Soundpauli/toern/toern.ino

#include "src/toern_build_types.h"

#define VERSION "v3.01f-T2"
extern "C" char *sbrk(int incr);
#define FASTLED_ALLOW_INTERRUPTS 0
// Sketch-local SERIAL8_*_BUFFER_SIZE defines do not resize HardwareSerial8.cpp.
// Real additional buffers are attached in setup(), including Arduino IDE builds.
#define TargetFPS 60

// Playback diagnostics / debug (keep OFF for reliability)
#define DEBUG_PLAYBACK_SERIAL 0  // set to 1 to enable extra playback Serial prints

// Forward declarations to keep Arduino's auto-prototype generator happy
// (it may emit function prototypes that reference these types before they are defined).
struct Mode;

//#define AUDIO_BLOCK_SAMPLES 128
//#define AUDIO_SAMPLE_RATE_EXACT 44100

//STILL FREE PINS: 24, 25, 22, 5, 15, 2, 4, 14, 9, 32, 33, 31
// CLK-OUT J25 = 37, CLK-IN J26 = 38, SIDEC J27 = 28 (rev H 5V analog I/O)
static const int FAST_DROP_BLOCKS = 5;  // ≈25ms @ 44100Hz with 128-sample blocks (reduced from 200ms to minimize trimming)
static int fastDropRemaining = 0;
volatile bool stepIsDue = false;
volatile uint32_t missedSteps = 0;  // counts when loop() hasn't consumed the previous tick yet

// Tiny timer ISR (definition is placed later in the file, after includes, to avoid Arduino
// auto-prototype issues with other callback signatures).
//void playTimerTick();

// === ISR -> main loop deferrals (keep timer interrupt fast and deterministic) ===
// NOTE: These are written from the timer ISR (playNote) and consumed in loop().
volatile bool isrPlayButtonTick = false;      // request drawPlayButton() from main loop (one per beat)
bool pendingPauseUIUpdate = false;            // deferred encoder/LED update after pause (avoid I2C stall)
bool pendingPauseSkipSave = false;            // whether the pending pause should skip autoSave
bool pendingPauseAutoSave = false;            // run autosave on a later loop tick (after pause UI)
volatile bool isrDbgPatternFinished = false;  // song-mode: pattern finished
volatile uint16_t isrDbgPatternFinishedBeat = 0;
volatile bool isrDbgLoopCountChanged = false;  // loopCount incremented
volatile uint16_t isrDbgLoopCountValue = 0;


//#include <Wire.h>x-

#include <cstring>  // For memcmp
#include "src/effect_freeverb_dmabuf.h"
#define USE_WS2812SERIAL   // leds
#include <WS2812Serial.h>  // leds

#include <FastLED.h>  // leds

#include <i2cEncoderLibV2.h>
#include <MIDI.h>
#include <Audio.h>
#include "src/toern_audio_runtime.h"
#include "src/toern_pcm_interpolation.h"
#include "src/toern_legacy_filter.h"
#include <EEPROM.h>
#include <FastTouch.h>
#include <sampler.h>  // TeensyPolyphony arraysampler API
// Adafruit_seesaw uses unqualified `byte`; disambiguate vs C++17 std::byte
#define byte uint8_t
#include "Adafruit_seesaw.h"
#undef byte

#include <Mapf.h>
#include "notes.h"
#include "colors.h"
#include "audioinit.h"
#include "font_3x5.h"
#include "icons.h"

// === Core types (must be defined early for Arduino auto-prototype generation) ===
enum ValueDisplayMode : uint8_t {
  DISPLAY_NUMERIC = 0,
  DISPLAY_ENUM = 1,
};

enum ParameterType : uint8_t {
  DELAY,
  ATTACK,
  HOLD,
  DECAY,
  SUSTAIN,
  RELEASE,
  WAVEFORM,
  TYPE,
};

enum FilterType : uint8_t {
  NULL_,
  HCUT,     // was PASS — same storage slot
  LOWCUT,   // was FREQUENCY — same storage slot
  REVERB,
  BITCRUSHER,
  DETUNE,
  OCTAVE,
  RES,
  RATE,
  AMOUNT,
  OFFSET,
  SPEED,
  PITCH,
  ACTIVE,
  EFX,
  FILTER_WAVEFORM,
};  // Define filter types

enum SynthTypes : uint8_t {
  INSTRUMENT,
  CUTOFF,
  RESONANCE,
  FILTER,
  CENT,
  SEMI,
  FORM,
  LFO_RATE,
  LFO_DEPTH,
  LFO_PHASE,  // repurposed as ARP_SPAN control for ch13/14
  ARP_STEP,
};  // Define synth types

enum MidiSetTypes : uint8_t {
  MIDI_IN_BOOL,
  MIDI_OUT_BOOL,
  SINGLE_OUT_CHANNEL,
  GLOBAL_IN_CHANNEL,
  SEND_CTRL_BOOL,
  RECEIVE_CTRL_BOOL,
};  // Define MIDI setting types

// Define which data array each slider uses
enum SettingArray : uint8_t { ARR_FILTER,
                              ARR_SYNTH,
                              ARR_PARAM,
                              ARR_NONE,
                              ARR_STRETCH };

// Define named struct for sliderDef
struct SliderDefEntry {
  SettingArray arr;
  int8_t idx;
  const char *name;
  uint8_t maxValue;
  uint8_t displayMode;
  const char **enumNames;
  uint8_t displayRange;
};

struct Note {
  uint8_t channel;      // 0 = no note; otherwise, channel / voice id
  uint8_t velocity;     // velocity (0-127)
  uint8_t probability;  // 0-100
  uint8_t condition;    // condition encoding (see codebase)
  uint8_t midiPitch;    // 0..127 = preserved MIDI input pitch; 255 = derive from grid row
} __attribute__((packed));
static_assert(sizeof(Note) == 5, "Note persistence layout must remain packed");

static constexpr uint8_t NOTE_MIDI_PITCH_NONE = 0xFF;
static constexpr uint8_t NOTE_CONDITION_FILL = 21;
static constexpr uint8_t NOTE_CONDITION_GLIDE = 22;
static constexpr uint8_t NOTE_CONDITION_STEP_COUNT = 11;
static const uint8_t noteConditionValues[NOTE_CONDITION_STEP_COUNT] PROGMEM = {
  1, 2, 4, 8, 16, 17, 18, 19, 20, NOTE_CONDITION_FILL, NOTE_CONDITION_GLIDE
};

#define LED_MODULES 2    // Max number of 16x16 matrices that can be chained (hardware limit)
#define MATRIX_WIDTH 16  // Width of each individual matrix
#define maxY 16
#define INT_SD 10

// maxX is now a runtime variable, calculated from ledModules menu setting
extern unsigned int maxX;
extern void handleMidiClock();
extern void handleStart();
#define NUM_LEDS (256 * LED_MODULES)  // 256 LEDs per matrix
#define DATA_PIN 17                   // PIN FOR LEDS
#define INT_PIN 27                    // PIN FOR ENOCDER INTERRUPS

#define SWITCH_1 2 // ALT: 16   // Capacitive input 1 >> SINGLE
#define SWITCH_2 3 // ALT: 3    // Capacitive input 2 >> MENU
#define BUTTON_A 5  // External SINGLE button, active LOW
#define BUTTON_B 22 // External MENU button, active LOW
#define SWITCH_3 4 // ALT: 41  //Pin for TPP223 2 >> REC /
#define SWITCH_4 6   // Capacitive touch4 >> current-voice audition (+ base-pitch note in SINGLE while playing)
#define SWITCH_5 39

// Battery sense on A16 with divider + capacitor.
// Rev G/H: R15 1M (top, VBAT->A16), R19 1.5M (bottom, A16->GND), plus smoothing cap.
#define BATT_ADC_PIN A16
#define BATT_RAW_ZERO 4           // raw reading when pin connected to GND (0V)
#define BATT_RAW_FULL 4095        // raw at 3.3V at pin (12-bit max)
// Nominal divider 1.5/(1.0+1.5)=0.600. Recalibrated on device: meter 4.125V
// read 87% with 0.577 (fw ~4.04V); 0.565 brings that sample to ~4.125V.
#define BATT_DIVIDER_RATIO 0.565f
#define BATT_V_MIN 3.30f          // Display 0% at 3.30V
#define BATT_V_MAX 4.125f         // Display 100% at measured full pack
#define BATT_PCT_CURVE 1.0f       // Linear voltage→%

#define VOL_MIN 1
#define VOL_MAX 10
#define LINEOUT_MIN 13  // SGTL5000 line-out valid range (datasheet: 13..31)
#define LINEOUT_MAX 31
#define BPM_MIN 40
#define BPM_MAX 300

#define GAIN_1 0.4  //0.1;
#define GAIN_2 0.8  //0.33 (increased to 0.8 for 64% total gain)
#define GAIN_3 0.4  //0.25
#define GAIN_4 0.8  //0.2; (increased to 0.8 for 64% total gain)

// ---- Mix headroom (samples ch1-8) ----
// These stages are where hard clipping/crackling happens if too hot:
// - mixer1 sums ch1-4
// - mixer2 sums ch5-8
// - mixer_end sums mixer1 + mixer2 (+ synth + monitoring)
//
// Hard limit per bus: N * MIX_BUS_HEADROOM <= 1.0 (N simultaneous voices on that bank, each at
// full internal level in phase — the theoretical "block" + max velocity case).
// Eight voices total does NOT relax N: e.g. six voices can still be 4+2, so N is still 4 on one bus.
//
// We target typical use: at most 3 sample voices on ch1-4 at once AND at most 3 on ch5-8 (e.g. 3+3=6).
// Then MIX_BUS_HEADROOM = 1/3 keeps each bus <= 1.0; mixer_end still needs 2 * MIX_END <= 1.0.
// If you ever fire 4 samples on one bank at full level together, lower MIX_BUS_HEADROOM to 0.25f.
#define MIX_BUS_HEADROOM (1.0f / 3.0f)  // max ~3 simultaneous sample voices per bank (ch1-4 / ch5-8)
#define MIX_END_SAMPLES_GAIN 0.50f      // mixer_end: mixer1 + mixer2 (each bus can hit 1.0)
#define MIX_END_SYNTH_GAIN 0.60f    // mixer_end input gain for mixersynth_end
// VOL→GAIN: stored 0..20 tenths (UI 0.0–2.0), 10 = current staging (1.0×). Bus × master, so 2.0×2.0 = 4×.
#define MIX_GAIN_UNITY 10
#define MIX_GAIN_MAX 20
#define EEPROM_MIX_GAIN_14 38
#define EEPROM_MIX_GAIN_58 39
#define EEPROM_MIX_GAIN_SYN 40
#define EEPROM_MIX_GAIN_ALL 41


#define NUM_ENCODERS 4
#define defaultVelocity 100
#define FOLDER_MAX 10

#define maxPages 16
#define maxFiles 9
#define NUM_CHANNELS 16
#define maxFilters 15

#define maxfilterResolution 32.0
#define numPulsesForAverage 8  // Number of pulses to average over
#define pulsesPerBar (24 * 4)  // 24 pulses per quarter note, 4 quarter notes per bar

#define EEPROM_MENU_ADDR 42

// Dynamic sample browser (toern_helpers.ino)
extern void sampleBrowserRefreshList(int channel);
extern void sampleBrowserSyncBrowseFromStoredPath(int channel);
extern void sampleBrowserNavigatePress(int channel);
extern void sampleBrowserLastEncoderPress(int channel);
extern void sampleBrowserGoUpPress(int channel);
extern void sampleBrowserClampBrowseIndexAndHardware(int channel);
extern int sampleBrowserBrowseIndexMax(int channel);
extern unsigned long g_setWavIgnoreLoadUntilMs;
extern bool sampleBrowserIsLoadableSelection(int channel);
extern bool shouldSkipVoiceTriggerForSyncPreview(int ch);
extern void triggerSetWavSyncPreview(uint8_t vel);
extern void previewSample(bool setMaxSampleLength);
extern void previewSample(bool setMaxSampleLength, bool playAudio);
extern void previewSampleNow();
extern void serviceSetWavSyncPreview();
extern void serviceSdPreviewRequests();
extern uint16_t g_wavPickCount;
extern uint16_t g_folderPickCount;

struct MidiSettings : public midi ::DefaultSettings {
  static const long BaudRate = 31250;
  static const unsigned SysExMaxSize = 16;
};

MIDI_CREATE_CUSTOM_INSTANCE(HardwareSerial, Serial8, MIDI, MidiSettings);
static uint8_t midiTxExtra[128];
static uint8_t midiRxExtra[512];

unsigned long ganularStartTime = 0;  // Timestamp when the current beat started

#define EXTERNAL_ONE_ENCODER_INDEX 2  // Encoder(2) -> third hardware knob
static bool externalOneBlinkActive = false;
static unsigned long externalOneBlinkUntil = 0;

// Input monitoring toggle state: 0=off, 1=on (y==1 only), 2=all (always on)
// 0 = OFF (dark white helper LEDs)
// 1 = ON (dark green helper LEDs, only when y==1)
// 2 = ALL (dark yellow helper LEDs, always on regardless of y position)
int inputMonitoringState = 0;

void triggerExternalOneBlink();
void updateExternalOneBlink();
void updatePreviewVolume();

#define CLOCK_BUFFER_SIZE 24
//elapsedMillis recFlushTimer;
elapsedMillis recTime;

extern i2cEncoderLibV2 Encoder[NUM_ENCODERS];

bool showChannelNr = true;
bool lastPinsConnected = false;
unsigned long lastChangeTime = 0;
const unsigned long debounceDelay = 500;  // 100ms debounce

#define EEPROM_MAGIC_ADDR 42
#define EEPROM_DATA_START 43        // 43..48 will be your six mode‐bytes
const uint8_t EEPROM_MAGIC = 0x5A;  // anything nonzero


// Add at file scope:

// Extern declarations for menu system
extern int currentMenuPage;

// Function declarations for per-page mute system
bool getMuteState(int channel);
bool getMuteStateForUI(int channel);  // Get mute state for UI display (uses edit page)
void setMuteState(int channel, bool muted);
bool isChildVoiceDisabled(int channel);
bool isChildVoiceMuted(int channel);
void enforceChildModeRestrictions();
void applyMutesAfterPMODSwitch();

// DRAW-R fullMute: stay in draw/single; enc1 enter/exit; enc2/3/4 toggle views in-mode.
enum class FullMuteView : uint8_t { AllMuted = 0, Ch12, Custom, UnmuteAll };

void fullMuteEnter();
void fullMuteExitRestore();
void fullMuteToggleView(FullMuteView target);
void fullMuteApplyView();
bool fullMuteIsActive();
void savePageMutesToGlobal();
void loadGlobalMutesToPage();
void initPageMutes();
void drawIndicator(char size, char colorCode, int encoderNum, bool highlight = false, bool setEncoderLed = true);
void drawFullMuteBorder();
void drawFullMuteIndicators();
void getIndicatorXPositions(int encoderNum, int &x1, int &x2, int &x3);
void updatePongBall();
void drawPongBall();
void resetPongGame();
void showSaveSuccessAnimation(bool returnToDraw = true);
void triggerGridNote(unsigned int globalX, unsigned int y, bool allowMuted = false);
int mapXtoPageOffset(int x);
void stopSound(int note, int ch);
void playSound(int note, int ch, int velocity);
void playSequencedSound(int note, int ch, int velocity, uint32_t tick,
                        bool allowLegato);
void finishSequencedSoundTick(uint32_t tick, bool hadNotes);
void resetSequencedSynthLegato();
void playSequencedSynth(int ch, int b, int vel, uint32_t tick,
                        bool allowLegato, int midiPitchOverride);
void finishSequencedMonoSynthTick(uint32_t tick, bool had13, bool had14);
void stopSynthChannel(int ch);
static inline void resetMidiPressedKeyCount11to14();
void drawCtrlVolumeOverlay(int volume);
void initNeoSlider();
void updateNeoSliderVolume();
void reapplyAllSampleChannelGains();
void resetAllChannelVolumesToDefault();
void extendLastPageForLiveNote(uint16_t targetBeat);
void updateLastPage();
void triggerSamplerVoice(int ch, int pitch, int vel, bool retrigger);
uint8_t scaledNoteVelocity(int ch, int vel);
void updateAllMixerGains();
void forceAllMixerGainsToTarget();
void drawInputGainOverlay(int gain, int maxGain);
void drawChannelNrOverlay(int channelNum, int channelIdx);
void drawPageNrOverlay(int pageNum);
void drawSampleLoadOverlay(uint8_t progressPercent);
bool loadPreviewToChannel(unsigned int targetChannel, bool showLoadProgress = false);
void copySampleToSamplepack0(unsigned int channel, bool showLoadProgress = false);
void saveSp0StateToEEPROM();
void saveSingleModeToEEPROM(int index, int8_t value);
FLASHMEM void flushSettingsBackupNow();
void stopAllSetWavPreviewAudio();
void stopSdPreviewIfPlaying();
void beginChannelSampleReload(unsigned int ch);
void endChannelSampleReload(unsigned int ch);
bool isChannelSampleReloadBusy(unsigned int ch);
size_t sdIoChunkSize();
void sdIoYield();
void sdIoBeginAudioSafe();
void sdIoEndAudioSafe();
bool soloRandomPickPath(char* outRel, size_t outRelSize);
bool soloRandomRenewPlaylist();
bool soloRandomStepPlaylist(int delta);
bool soloRandomBuildPlayPath(const char* stored, char* out, size_t outSz);
bool soloRandomIsPlayableWav(const char* fullPath);
void soloRandomCommitPathToChannel(int ch, const char* fullSdPath);
void soloRandomDropCurrentEntry();
void soloRandomPreviewCurrentVoice();
void soloRandomStepAndPreview(int delta);
const char* soloRandomGetLastPreviewPath();
void soloRandomLoadLastPreview();
static int16_t lastDefaultFastFilterValue[NUM_CHANNELS] = { 0 };  // Changed from int to int16_t (32 bytes saved)

const char *const instTypeNames[] PROGMEM = { "BASS", "KEYS", "CHPT", "PAD", "WOW", "ORG", "FLT", "LEAD", "ARP", "BRSS" };
#define INST_ENUM_COUNT (sizeof(instTypeNames) / sizeof(instTypeNames[0]))

// Add at file scope, after instTypeNames[]
const char *const sndTypeNames[] PROGMEM = { "SAMP" };
const char *const waveformNames[] PROGMEM = { "SIN", "SQR", "SAW", "TRI" };

struct SliderMeta {
  uint8_t maxValue;        // physical encoder range, e.g. 16
  uint8_t displayMode;     // enum or numeric
  const char **enumNames;  // for DISPLAY_ENUM
  uint8_t displayRange;    // NEW: number of distinct display values (e.g. 5, 3)
};


static const SliderMeta sliderMeta[4][4] = {
  // Page 0
  {
    { 32, DISPLAY_NUMERIC, nullptr, 32 },
    { 32, DISPLAY_NUMERIC, nullptr, 32 },
    { 32, DISPLAY_NUMERIC, nullptr, 32 },
    { 32, DISPLAY_NUMERIC, nullptr, 32 } },
  // Page 1
  {
    { 32, DISPLAY_NUMERIC, nullptr, 32 },
    { 32, DISPLAY_NUMERIC, nullptr, 32 },
    { 32, DISPLAY_NUMERIC, nullptr, 32 },
    { 32, DISPLAY_NUMERIC, nullptr, 32 } },
  // Page 2
  {
    { 16, DISPLAY_NUMERIC, nullptr, 5 },     // Shown as 0–4
    { 9, DISPLAY_ENUM, instTypeNames, 10 },  // Mapped from 0–9
    { 32, DISPLAY_NUMERIC, nullptr, 32 },
    { 32, DISPLAY_NUMERIC, nullptr, 32 } },
  // Page 3
  {
    { 32, DISPLAY_NUMERIC, nullptr, 32 },
    { 32, DISPLAY_NUMERIC, nullptr, 32 },
    { 32, DISPLAY_NUMERIC, nullptr, 32 },
    { 32, DISPLAY_NUMERIC, nullptr, 32 } }
};


struct PendingNoteEvent {
  uint8_t channel;
  uint8_t pitch;
  uint8_t velocity;
  unsigned long triggerTime;  // when to trigger
};

std::vector<PendingNoteEvent> pendingSampleNotes;

struct CachedSample {
  char pathRel[128];
  uint32_t lengthBytes;
  uint8_t rate;
  bool valid;
  int plen;
};

CachedSample previewCache;

// Flag to disable threshold from external code
bool disableThresholdFlag = false;

// Number of samples in each delay line
// Allocate the delay lines for left and right channels

bool MIDI_CLOCK_SEND = true;
bool MIDI_NOTE_SEND = true;    // Control whether MIDI notes are sent (independent from clock)
bool MIDI_NOTE_RECEIVE = true; // Control whether incoming MIDI notes are acted on
bool MIDI_NOTE_CLAMP = true;   // Fold incoming pitch into rows 1..15; OFF preserves absolute MIDI pitch

bool MIDI_TRANSPORT_RECEIVE = true;
bool MIDI_TRANSPORT_SEND = false;
int8_t transportSendDelayMs = 17;   // -127..+127 ms, MENU>MIDI>SYNC SNC1 (see toern_midi effective* helpers)
int8_t transportRcveDelayMs = 17; // -127..+127 ms SNC2: + = delay that path; − = delay the other path
bool MIDI_VOICE_SELECT = false;
bool SMP_PATTERN_MODE = false;
bool SMP_FLOW_MODE = false;      // FLOW mode: follows timer position when playing
bool voiceMode = false;          // VMOD: each channel loops its own pages
bool imageMode = false;          // IMG: black matrix; paint cycles voice/color from voice1
int imgBrushChannel = 1;         // IMG: selected brush voice/color (1–8); touch1 cycles
uint8_t eyesMode = 1;            // ETC EYES: 0=OFF, 1=1min, 2=5min, 3=15min idle before screensaver
uint8_t fireVoice = 0;           // ETC FIRE: 0 off, 15 all voices, else 1–8 / 11 / 13 / 14
uint8_t fireLevel = 8;           // ETC FIRE: encoder 2 particle count, 1–25
uint8_t fireSize = 1;            // ETC FIRE: encoder 1 particle size, 1–4
uint8_t fireGravity = 0;         // ETC FIRE: 0 drifts sideways, 8 pulls hard toward playhead
uint8_t fireColor = 8;           // ETC FIRE: 0 white, 8 full voice colour
uint8_t fireFocus = 0;           // encoder 3 edits 0 voice, 1 gravity, 2 colour
uint8_t voicePageLen[16] = {0};  // highest page that contains this channel (0 = empty)
uint16_t voicePageMask[16] = {0};
uint16_t voiceRowMask[16] = {0}; // bit (row-1) if this channel has any note on that row
uint8_t voiceModePages = 1;      // longest voice, at least 1
uint16_t voiceLoopCount[16] = {0};
uint8_t voiceEditPage[16] = {0}; // per-voice edit page (2nd encoder), 0 = page 1
int8_t voicePageOffset[16] = {0}; // added to the global page so the 2nd encoder can cue one voice
static bool spkrEnabled = true;  // SPKR toggle state (ON by default)
static bool childLockEnabled = false;  // Child lock: requires touch2->touch1 sequence to enter menu
static bool bootFullResetRequested = false;  // Touch1 held 10s at power-on (3s CLR + 7s more) → FULL reset late in setup()
unsigned int lastFlowPage = 0;   // Track the last page set by FLOW mode
bool recMenuFirstEnter = true;   // Track first entry into REC menu
unsigned int SMP_FAST_REC = false;
unsigned int SMP_REC_CHANNEL_CLEAR = true;
bool SMP_LOAD_SETTINGS = true;  // Whether to load SMP settings when loading tracks
uint8_t lineOutLevelSetting = 30;

bool pendingStartOnBar = false;  // "I hit Play, now wait for bar-1"



bool drawNoSD_hasRun = false;


struct PendingNote {
  uint8_t pitch;
  uint8_t velocity;
  uint8_t channel;
  uint8_t livenote;
  uint16_t targetBeat;
};

// A small FIFO for upcoming grid-writes.
// IMPORTANT: `playNote()` runs in an IntervalTimer ISR, so this queue must be ISR-safe.
// Use a fixed-size single-producer (loop/MIDI) single-consumer (ISR/onBeatTick) ring buffer.
static constexpr uint8_t MAX_PENDING_NOTES = 32;
DMAMEM static PendingNote pendingNotesBuf[MAX_PENDING_NOTES];
static volatile uint8_t pendingNotesHead = 0;   // next write index
static volatile uint8_t pendingNotesTail = 0;   // next read index
static volatile uint8_t pendingNotesCount = 0;  // number of queued items

// If a live MIDI/touch4 write lands on the upcoming sequencer step, skip that
// one trigger so the immediate preview is the only attack. The cell is already
// on the grid (visible now) and plays on the next pass.
volatile uint16_t liveRecordSkipBeat = 0;
volatile uint16_t liveRecordSkipRows = 0;

// Enqueue from main loop context (may be called from MIDI handlers in loop()).
// Returns true on success, false if the queue is full (event dropped).
bool enqueuePendingNote(uint8_t pitch, uint8_t velocity, uint8_t channel, uint8_t livenote) {
  if (isChildVoiceDisabled((int)channel)) return false;
  extern uint16_t quantizedMidiRecordBeat();
  uint16_t targetBeat = quantizedMidiRecordBeat();

  bool ok = false;
  noInterrupts();
  if (pendingNotesCount < MAX_PENDING_NOTES) {
    pendingNotesBuf[pendingNotesHead] = {
      pitch, velocity, channel, livenote, targetBeat
    };
    pendingNotesHead = (uint8_t)((pendingNotesHead + 1) % MAX_PENDING_NOTES);
    pendingNotesCount++;
    ok = true;
  }
  interrupts();
  return ok;
}

// Dequeue from ISR context (`onBeatTick()` runs inside `playNote()` ISR).
// Returns true if an item was dequeued.
bool dequeuePendingNote(PendingNote &out) {
  if (pendingNotesCount == 0) return false;
  out = pendingNotesBuf[pendingNotesTail];
  pendingNotesTail = (uint8_t)((pendingNotesTail + 1) % MAX_PENDING_NOTES);
  pendingNotesCount--;
  return true;
}

void clearPendingMidiRecordNotes() {
  noInterrupts();
  pendingNotesHead = 0;
  pendingNotesTail = 0;
  pendingNotesCount = 0;
  liveRecordSkipBeat = 0;
  liveRecordSkipRows = 0;
  interrupts();
}

static void markLiveRecordSkip(uint16_t targetBeat, uint8_t row) {
  extern unsigned int beat;
  noInterrupts();
  uint16_t upcoming = (uint16_t)beat;
  if (targetBeat == upcoming && row >= 1 && row <= 15) {
    if (liveRecordSkipBeat != targetBeat) {
      liveRecordSkipBeat = targetBeat;
      liveRecordSkipRows = 0;
    }
    liveRecordSkipRows |= (uint16_t)(1u << row);
  }
  interrupts();
}

static bool consumeLiveRecordSkip(uint16_t srcBeat, unsigned int row) {
  if (liveRecordSkipBeat != srcBeat || row > 15) return false;
  uint16_t bit = (uint16_t)(1u << row);
  if ((liveRecordSkipRows & bit) == 0) return false;
  liveRecordSkipRows = (uint16_t)(liveRecordSkipRows & ~bit);
  if (liveRecordSkipRows == 0) liveRecordSkipBeat = 0;
  return true;
}

// Write a live-recorded note immediately so SINGLE/DRAW can show it, without
// waiting for the next sequencer tick. Skip-once covers the current playhead.
bool placeLiveGridNote(uint8_t channel, uint8_t row, uint8_t velocity,
                       uint8_t midiPitch, bool protectOtherVoices) {
  extern Note note[][maxY + 1];
  if (channel < 1 || row < 1 || row > 15) return false;
  if (isChildVoiceDisabled((int)channel)) return false;
  extern uint16_t quantizedMidiRecordBeat();
  uint16_t targetBeat = quantizedMidiRecordBeat();
  if (targetBeat < 1) return false;
  Note &cell = note[targetBeat][row];
  if (protectOtherVoices && cell.channel != 0 && cell.channel != channel) {
    return false;
  }
  markLiveRecordSkip(targetBeat, row);
  cell.velocity = velocity > 0 ? velocity : (uint8_t)defaultVelocity;
  cell.probability = 100;
  cell.condition = 1;
  cell.midiPitch = midiPitch;
  cell.channel = channel;
  // Do not full-scan EXTMEM here: updateLastPage() briefly publishes lastPage=0
  // (and understated mid-scan values) that the playNote ISR can treat as a wrap
  // to beat 1 when many MIDI notes land while playing.
  extendLastPageForLiveNote(targetBeat);
  return true;
}


// ----- Intro Animation Timing (in ms) -----
// Boot: 1s sine fade-in, 2.5s logo fade-in, 1.5s combined fade-out = 5s.
const unsigned long phase1Duration = 1000;
const unsigned long phase2Duration = 2500;
const unsigned long phase3Duration = 1500;
const unsigned long totalAnimationTime =
    phase1Duration + phase2Duration + phase3Duration;
bool filterfreshsetted = true;

DMAMEM bool activeNotes[128] = { false };  // Track active MIDI notes (0-127)
DMAMEM int16_t midiHeldCh11SoundNote[128] = {}; // Exact live voice identity for matching Note Off
DMAMEM uint8_t sequencerMidiOutPitch[16] = {};
DMAMEM uint8_t sequencerMidiOutChannel[16] = {};
uint8_t sequencerMidiOutCount = 0;

float rateFactor = 44117.0 / 44100.0;


unsigned int infoIndex = 0;

// Sample paths for SP0 / SET_WAV are stored in SMP.samplePathRel[] (relative to samples/).
bool freshPaint, tmpMute = false;
bool preventPaintUnpaint = false;  // Flag to prevent paint/unpaint after certain operations
unsigned long suppressDrawRMuteUntilMs = 0;  // Ignore R-mode mute events during velocity enter/exit


bool firstcheck = false;
bool nofile = false;
char *currentParam = "DLAY";
char *currentFilter = "TYPE";
char *currentSynth = "BASS";
unsigned int fxType = 0;

unsigned int selectedFX = 0;


unsigned long filterDrawEndTime = 0;
bool filterDrawActive = false;
int filterDrawValue = 0;
CRGB filterDrawColor = CRGB::White;


unsigned long patternChangeTime = 0;
bool patternChangeActive = false;



// Replaced String with hash for memory efficiency (~100-200 bytes saved)
uint32_t oldPosHash = 0;
uint8_t oldButtons[NUM_ENCODERS] = { 0, 0, 0, 0 };  // Changed from int to uint8_t (4 bytes saved per element)

unsigned long playStartTime = 0;  // To track when play(true) was last called

bool previewIsPlaying = false;
extern bool g_previewUseLivePeaks;

const int maxPeaks = 512;  // Adjust based on your needs
DMAMEM float peakValues[maxPeaks];
int peakIndex = 0;


const int maxRecPeaks = 512;  // Adjust based on your needs
DMAMEM float peakRecValues[maxRecPeaks];
int peakRecIndex = 0;



uint8_t ledBrightness = 83;
bool drawBaseColorMode = true;  // true = channel colors, false = black
bool pong = false;
const long ram = 15728640;                               // 15MB EXTRAM for sounds (was 12582912/12MB); ~1707KB/slot ~19.8s/voice @ 44.1kHz mono 16-bit
const unsigned int MAX_STEPS = MATRIX_WIDTH * maxPages;  // Fixed total steps (16 pages * 16 cols = 256)
const unsigned int maxlen = MAX_STEPS + 1;               // Note array width (1-based)
const unsigned int SONG_LEN = MAX_STEPS;                 // Song length equals total steps

static bool lastBothTouched = false;
DMAMEM bool touchState[4] = { false };      // Current touch state (HIGH/LOW)
DMAMEM bool lastTouchState[4] = { false };  // Previous touch state
const int touchThreshold = 45; //45 for M1
// Rec (SWITCH_3) is polled every tight-loop tick while FastRec is active.
// Debounce in time at the same threshold as the other pads — a wide Schmitt
// (OFF=28) never unlatched because idle FastTouch often sits at 30–44.
static const unsigned long REC_TOUCH_PRESS_MS = 20;
static const unsigned long REC_TOUCH_RELEASE_MS = 40;
static bool bypassModeSwitchDebounce = false;
static bool touch1ModeTogglePending = false;
static bool touch1ModeToggleToSingle = false;
static unsigned long touch1ModeToggleDueMs = 0;
static const unsigned long TOUCH1_CHORD_GRACE_MS = 140;

/** true: use grounded buttons A/B; false: use capacitive SWITCH_1/2. */
static const bool exttouch = false;
/** When false, skip all NeoSlider I2C (init/ADC/LEDs/slew). This unit has faders. */
static const bool deviceHasFaders = exttouch;

bool readTouch1Pressed() {
  if (exttouch) return digitalReadFast(BUTTON_A) == LOW;
  return fastTouchRead(SWITCH_1) > touchThreshold;
}

bool readTouch2Pressed() {
  if (exttouch) return digitalReadFast(BUTTON_B) == LOW;
  return fastTouchRead(SWITCH_2) > touchThreshold;
}

bool readRecTouchHeld() {
  static bool latched = false;
  static bool timing = false;
  static unsigned long disagreeSince = 0;
  const bool raw = fastTouchRead(SWITCH_3) > touchThreshold;
  const unsigned long now = millis();
  if (raw == latched) {
    timing = false;
    return latched;
  }
  if (!timing) {
    timing = true;
    disagreeSince = now;
  }
  const unsigned long need = latched ? REC_TOUCH_RELEASE_MS : REC_TOUCH_PRESS_MS;
  if ((now - disagreeSince) >= need) {
    latched = raw;
    timing = false;
  }
  return latched;
}

const unsigned int totalPulsesToWait = pulsesPerBar * 2;

const unsigned long CHECK_INTERVAL = 50;  // Interval to check buttons in ms
unsigned long lastCheckTime = 0;          // Get the current time


// Recording input mode:
//   1  = MIC (SGTL5000 capture/mic path enabled)
//  -1  = LINEIN (MIC/capture path disabled)
int recMode = -1;
unsigned int fastRecMode = 0;
unsigned int previewVol = 20;  // Default 20 (0-50 range, 0.00-0.50)
uint8_t mixGain14 = MIX_GAIN_UNITY;     // VOL→GAIN: mixer1 (voices 1–4)
uint8_t mixGain58 = MIX_GAIN_UNITY;     // mixer2 (voices 5–8)
uint8_t mixGainSynth = MIX_GAIN_UNITY;  // mixer_end synth bus (ch11/13/14)
uint8_t mixGainMaster = MIX_GAIN_UNITY; // scales 1–4, 5–8, and synth together
// Preview trigger mode: 0 = auto on selection/seek, 1 = encoder(0) press only, 2 = in-sync with voice triggers
extern const int PREVIEW_MODE_ON = 0;
extern const int PREVIEW_MODE_PRESS = 1;
extern const int PREVIEW_MODE_SYNC = 2;
int previewTriggerMode = PREVIEW_MODE_ON;
int recChannelClear = 1;  // 0=OFF (add triggers), 1=ON (clear then add), 2=FIX (no manipulation), 3=ON1 (count-in then record on beat 1), 4=CLIC (touch3 adds trigger at current beat)
int transportMode = 1;
int midiSendMode = 2;  // 0=CLCK, 1=NOTE, 2=BOTH (default to BOTH)
int patternMode = -1;
int flowMode = -1;  // FLOW setting: -1 = OFF, 1 = ON
int clockMode = 1;
int voiceSelect = 1;
int simpleNotesView = 1;               // Simple notes view: 1=EASY, 2=FULL
int loopLength = 0;                    // Loop length: 0=OFF, 1-8=force pattern length
int ledModules = 1;                    // Number of LED modules: 1 or 2
bool ledModulesRotated = false;        // LED panel orientation flag: false=normal, true=rotated compensation
unsigned int maxX = MATRIX_WIDTH * 1;  // Runtime variable: total display width (16 or 32)
unsigned int micGain = 0;              // Microphone gain: 0-64, default 10
unsigned int lineInLevel = 8;          // Line input level: 0-15, default 8
int ctrlMode = 0;                      // 0=page, 1=volume control for encoder 1
static int ctrlLastChannel = -1;
static int ctrlLastVolume = -1;
static bool ctrlVolumeOverlayActive = false;
// Remember per-channel volume before muting, so unmute can restore it (CTRL=VOL workflow)
DMAMEM static uint8_t lastChannelVolBeforeMute[maxY] = { 0 };
static unsigned long ctrlVolumeOverlayUntil = 0;
static int ctrlVolumeOverlayValue = 0;
static bool inputGainOverlayActive = false;
static unsigned long inputGainOverlayUntil = 0;
static int inputGainOverlayValue = 0;
static int inputGainOverlayMax = 63;

static bool channelNrOverlayActive = false;
static unsigned long channelNrOverlayUntil = 0;
static int channelNrOverlayChannel = 0;
static bool pageNrOverlayActive = false;
static unsigned long pageNrOverlayUntil = 0;
static int pageNrOverlayPage = 0;
static const int DEFAULT_CHANNEL_VOLUME = 16;  // 100% of CTRL=VOL (0–16)

// Get SPKR enabled state
bool getSpkrEnabled() {
  return spkrEnabled;
}

// Set SPKR enabled state and update pin 30
void setSpkrEnabled(bool enabled) {
  spkrEnabled = enabled;
  pinMode(30, OUTPUT);                     // Switch to OUTPUT mode to control the pin
  digitalWrite(30, enabled ? LOW : HIGH);  // ON = LOW, OFF = HIGH
}

// Get child lock enabled state
bool getChildLockEnabled() {
  return childLockEnabled;
}

// Set child lock enabled state
void setChildLockEnabled(bool enabled) {
  childLockEnabled = enabled;
  enforceChildModeRestrictions();
}

bool isRecording = false;
File frec;

#define MAXREC_SECONDS 12
#define BUFFER_SAMPLES (22100 * MAXREC_SECONDS)
#define BUFFER_BYTES (BUFFER_SAMPLES * sizeof(int16_t))

EXTMEM int16_t recBuffer[BUFFER_SAMPLES];
volatile size_t recWriteIndex = 0;


// Which input on the audio shield will be used?
// Default to LINEIN so the SGTL5000 MIC/capture path is not powered by default.
unsigned int recInput = AUDIO_INPUT_LINEIN;

/*timers*/
unsigned int lastButtonPressTime = 0;
bool resetTimerActive = false;

// runtime
//  variables for program logic
float pulse = 1;
int dir = 1;
unsigned int MIDI_CH = 1;
double playNoteInterval = 150000.0;
// Display refresh timing: RefreshTime = 1000UL / TargetFPS (30 FPS = 33ms per frame)
// This is the single source of truth for display-related timing across the codebase
unsigned int RefreshTime = 1000UL / TargetFPS;
float marqueePos = maxX;
bool shifted = false;
bool movingForward = true;  // Variable to track the direction of movement
unsigned int lastUpdate = 0;
unsigned int lastDrawUpdate = 0;  // UI redraw limiter (separate from LED show limiter)

unsigned int totalInterval = 0;


DMAMEM bool hasNotes[maxPages + 1];
DMAMEM unsigned int startTime[maxY] = { 0 };    // Variable to store the start time
DMAMEM bool noteOnTriggered[maxY] = { false };  // Flag to indicate if noteOn has been triggered
DMAMEM bool persistentNoteOn[maxY] = { false };
DMAMEM int16_t pressedKeyCount[maxY] = { 0 };  // Changed from int to int16_t
DMAMEM uint32_t sequencedMonoSynthLastTick[maxY] = { 0 };
DMAMEM int16_t sequencedMonoSynthLastPitch[maxY] = { 0 };
DMAMEM bool sequencedMonoSynthActive[maxY] = { false };

bool waitForFourBars = false;
unsigned int pulseCount = 0;
bool sampleIsLoaded = false;
bool unpaintMode, paintMode = false;

// Rows that should never accept painted notes in draw/single modes.
// (User-reported: y=9,10,12 were incorrectly paintable when paintMode=true.)
static inline bool isPaintableDrawRow(unsigned int y) {
  // Draw-mode: row 16 reserved for UI/copy, row 1 is special UI row.
  if (y <= 1 || y > 15) return false;
  // Reserved rows in normal DRAW (map to blocked channels 9/10/12).
  // IMG paints voice/color independently of Y, so allow the full y=2..15 plane.
  if (!imageMode && (y == 10 || y == 11 || y == 13)) return false;
  return true;
}

static inline bool isSingleModeChannelAllowed(int channel) {
  return (channel >= 1 && channel <= 8) ||
         channel == 11 || channel == 13 || channel == 14;
}

// Row used as the voice's "natural" / base pitch (DRAW home row / MIDI anchor).
static inline int basePitchRowForChannel(int channel) {
  if (channel >= 1 && channel <= 8) return channel + 1;
  if (channel == 11) return 12;
  if (channel == 13 || channel == 14) return channel - 11;  // ch13→2, ch14→3
  return -1;
}

// IMG mode: empty cell → voice 1; re-paint advances through voices 1–8 and wraps.
// Selecting / cycling to a voice always unmutes it.
static inline int imageModePaintChannel(int existingChannel) {
  static const int seq[] = { 1, 2, 3, 4, 5, 6, 7, 8 };
  const int n = (int)(sizeof(seq) / sizeof(seq[0]));
  int start = 0;
  if (existingChannel > 0) {
    for (int i = 0; i < n; i++) {
      if (seq[i] == existingChannel) {
        start = (i + 1) % n;
        break;
      }
    }
  }
  for (int k = 0; k < n; k++) {
    int ch = seq[(start + k) % n];
    if (!isChildVoiceDisabled(ch)) {
      setMuteState(ch, false);
      return ch;
    }
  }
  setMuteState(1, false);
  return 1;
}

static inline bool canEnterSingleMode(unsigned int y, int channel) {
  if (imageMode) return false;  // IMG: single mode disabled
  return y < 16 &&
         isSingleModeChannelAllowed(channel) &&
         !isChildVoiceDisabled(channel);
}

void enforceImageModeConstraints();


// Global sequencer position (1..maxlen)
unsigned int beat = 1;
volatile uint16_t sequencerRecordBeat = 1;
volatile uint16_t sequencerPreviousRecordBeat = 1;
volatile uint32_t sequencerRecordStepStartedUs = 0;
volatile uint32_t sequencerRecordStepDurationUs = 150000;
uint32_t sequencerSynthTick = 0;
// Beat index that was last used for audio playback / sequencing.
// UI components should use this to stay visually in sync with what was just played.
unsigned int beatForUI = 1;

uint16_t quantizedMidiRecordBeat() {
  uint16_t playedBeat;
  uint16_t upcomingBeat;
  uint32_t startedUs;
  uint32_t durationUs;
  noInterrupts();
  playedBeat = sequencerRecordBeat;
  upcomingBeat = (uint16_t)beat;
  startedUs = sequencerRecordStepStartedUs;
  durationUs = sequencerRecordStepDurationUs;
  interrupts();

  if (startedUs == 0 || durationUs == 0) return upcomingBeat;
  uint32_t elapsed = micros() - startedUs;
  // Nearest-step quantization: the first half of a step belongs to the beat
  // the player just heard; the second half anticipates the upcoming beat.
  return elapsed < (durationUs / 2u) ? playedBeat : upcomingBeat;
}
// Loop counter for condition feature (increments when beat resets to 1)
uint16_t loopCount = 0;
unsigned int samplePackID, fileID = 1;
EXTMEM unsigned int lastPreviewedSample[FOLDER_MAX] = {};
IntervalTimer playTimer;
IntervalTimer midiClockTimer;
IntervalTimer fillTimer;  // Timer for fill triggers (runs at 4x beat rate)
//IntervalTimer midiTimer;

// Fill timer state - tracks sub-beat position (0-3 for 4x rate)
volatile unsigned int fillSubBeat = 0;
// Monotonic sub-tick for fill timing (increments in playFillNote ISR; independent of pattern looping).
// 4 sub-ticks = 1 sequencer step ("beat" in this code).
volatile uint32_t fillSubTick = 0;
// Fill state machine:
// - fillRunning: fill currently playing
// - fillHasTriggered: legacy lockout (kept for pause/stop clears); normal completion
//   demotes the F/F trigger note to 1/1 and clears lockout so re-setting F/F re-arms.
volatile bool fillRunning = false;
volatile bool fillHasTriggered = false;
volatile uint32_t fillStartSubTick = 0;  // sub-tick when fill started
// Grid cell that armed the current/last fill (1-based step + row).
volatile unsigned int fillTriggerStep = 0;
volatile unsigned int fillTriggerRow = 0;
// Active fill playback parameters (copied from triggering note).
volatile int fillActiveChannel = 0;
volatile int fillActiveVelocity = 0;
volatile unsigned int fillActiveRow = 0;
volatile uint8_t fillActiveMidiPitch = NOTE_MIDI_PITCH_NONE;
unsigned int lastPage = 1;
int editpage = 1;
EXTMEM Note note[maxlen + 1][maxY + 1] = {};
EXTMEM Note tmp[maxlen + 1][maxY + 1] = {};
EXTMEM Note original[maxlen + 1][maxY + 1] = {};
EXTMEM Note pageTmp[(MATRIX_WIDTH * 2) + 1][maxY + 1] = {};

EXTMEM unsigned int sample_len[maxFiles];
bool sampleLengthSet = false;

bool isNowPlaying = false;  // global

// Screensaver idle timer; delay from ETC→EYES (1/5/15 min). Reset on encoder / button / touch / menu.
uint32_t lastUserActivityMs = 0;
FLASHMEM void noteUserActivity() {
  lastUserActivityMs = millis();
}

int PrevSampleRate = 1;
EXTMEM int SampleRate[maxFiles] = { 1, 1, 1, 1, 1, 1, 1, 1, 1 };
EXTMEM unsigned char sampled[maxFiles][ram / (maxFiles)];
static const uint32_t MAX_SAMPLES = sizeof(sampled[0]) / sizeof(sampled[0][0]);
// Fastrec writes int16 into sampled[ch]. 12s @ 44.1 kHz (double the old ~6s BUFFER_SAMPLES
// cap); never past the voice slot (~19.8s).
static const size_t FASTREC_SLOT_SAMPLES = sizeof(sampled[0]) / sizeof(int16_t);
static const size_t FASTREC_MAX_SECONDS = 12;
static const size_t FASTREC_MAX_SAMPLES =
    ((size_t)44100 * FASTREC_MAX_SECONDS < FASTREC_SLOT_SAMPLES)
        ? ((size_t)44100 * FASTREC_MAX_SECONDS)
        : FASTREC_SLOT_SAMPLES;




elapsedMillis msecs;
elapsedMillis mRecsecs;
elapsedMillis diagStatsTimer;


DMAMEM CRGB leds[NUM_LEDS];

enum ButtonState {
  IDLE,
  LONG_PRESSED,
  RELEASED
};

const int ALL_CHANNELS[] = { 1, 2, 3, 4, 5, 6, 7, 8, 11, 13, 14 };
const int NUM_ALL_CHANNELS = sizeof(ALL_CHANNELS) / sizeof(ALL_CHANNELS[0]);


struct Mode {
  String name;
  unsigned int minValues[4];
  unsigned int maxValues[4];
  unsigned int pos[4];
  uint32_t knobcolor[4];
};

Mode draw = { "DRAW", { 1, 1, 0, 1 }, { maxY, maxPages, maxfilterResolution, maxlen - 1 }, { 1, maxY, maxfilterResolution, 1 }, { 0x110011, 0x000000, 0x00FF00, 0x110011 } };
Mode singleMode = { "SINGLE", { 1, 1, 0, 1 }, { maxY, maxPages, maxfilterResolution, maxlen - 1 }, { 1, 2, maxfilterResolution, 1 }, { 0x000000, 0x000000, 0x00FF00, 0x000000 } };
Mode volume_bpm = { "VOLUME_BPM", { 11, 0, 0, BPM_MIN }, { 30, 252, 1, BPM_MAX }, { 11, 0, 0, 100 }, { 0x000000, 0x000000, 0xFF4400, 0x00FFFF } };  // BPM only - volume controls removed, encoder[2] for INT/EXT, encoder[1] for brightness (0-252 = 3-255)
//filtermode has 4 entries
Mode filterMode = { "FILTERMODE", { 0, 0, 0, 0 }, { maxfilterResolution, maxfilterResolution, maxfilterResolution, maxfilterResolution }, { 1, 1, 1, 1 }, { 0x00FFFF, 0xFF00FF, 0xFFFF00, 0x00FF00 } };
Mode noteShift = { "NOTE_SHIFT", { 7, 7, 0, 7 }, { 9, 9, maxfilterResolution, 9 }, { 8, 8, maxfilterResolution, 8 }, { 0xFFFF00, 0xFFFF00, 0x000000, 0xFFFFFF } };
Mode velocity = { "VELOCITY", { 1, 1, 1, 0 }, { maxY, 5, NOTE_CONDITION_STEP_COUNT, maxY }, { maxY, 5, 1, 10 }, { 0xFF4400, 0x00FF88, 0x888888, 0x0044FF } };

Mode set_Wav = { "SET_WAV", { 1, 0, 1, 1 }, { 9999, 999, 9999, 999 }, { 0, 0, 0, 1 }, { 0x000000, 0x000000, 0x00FF00, 0xFFFFFF } };  // pos[3]=combined browser selection
Mode recordMode = { "RECORD_MODE", { 0, 1, 1, 1 }, { 100, FOLDER_MAX, 9999, 999 }, { 0, 0, 0, 1 }, { 0xFF0000, 0x00FF00, 0x0000FF, 0x000000 } };
Mode set_SamplePack = { "SET_SAMPLEPACK", { 1, 1, 1, 0 }, { 1, 1, 99, 999 }, { 1, 1, 1, 1 }, { 0x00FF00, 0xFF0000, 0x000000, 0x0000FF } };
// FILE slot 0 = autosaved.txt (load-only); slots 1..999 = normal pattern files
Mode loadSaveTrack = { "LOADSAVE_TRACK", { 1, 1, 0, 0 }, { 1, 1, 1, 999 }, { 1, 1, 1, 1 }, { 0x00FF00, 0xFF0000, 0x000000, 0x0000FF } };
// pos[2] max 255: MIDI SYNC (45) stores transport delay as 0..254 = −127..+127 via offset 127
Mode menu = { "MENU", { 1, 1, 0, 0 }, { 1, 1, 255, 16 }, { 1, 1, 10, 1 }, { 0x000000, 0x000000, 0x000000, 0x00FF00 } };
// NEW: enc0=load (press), enc1=length, enc2=template, enc3=back to FILE (blue like FILE menu)
Mode newFileMode = { "NEW_FILE", { 0, 1, 0, 0 }, { 0, 16, 5, 0 }, { 0, 8, 0, 0 }, { 0x00FF00, 0xFF00FF, 0xFFFF00, 0x0000FF } };
Mode subpatternMode = { "SUBPATTERN", { 1, 0, 0, 1 }, { 1, 7, maxfilterResolution, 1 }, { 1, 1, maxfilterResolution, 1 }, { 0xFF00FF, 0x00FFFF, 0x000000, 0xFF00FF } };
Mode songMode = { "SONGMODE", { 1, 1, 1, 1 }, { 1, 16, 1, 64 }, { 1, 1, 1, 1 }, { 0x000000, 0xFF00FF, 0x000000, 0xFFFF00 } };
// Declare currentMode as a global variable (start in draw so boot limits are sane)
Mode *currentMode = &draw;
Mode *oldMode = &draw;
Mode *muteModeReturn = nullptr;
bool muteModeActive = false;
bool muteModeRingsDirty = false;  // rewrite solo encoder RGB once per enter / channel change
bool muteModeReturnSingleState = false;
int muteModeLastChannel = -1;
int8_t muteModeArrowDirection = 0;
unsigned long muteModeArrowUntil = 0;
uint8_t muteModeEncoderValue = 0;
int8_t soloRandomArrowDirection = 0;  // -1 / +1 while scrolling random playlist
unsigned long soloRandomArrowUntil = 0;

static void refreshSamplerChannel(uint8_t channel);
static void reverseChannelInMemory(uint8_t channel);
static void applyChannelDirection(uint8_t channel, int8_t targetDir);

// Song arrangement data: 64 positions, each holds a pattern number (1-16, or 0 for empty)
// Using SMP.songArrangement instead to save RAM1 (64 bytes saved)
bool songModeActive = false;  // When true, playback follows song arrangement
int currentSongPosition = 0;  // Current position in song arrangement (0-63), -1 = none

// NEXT mode UI indicator. Playback reads GLOB.edit at the page boundary so
// both page-selection encoders always target the page currently visible.
unsigned int pendingPage = 0;  // 0 = visible page is already playing


struct Sample {
  // Sample browser: fileID = 1-based index in current combined browse list; oldID unused (0)
  unsigned int oldID : 10;
  unsigned int fileID : 10;
} __attribute__((packed));


// Declare the device struct
struct Device {
  // File/Pattern specific variables
  float bpm;             // bpm
  unsigned int file;     // current selected save/load id
  unsigned int pack;     // current selected samplepack id
  Sample wav[maxFiles];  // current selected sample (oldID/fileID = UI list state)
  char samplePathRel[maxFiles][128];  // path under samples/ incl. .wav (empty = use pack slot)
  float param_settings[maxY][maxFilters];
  float filter_settings[maxY][maxFilters];
  float synth_settings[maxY][11];
  unsigned int mute[maxY];
  unsigned int channelVol[maxY];
  // Mute system for PMOD
  bool globalMutes[maxY];          // Global mute states (when PMOD is off)
  bool pageMutes[maxPages][maxY];  // Page-specific mute states (when PMOD is on)
  // Samplepack 0 tracking - which voices have individually loaded samples
  bool sp0Active[maxFiles];  // Track which voices are using samplepack 0
  // Song arrangement - which pattern plays at each position
  uint8_t songArrangement[64];  // Song arrangement: 64 positions, each holds pattern 1-16 (or 0 for empty)
};

// Global variables struct
struct GlobalVars {
  unsigned int singleMode;  // single Sample Mod
  unsigned int currentChannel;
  unsigned int vol;          // volume
  unsigned int velocity;     // velocity
  unsigned int page;         // current page
  unsigned int edit;         // edit mode or plaing mode?
  unsigned int folder;       // current selected folder id
  bool activeCopy;           // is copy/paste active?
  unsigned int copyChannel;  // channel that was copied (for cross-channel paste)
  unsigned int x;            // cursor X
  unsigned int y;            // cursor Y
  unsigned int seek;         // skipped into sample
  unsigned int seekEnd;
  unsigned int smplen;      // overall selected samplelength
  unsigned int shiftX;      // note Shift
  unsigned int shiftY;      // note Shift
  unsigned int shiftY1;     // note Shift for encoder 1 (current channel and page only)
  unsigned int subpattern;  // current subpattern (0-15)
};

DMAMEM float octave[2];

// Sample voices 1-8: detune = fine semis (−1..+1); channelOctave = whole semis (−24..+24).
DMAMEM float detune[13];  // Index 0 unused; 1-8 fine tune, 9-12 legacy
DMAMEM float channelOctave[9];  // Index 0 unused; 1-8 OCTV whole-semitone offset

//#define GRANULAR_MEMORY_SIZE 95280  // enough for 800 ms at 44.1 kHz
//DMAMEM int16_t granularMemory[GRANULAR_MEMORY_SIZE];


// in the same file, before tmpMuteAll:





//EXTMEM?
EXTMEM Device SMP = {
  100.0,  //bpm
  1,      //file
  1,      //pack
  // wav preset: folder 0, file index = channel (1..8)
  { { 0, 1 }, { 0, 1 }, { 0, 2 }, { 0, 3 }, { 0, 4 }, { 0, 5 }, { 0, 6 }, { 0, 7 }, { 0, 8 } },
  {{0}},                                                              // samplePathRel
  {},                                                                 //param_settings
  {},                                                                 //filter_settings
  {},                                                                 //synth_settings
  {},                                                                 //mute
  { 16, 16, 16, 16, 16, 16, 16, 16, 16, 16, 16, 16, 16, 16, 16, 16 }  //channelVol
};

GlobalVars GLOB = {
  false,  //singleMode
  1,      //currentChannel
  10,     //volume
  10,     //velocity
  1,      //page
  1,      //edit
  0,      //folder
  false,  //activeCopy
  1,      //x
  2,      //y
  0,      //seek
  0,      //seekEnd
  0,      //smplen
  0,      //shiftX
  0,      //shiftY
  0,      //shiftY1
  0       //subpattern
};

// Cycle IMG brush (touch1); sync current channel + encoder LEDs.
static inline void cycleImgBrush() {
  extern int drawMode;
  imgBrushChannel = imageModePaintChannel(imgBrushChannel);
  GLOB.currentChannel = imgBrushChannel;
  if (drawMode == 0) {
    Encoder[0].writeRGBCode(CRGBToUint32(col[GLOB.currentChannel]));
  }
  Encoder[3].writeRGBCode(CRGBToUint32(col[GLOB.currentChannel]));
}

// Resolve paint channel in IMG: empty uses brush; occupied cycles and updates brush.
static inline int imageModeResolvePaintChannel(uint8_t existingCh) {
  int ch;
  if (existingCh == 0) {
    ch = imgBrushChannel;
    if (ch < 1 || ch > 8 || isChildVoiceDisabled(ch)) {
      ch = imageModePaintChannel(0);
    } else {
      setMuteState(ch, false);
    }
  } else {
    ch = imageModePaintChannel(existingCh);
  }
  imgBrushChannel = ch;
  return ch;
}

// When IMG is on: VMOD off, CLR=FIX, leave single mode.
FLASHMEM void enforceImageModeConstraints() {
  if (!imageMode) return;

  if (voiceMode) {
    voiceMode = false;
    EEPROM.write(EEPROM_DATA_START + 42, 0);
    updateLastPage();
  }

  if (recChannelClear != 2) {
    recChannelClear = 2;  // FIX — no note manipulation while recording
    EEPROM.write(EEPROM_DATA_START + 6, 2);
    SMP_REC_CHANNEL_CLEAR = false;
  }

  if (GLOB.singleMode || currentMode == &singleMode) {
    GLOB.singleMode = false;
    if (currentMode == &singleMode) {
      switchMode(&draw);
    }
  }
}

// LEDS=2/2B: pages are maxX=32 wide → only MAX_STEPS/maxX (=8) legal pages.
// Unclamped page indices (or initEncoders maxX*4) remap X past note[] and crash.
static inline int effectivePageCount() {
  int n = (maxX > 0) ? (int)(MAX_STEPS / maxX) : (int)maxPages;
  if (n < 1) n = 1;
  if (n > (int)maxPages) n = (int)maxPages;
  return n;
}

static inline int encoderPageMax() {
  if (childLockEnabled) return 1;
  int maxPg = effectivePageCount();
  // NEXT is a live page cue: like PMOD OFF, every page must remain reachable,
  // including empty pages beyond the last page that currently contains notes.
  if (patternMode == 3) return maxPg;
  if (SMP_PATTERN_MODE && (int)lastPage >= 1 && (int)lastPage < maxPg) return (int)lastPage;
  return maxPg;
}

static inline void clampGridCursor() {
  unsigned int xmax = childLockEnabled ? maxX : MAX_STEPS;
  if (xmax < 1) xmax = 1;
  if (GLOB.x < 1) GLOB.x = 1;
  else if (GLOB.x > xmax) GLOB.x = xmax;
  if (GLOB.y < 1) GLOB.y = 1;
  else if (GLOB.y > maxY) GLOB.y = maxY;
}

float myFreq = 80;
float freqValue = 1000;
float resValue = 0.1;
float octValue = 2.0;
int transpose = 0;
int scale = 0;
int menuIndex = 0;
float gainValue = 2.0;


#define NUM_PARAMS (sizeof(SMP.param_settings[0]) / sizeof(SMP.param_settings[0][0]))
static_assert(FILTER_WAVEFORM == maxFilters, "Review legacy waveform slot mapping");
float& filterSetting(int channel, int index) {
  return toern_audio::legacyFilterValue(SMP.filter_settings, SMP.synth_settings, channel, index);
}

#define NUM_FILTERS (sizeof(SMP.filter_settings[0]) / sizeof(SMP.filter_settings[0][0]))
#define MAX_CHANNELS maxY  // maxY is the number of channels (e.g. 16)

EXTMEM uint32_t loadedSampleRate[MAX_CHANNELS];
EXTMEM uint32_t loadedSampleLen[MAX_CHANNELS];
DMAMEM int8_t channelDirection[maxFiles];
DMAMEM static bool prevMuteState[maxY + 1];
static bool tmpMuteActive = false;
// Snapshot taken on fullMute enter; restored only on enc1 exit (never by enc2/3/4 views).
DMAMEM static bool fullMuteSavedGlobal[maxY];
DMAMEM static bool fullMuteSavedPages[maxPages][maxY];
static bool fullMuteActive = false;
static FullMuteView fullMuteView = FullMuteView::AllMuted;
// SETTINGS>MUTE uses user CH1..CH16; EEPROM bits are internal mute indices 0..15 (CH1→1..CH15→15, CH16→0). Default CH1+CH2 = bits 1|2 = 0x0006.
uint16_t drawRFullMuteCustomUnmuteMask = 0x0006;

bool fullMuteIsActive() {
  return fullMuteActive;
}

// Per-page mute system for PMOD (pattern mode)
DMAMEM static bool pageMutes[maxPages][maxY];  // [page][channel] - stores mute state per page
DMAMEM static bool globalMutes[maxY];          // stores global mute state when PMOD is off

bool isChildVoiceDisabled(int channel) {
  return childLockEnabled && channel >= 9 && channel <= 14;
}

FLASHMEM bool isChildVoiceMuted(int channel) {
  return childLockEnabled && (channel == 11 || channel == 13 || channel == 14);
}

FLASHMEM void enforceChildModeRestrictions() {
  if (!childLockEnabled) return;

  int localX = ((int)GLOB.x - 1) % (int)maxX;
  if (localX < 0) localX = 0;
  pendingPage = 0;
  editpage = 1;
  GLOB.edit = 1;
  GLOB.page = 1;
  if (beat < 1 || beat > maxX) beat = 1;

  GLOB.x = (unsigned int)localX + 1;
  fullMuteActive = false;
  fullMuteView = FullMuteView::AllMuted;
  tmpMute = false;
  tmpMuteActive = false;
  muteModeActive = false;
  muteModeReturn = nullptr;
  muteModeLastChannel = -1;
  muteModeReturnSingleState = false;
  muteModeArrowDirection = 0;
  muteModeArrowUntil = 0;
  muteModeEncoderValue = 0;

  if (isChildVoiceDisabled((int)GLOB.currentChannel)) {
    GLOB.currentChannel = 1;
    if (currentMode == &singleMode) {
      GLOB.y = 2;
      currentMode->pos[0] = 2;
      Encoder[0].writeCounter((int32_t)2);
    }
  }

  for (int ch = 0; ch < maxY; ch++) {
    bool childMuted = isChildVoiceMuted(ch);
    globalMutes[ch] = childMuted;
    SMP.globalMutes[ch] = childMuted;
    SMP.mute[ch] = childMuted ? 1u : 0u;
    for (int page = 0; page < maxPages; page++) {
      pageMutes[page][ch] = childMuted;
      SMP.pageMutes[page][ch] = childMuted;
    }
  }

  for (int noteValue = 0; noteValue <= 107; noteValue++) {
    stopSound(noteValue, 0);
    stopSound(noteValue, 1);
  }
  stopSynthChannel(13);
  stopSynthChannel(14);
  resetMidiPressedKeyCount11to14();

  if (currentMode == &draw || currentMode == &singleMode) {
    currentMode->pos[1] = 1;
    currentMode->pos[3] = GLOB.x;
    Encoder[1].writeMin((int32_t)1);
    Encoder[1].writeMax((int32_t)1);
    Encoder[1].writeCounter((int32_t)1);
    Encoder[3].writeMax((int32_t)maxX);
    Encoder[3].writeCounter((int32_t)GLOB.x);
  }
}

//EXTMEM int16_t fastRecBuffer[MAX_CHANNELS][BUFFER_SAMPLES];
EXTMEM static size_t fastRecWriteIndex[MAX_CHANNELS];
bool fastRecordActive = false;
uint8_t fastRecordChannel = 0;  // channel whose sample buffer is being overwritten
bool recordingBorderArmed = false;  // red border shown before/during armed capture
bool countInActive = false;              // Count-in active for ON1 mode
int countInBeat = 0;                     // Current count-in beat (0-4, where 0=waiting, 1-4=count, 5=start recording)
bool countInComplete = false;            // Flag to track when count-in (1,2,3,4) is complete
bool countInPending = false;             // Flag to track when waiting for next beat 1 to start count-in
unsigned long touch3PressStartTime = 0;  // When touch3 was first pressed
bool touch3PressProcessed = false;       // Whether the >300ms press has been processed
unsigned int recordingStartBeat = 0;     // Beat where recording started (to stop before reaching it again)
unsigned int recordingBeatCount = 0;     // Absolute beat counter for recording (doesn't wrap)
bool pendingStopFastRecord = false;      // Flag to defer stopFastRecord() from interrupt to main loop
bool pendingStartFastRecord = false;     // Start from main loop after the red border is shown
bool fastRecWaitRelease = false;         // After auto-stop, don't re-arm until the trigger is released


// State variables
uint8_t filterPage[NUM_CHANNELS] = { 0 };
uint8_t lastEncoder = 0;                                                                                       // last used encoder index (0-3)
static int16_t lastEncVal[NUM_CHANNELS] = { -1, -1, -1, -1, -1, -1, -1, -1, -1, -1, -1, -1, -1, -1, -1, -1 };  // Track last encoder value per channel

// Color scheme selection (0=default, 1=blue-ish, 2=whitish)
uint8_t currentColorScheme = 0;
volatile bool colorsUpdatedViaSerial = false;



// Number of parameter slots (ATTACK..RELEASE indexes 0-5)
constexpr int PARAM_COUNT = 6;


FLASHMEM const float maxParamVal[12] = { 1000.0, 2000.0, 1000.0, 1000.0, 1.0, 1000.0 };



FilterType defaultFilter[maxFiles] = { HCUT };

const char *const activeMidiSetType[6] PROGMEM = { "IN", "OUT", "OUT", "INPT", "SCTL", "RCTL" };

// Arrays to track multiple encoders
uint8_t buttons[NUM_ENCODERS] = { 0 };  // Changed from int to uint8_t (12 bytes saved)
EXTMEM unsigned long buttonPressStartTime[NUM_ENCODERS] = { 0 };
EXTMEM unsigned long pressDuration[NUM_ENCODERS] = { 0 };
const unsigned long longPressDuration[NUM_ENCODERS] = { 200, 200, 200, 200 };  // 300ms for long press (const = flash)

ButtonState buttonState[NUM_ENCODERS] = { IDLE };
bool isPressed[NUM_ENCODERS] = { false };
bool pressed[NUM_ENCODERS] = { false };


i2cEncoderLibV2 Encoder[NUM_ENCODERS] = {
  // exttouch: panel was soldered 4,3,2,1 — reverse I2C address order.
  i2cEncoderLibV2(exttouch ? 0x61 : 0x01),
  i2cEncoderLibV2(exttouch ? 0x20 : 0x41),
  i2cEncoderLibV2(exttouch ? 0x41 : 0x20),
  i2cEncoderLibV2(exttouch ? 0x01 : 0x61),
};
// Global variable to track current encoder index for callbacks
int currentEncoderIndex = 0;

// Adafruit NeoSliders @ I2C 0x30..0x33 → always control voices 1..4 volume.
// Address: default 0x30; A0→0x31, A1→0x32, A0+A1→0x33. LEDs use that voice's col[].
// Uses Adafruit_seesaw (no Wire.h / Wire.* in this sketch). LED colors via FastLED CRGB.
#define NEOSLIDER_COUNT 4
#define NEOSLIDER_NUM_LEDS 4
// Lit LEDs use full channel color; no global dim (was making the bar muddy).
#define NEOSLIDER_LED_BRIGHTNESS 255

static const uint8_t neoSliderAddrs[NEOSLIDER_COUNT] = { 0x30, 0x31, 0x32, 0x33 };
static const uint8_t neoSliderVoiceCh[NEOSLIDER_COUNT] = { 1, 2, 3, 4 };

// Channels that have a real volume/amp path (CTRL=VOL); NeoSliders always drive voices 1-4 on every Y.
static inline bool isVolumeVoiceChannel(int ch) {
  return (ch >= 1 && ch <= 8) || ch == 11 || ch == 13 || ch == 14;
}
#define SS_NEOPIXEL_BASE 0x0E
#define SS_NEOPIXEL_PIN 0x01
#define SS_NEOPIXEL_SPEED 0x02
#define SS_NEOPIXEL_BUF_LENGTH 0x03
#define SS_NEOPIXEL_BUF 0x04
#define SS_NEOPIXEL_SHOW 0x05
// ATtiny (seesaw) pin ids in the I2C register map — NOT Teensy pins
#define SS_NEOSLIDER_ADC_CH 18
#define SS_NEOSLIDER_LED_PIN 14

// Expose seesaw register helpers. Avoid Adafruit_seesaw::analogRead() — it ends
// with delay(1) every call and stalls the main loop (cursor pulse, encoders).
class NeoSliderSeesaw : public Adafruit_seesaw {
public:
  bool writeReg(uint8_t regHigh, uint8_t regLow, uint8_t *buf, uint8_t num) {
    return write(regHigh, regLow, buf, num);
  }
  bool writeReg8(uint8_t regHigh, uint8_t regLow, uint8_t value) {
    return write8(regHigh, regLow, value);
  }
  // Same ADC path as analogRead(), without the blocking delay(1).
  // 10-bit seesaw ADC is 0..1023. Failed I2C / not-ready is often 0xFFFF.
  bool analogReadFast(uint8_t pin, uint16_t &value) {
    uint8_t buf[2];
    if (!read(SEESAW_ADC_BASE, (uint8_t)(SEESAW_ADC_CHANNEL_OFFSET + pin), buf, 2, 15)) {
      return false;
    }
    uint16_t v = ((uint16_t)buf[0] << 8) | buf[1];
    if (v > 1023) return false;
    value = v;
    return true;
  }
};

static NeoSliderSeesaw neoSliderSS[NEOSLIDER_COUNT];
static bool neoSliderPresent[NEOSLIDER_COUNT];
static bool neoSliderAnyPresent = false;
static int neoSliderLastVol[NEOSLIDER_COUNT];
static bool neoSliderMuteLatched[NEOSLIDER_COUNT];
static bool neoSliderInMuteDz[NEOSLIDER_COUNT];
static bool neoSliderInFullDz[NEOSLIDER_COUNT];
static float neoSliderVelScale[NEOSLIDER_COUNT];      // 0..1 live velocity scaler (not AMP)
static float neoSliderLastVelNorm[NEOSLIDER_COUNT];  // last note vel 0..1, so fader can re-scale the current hit
static CRGB neoSliderLeds[NEOSLIDER_COUNT][NEOSLIDER_NUM_LEDS];
static elapsedMillis neoSliderActiveUntil[NEOSLIDER_COUNT];  // faster ADC while fader is moving
static int neoSliderLedVolShown[NEOSLIDER_COUNT];           // last volume pushed to NeoPixels
static int neoSliderLedVolWanted[NEOSLIDER_COUNT];          // desired bar; SHOW is retried separately
static elapsedMillis g_faderMovedAgo = 1000;

bool encoderI2cWritesAllowed() {
  if (!deviceHasFaders || !neoSliderAnyPresent) return true;
  // SET_WAV skips fader I2C; allow one-shot encoder range/RGB writes (not every frame).
  if (currentMode == &set_Wav || currentMode == &menu) return true;
  return g_faderMovedAgo >= 80;
}

static void applyLongCableI2cTiming();

static inline bool isNeoSliderControlledChannel(int ch) {
  return deviceHasFaders && ch >= 1 && ch <= NEOSLIDER_COUNT && neoSliderPresent[ch - 1];
}

// 10-bit travel: bottom/top 5% are mute / full stops (plus ~24-count hysteresis).
static const uint16_t FADER_ADC_MAX = 1023;
static const uint16_t FADER_MUTE_RAW = 51;    // 5%
static const uint16_t FADER_FULL_RAW = 972;   // 95%
static const uint16_t FADER_RAW_HYST = 24;

static float faderVelScaleFromSlide(uint16_t slideVal, bool inMute, bool inFull) {
  if (inMute) return 0.0f;
  if (inFull) return 1.0f;
  const float lo = (float)(FADER_MUTE_RAW + 1);
  const float hi = (float)(FADER_FULL_RAW - 1);
  float t = ((float)slideVal - lo) / (hi - lo);
  if (t < 0.0f) t = 0.0f;
  if (t > 1.0f) t = 1.0f;
  return t;
}

static int faderVolFromSlide(uint16_t slideVal, bool inMute, bool inFull) {
  if (inMute) return 0;
  if (inFull) return 16;
  const int lo = (int)FADER_MUTE_RAW + 1;
  const int hi = (int)FADER_FULL_RAW - 1;
  int span = hi - lo;
  if (span < 1) span = 1;
  int pos = (int)slideVal - lo;
  if (pos < 0) pos = 0;
  if (pos > span) pos = span;
  int vol = 1 + (pos * 15) / span;
  if (vol < 1) vol = 1;
  if (vol > 15) vol = 15;
  return vol;
}

static void applyVoiceAmpGainFromVol(int ch, int vol);

// Slider column positions (2 LEDs each)
static const uint8_t sliderCols[4][2] = { { 2, 3 }, { 6, 7 }, { 10, 11 }, { 14, 15 } };

// For each page and slot: {arrayType, settingIndex, name}
DMAMEM static SliderDefEntry sliderDef[NUM_CHANNELS][4][4];

FLASHMEM void initSliderDefTemplates() {
  static const SliderDefEntry sliderDefTemplate[4][4] = {
    { { ARR_FILTER, HCUT, "HCUT", 32, DISPLAY_NUMERIC, nullptr, 32 },
      { ARR_FILTER, LOWCUT, "LCUT", 32, DISPLAY_NUMERIC, nullptr, 32 },
      { ARR_FILTER, REVERB, "RVRB", 32, DISPLAY_NUMERIC, nullptr, 32 },
      { ARR_FILTER, BITCRUSHER, "BITC", 32, DISPLAY_NUMERIC, nullptr, 32 } },
    { { ARR_SYNTH, CUTOFF, "CUT", 32, DISPLAY_NUMERIC, nullptr, 32 },
      { ARR_SYNTH, RESONANCE, "RES", 32, DISPLAY_NUMERIC, nullptr, 32 },
      { ARR_SYNTH, FILTER, "FLT", 32, DISPLAY_NUMERIC, nullptr, 32 },
      { ARR_NONE, -1, "", 0, DISPLAY_NUMERIC, nullptr, 0 } },
    { { ARR_FILTER, FILTER_WAVEFORM, "WAVE", 16, DISPLAY_ENUM, waveformNames, 4 },
      { ARR_SYNTH, INSTRUMENT, "INST", 9, DISPLAY_ENUM, instTypeNames, 10 },
      { ARR_SYNTH, CENT, "CENT", 32, DISPLAY_NUMERIC, nullptr, 32 },
      { ARR_SYNTH, SEMI, "SEMI", 32, DISPLAY_NUMERIC, nullptr, 32 } },
    { { ARR_PARAM, ATTACK, "ATTC", 32, DISPLAY_NUMERIC, nullptr, 32 },
      { ARR_PARAM, DECAY, "DCAY", 32, DISPLAY_NUMERIC, nullptr, 32 },
      { ARR_PARAM, SUSTAIN, "SUST", 32, DISPLAY_NUMERIC, nullptr, 32 },
      { ARR_PARAM, RELEASE, "RLSE", 32, DISPLAY_NUMERIC, nullptr, 32 } }
  };
  for (int ch = 0; ch < NUM_CHANNELS; ++ch) {
    for (int p = 0; p < 4; ++p) {
      for (int s = 0; s < 4; ++s) {
        sliderDef[ch][p][s] = sliderDefTemplate[p][s];
      }
    }
  }
  // For channel 1 (index 1), set the fourth page to ARR_NONE for all slots
  for (int s = 0; s < 4; ++s) {
    sliderDef[1][3][s].arr = ARR_NONE;
    sliderDef[1][3][s].idx = 0;
  }
}

struct FilterTarget {
  SettingArray arr;
  uint8_t idx;
};
DMAMEM FilterTarget defaultFastFilter[NUM_CHANNELS];  // one per channel

EXTMEM arraysampler _samplers[9];
AudioPlayArrayResmp *voices[9] = { &sound0, &sound1, &sound2, &sound3, &sound4, &sound5, &sound6, &sound7, &sound8 };
static uint8_t sampleTimeStretch[9] = {11,11,11,11,11,11,11,11,11};
void setSampleTimeStretch(uint8_t channel, int value) {
  if (channel < 1 || channel > 8) return;
  sampleTimeStretch[channel] = constrain(value, 0, 22);
  voices[channel]->setTimeStretchAmount(sampleTimeStretch[channel]);
}


AudioEffectEnvelope *envelopes[15] = { &envelope0, &envelope1, &envelope2, &envelope3, &envelope4, &envelope5, &envelope6, &envelope7, &envelope8, nullptr, nullptr, &envelope11, nullptr, &envelope13, &envelope14 };
AudioAmplifier *amps[15] = { nullptr, &amp1, &amp2, &amp3, &amp4, &amp5, &amp6, &amp7, &amp8, nullptr, nullptr, &amp11, nullptr, &amp13, &amp14 };
AudioFilterStateVariable *filters[15] = { nullptr, &filter1, &filter2, &filter3, &filter4, &filter5, &filter6, &filter7, &filter8, nullptr, nullptr, &filter11, nullptr, &filter13, &filter14 };
AudioMixer4 *filtermixers[15] = { nullptr, &filtermixer1, &filtermixer2, &filtermixer3, &filtermixer4, &filtermixer5, &filtermixer6, &filtermixer7, &filtermixer8, nullptr, nullptr, &filtermixer11, nullptr, &filtermixer13, &filtermixer14 };
AudioEffectBitcrusher *bitcrushers[15] = { nullptr, &bitcrusher1, &bitcrusher2, &bitcrusher3, &bitcrusher4, &bitcrusher5, &bitcrusher6, &bitcrusher7, &bitcrusher8, nullptr, nullptr, &bitcrusher11, nullptr, &bitcrusher13, &bitcrusher14 };
AudioEffectFreeverbDMAMEM *freeverbs[15] = { nullptr, &freeverb1, &freeverb2, nullptr, nullptr, &freeverb5, &freeverb6, &freeverb7, &freeverb8, 0, 0, &freeverb11, nullptr, nullptr, nullptr };
AudioMixer4 *freeverbmixers[15] = { nullptr, &freeverbmixer1, &freeverbmixer2, nullptr, nullptr, &freeverbmixer5, &freeverbmixer6, &freeverbmixer7, &freeverbmixer8, nullptr, nullptr, nullptr, nullptr, nullptr, nullptr };
AudioMixer4 *waveformmixers[15] = { nullptr, nullptr, nullptr, nullptr, nullptr, nullptr, nullptr, nullptr, nullptr, nullptr, nullptr, &mixer_waveform11, nullptr, &mixer_waveform13, &mixer_waveform14 };

// VOL>SPLT: 0 = normal (main+preview to both L/R), 1 = split (main->L only, preview->R only)
// VOL>2-CH: Stereo routing modes
// 0 = OFF (normal routing: main and preview to both L+R)
// 1 = M+P (main -> L, preview -> R)
// 2 = L+R (channels 1-4 -> L, 5-8 -> R, preview muted)
int8_t stereoChannel = 0;

FLASHMEM void applyStereoChannelRouting() {
  // stereo mixer inputs:
  // - input 0: mixer_end (main)
  // - input 1: mixer0 (preview)
  // inputs 2/3 unused

  if (stereoChannel == 0) {
    // OFF: Normal routing - main and preview to both L+R
    mixer_stereoL.gain(0, 1.0f);  // main -> L
    mixer_stereoL.gain(1, 1.0f);  // preview -> L
    mixer_stereoL.gain(2, 0.0f);  // mixer1 muted
    mixer_stereoR.gain(0, 1.0f);  // main -> R
    mixer_stereoR.gain(1, 1.0f);  // preview -> R
    mixer_stereoR.gain(2, 0.0f);  // mixer2 muted
  } else if (stereoChannel == 1) {
    // M+P: Main -> L, Preview -> R
    mixer_stereoL.gain(0, 1.0f);  // main -> L
    mixer_stereoL.gain(1, 0.0f);  // preview off on L
    mixer_stereoL.gain(2, 0.0f);  // mixer1 muted
    mixer_stereoR.gain(0, 0.0f);  // main off on R
    mixer_stereoR.gain(1, 1.0f);  // preview -> R
    mixer_stereoR.gain(2, 0.0f);  // mixer2 muted
  } else {                        // stereoChannel == 2
    // L+R: Channels 1-4 -> L, 5-8 -> R, preview muted
    // Use direct connections: mixer1 (ch1-4) -> L, mixer2 (ch5-8) -> R
    mixer_stereoL.gain(0, 0.0f);  // mixer_end muted on L
    mixer_stereoL.gain(1, 0.0f);  // preview muted
    mixer_stereoL.gain(2, 1.0f);  // mixer1 (ch1-4) -> L
    mixer_stereoR.gain(0, 0.0f);  // mixer_end muted on R
    mixer_stereoR.gain(1, 0.0f);  // preview muted
    mixer_stereoR.gain(2, 1.0f);  // mixer2 (ch5-8) -> R
  }
  // Ensure unused inputs are muted
  mixer_stereoR.gain(3, 0.0f);
  mixer_stereoL.gain(3, 0.0f);
}

static inline uint8_t clampMixGain(uint8_t g) {
  return (g > MIX_GAIN_MAX) ? (uint8_t)MIX_GAIN_UNITY : g;
}

static inline float mixGainScale(uint8_t g) {
  return (float)clampMixGain(g) * (1.0f / (float)MIX_GAIN_UNITY);
}

// Apply VOL→GAIN onto mixer1 / mixer2 / mixer_end synth. Does not touch mixer_end in3 (monitor)
// or preview. L+R 2-CH taps mixer1/2 directly, so bus+master still apply there.
FLASHMEM void applyMixBusGains() {
  const float master = mixGainScale(mixGainMaster);
  const float g14 = MIX_BUS_HEADROOM * mixGainScale(mixGain14) * master;
  const float g58 = MIX_BUS_HEADROOM * mixGainScale(mixGain58) * master;
  mixer1.gain(0, g14);
  mixer1.gain(1, g14);
  mixer1.gain(2, g14);
  mixer1.gain(3, g14);
  mixer2.gain(0, g58);
  mixer2.gain(1, g58);
  mixer2.gain(2, g58);
  mixer2.gain(3, g58);
  mixer_end.gain(0, MIX_END_SAMPLES_GAIN);
  mixer_end.gain(1, MIX_END_SAMPLES_GAIN);
  mixer_end.gain(2, MIX_END_SYNTH_GAIN * mixGainScale(mixGainSynth) * master);
}

// Stop synth channels (13/14) immediately (also used from MIDI note-off).
void stopSynthChannel(int ch) {
  if (ch < 13 || ch > 14) return;
  if (envelopes[ch]) envelopes[ch]->noteOff();
  noteOnTriggered[ch] = false;
  persistentNoteOn[ch] = false;
  sequencedMonoSynthActive[ch] = false;
}

// When playback is stopped or voices are silenced globally, clear MIDI poly counters so they
// cannot desync from the hardware envelope (phantom Note On counts).
static inline void resetMidiPressedKeyCount11to14() {
  for (int c = 11; c <= 14; ++c) {
    pressedKeyCount[c] = 0;
  }
}

// Arp step per channel (used for synth channels)
static uint32_t arpStepCounter[15] = { 0 };
// Map external 14-bit input (e.g. pitchbend) to current channel fast filter
static inline void applyExternalFastFilter(uint16_t value14) {
  FilterTarget dft = defaultFastFilter[GLOB.currentChannel];
  if (dft.arr == ARR_NONE) return;
  int mapped = constrain((int)mapf(value14, 0.0f, 16383.0f, 0.0f, maxfilterResolution), 0, (int)maxfilterResolution);

  // Guard PARAM index
  if (dft.arr == ARR_PARAM && dft.idx >= PARAM_COUNT) return;

  setDefaultFastFilterValue(GLOB.currentChannel, dft.arr, dft.idx, mapped);

  switch (dft.arr) {
    case ARR_FILTER:
      setFilters(dft.idx, GLOB.currentChannel, false);
      break;
    case ARR_SYNTH:
      if (GLOB.currentChannel == 11) updateSynthVoice(11);
      break;
    case ARR_PARAM:
      setParams(dft.idx, GLOB.currentChannel);
      break;
    default:
      break;
  }
}

AudioSynthWaveform *synths[15][2];


//for FULL patch:

AudioSynthWaveformDc *Sdc1[3] = { &Sdc1_0, &Sdc1_1, &Sdc1_2 };
AudioEffectEnvelope *Senvelope1[3] = { &Senvelope1_0, &Senvelope1_1, &Senvelope1_2 };
AudioEffectEnvelope *Senvelope2[3] = { &Senvelope2_0, &Senvelope2_1, &Senvelope2_2 };
AudioEffectEnvelope *SenvelopeFilter1[3] = { &SenvelopeFilter1_0, &SenvelopeFilter1_1, &SenvelopeFilter1_2 };

AudioSynthWaveform *Swaveform1[3] = { &Swaveform1_0, &Swaveform1_1, &Swaveform1_2 };
AudioSynthWaveform *Swaveform2[3] = { &Swaveform2_0, &Swaveform2_1, &Swaveform2_2 };
AudioSynthWaveform *Swaveform3[3] = { &Swaveform3_0, &Swaveform3_1, &Swaveform3_2 };

AudioFilterLadder *Sladder1[3] = { &Sladder1_0, &Sladder1_1, &Sladder1_2 };
AudioFilterLadder *Sladder2[3] = { &Sladder2_0, &Sladder2_1, &Sladder2_2 };

AudioMixer4 *Smixer1[3] = { &Smixer1_0, &Smixer1_1, &Smixer1_2 };
AudioMixer4 *Smixer2[3] = { &Smixer2_0, &Smixer2_1, &Smixer2_2 };
/**/

void allOff() {
  for (AudioEffectEnvelope *envelope : envelopes) {
    if (!envelope) continue;
    envelope->noteOff();
  }
}



static uint8_t noteConditionFromStep(int step) {
  if (step < 1 || step > NOTE_CONDITION_STEP_COUNT) return 1;
  return pgm_read_byte(&noteConditionValues[step - 1]);
}

static int noteConditionToStep(uint8_t condition) {
  if (condition == 0) condition = 1;
  for (int step = 1; step <= NOTE_CONDITION_STEP_COUNT; step++) {
    if (pgm_read_byte(&noteConditionValues[step - 1]) == condition) return step;
  }
  return 1;
}

FLASHMEM void setVelocity() {
  if (childLockEnabled) {
    switchMode(GLOB.singleMode ? &singleMode : &draw);
    return;
  }

  // Update velocity (encoder[0])
  if (currentMode->pos[0] != GLOB.velocity) {
    GLOB.velocity = currentMode->pos[0];

    if (GLOB.singleMode) {
      note[GLOB.x][GLOB.y].velocity = round(mapf(GLOB.velocity, 1, maxY, 1, 127));
    } else {

      for (unsigned int nx = 1; nx < maxlen; nx++) {
        for (unsigned int ny = 1; ny < maxY + 1; ny++) {
          if (note[nx][ny].channel == note[GLOB.x][GLOB.y].channel)
            note[nx][ny].velocity = round(mapf(GLOB.velocity, 1, maxY, 1, 127));
        }
      }
    }
  }

  // Update probability (encoder[1])
  static int lastProbStep = -1;
  int currentProbStep = currentMode->pos[1];

  if (currentProbStep != lastProbStep) {
    lastProbStep = currentProbStep;

    // Map encoder steps 1-5 to probability values 0%, 25%, 50%, 75%, 100%
    uint8_t probValue;
    switch (currentProbStep) {
      case 1: probValue = 0; break;
      case 2: probValue = 25; break;
      case 3: probValue = 50; break;
      case 4: probValue = 75; break;
      case 5: probValue = 100; break;
      default: probValue = 100; break;
    }
    note[GLOB.x][GLOB.y].probability = probValue;
  }

  // Update condition (encoder[2] / 3rd) — was wrongly on encoder[3]
  static int lastCondStep = -1;
  int currentCondStep = currentMode->pos[2];

  if (currentCondStep != lastCondStep) {
    lastCondStep = currentCondStep;

    // Map encoder steps 1-11 to condition values
    // Positions 1-5: 1/X conditions -> values 1, 2, 4, 8, 16
    // Positions 6-9: X/1 conditions -> values 17, 18, 19, 20
    // Position 10: F/F fill; position 11: G/L glide/legato.
    note[GLOB.x][GLOB.y].condition = noteConditionFromStep(currentCondStep);
  }

  // Channel volume (encoder[3] / 4th)
  {
    int ch = GLOB.currentChannel;
    unsigned int newVol = currentMode->pos[3];
    if (ch >= 0 && ch < 15 && amps[ch] != nullptr && SMP.channelVol[ch] != newVol) {
      SMP.channelVol[ch] = newVol;
      applyVoiceAmpGainFromVol(ch, (int)newVol);
    }
  }

  drawVelocity();
}




void staticButtonPushed(i2cEncoderLibV2 *obj) {
  pressed[currentEncoderIndex] = true;
  encoder_button_pushed(obj, currentEncoderIndex);
}




void staticButtonReleased(i2cEncoderLibV2 *obj) {
  encoder_button_released(obj, currentEncoderIndex);
  pressed[currentEncoderIndex] = false;
}

void staticThresholds(i2cEncoderLibV2 *obj) {
  //  encoder_thresholds(obj, currentEncoderIndex);
}
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
void loop() {
  checkSerialColors();

  // Menu → ETC → SD: enable serial file server while that page is open
  {
    extern bool inEtcSubmenu;
    extern int getCurrentMenuMainSetting();
    extern void sdSerialServerSetActive(bool on);
    extern void sdSerialServerPoll();
    extern void sdSerialServerPollNeedSdHint();
    extern bool sdSerialServerIsActive();
    const bool wantSd = inEtcSubmenu && (getCurrentMenuMainSetting() == 49);
    if (wantSd != sdSerialServerIsActive()) {
      sdSerialServerSetActive(wantSd);
      extern void menuRequestFullRedraw();
      menuRequestFullRedraw();
    }
    if (wantSd) sdSerialServerPoll();
    else sdSerialServerPollNeedSdHint();
  }

  updateExternalOneBlink();
  checkMidi();  // Process MIDI early in loop for lower latency
  // Debounced SD backup of EEPROM settings (settings.txt)
  extern void serviceSettingsBackup();
  serviceSettingsBackup();

  yield();  // Yield early to maintain responsiveness during file operations

#if BATT_DEBUG_SERIAL
  {
    static elapsedMillis battDebugTimer;
    if (battDebugTimer >= 2000) {
      battDebugTimer = 0;
      int raw = analogRead(BATT_ADC_PIN);
      int corrected = raw - BATT_RAW_ZERO;
      if (corrected < 0) corrected = 0;
      float vMeasured = (float)corrected * (3.3f / (float)(BATT_RAW_FULL - BATT_RAW_ZERO));
      float vBat = vMeasured / BATT_DIVIDER_RATIO;
      float norm = (vBat - BATT_V_MIN) / (BATT_V_MAX - BATT_V_MIN);
      if (norm < 0.0f) norm = 0.0f;
      if (norm > 1.0f) norm = 1.0f;
      float pct = powf(norm, BATT_PCT_CURVE) * 100.0f;
      if (pct < 0.0f) pct = 0.0f;
      if (pct > 100.0f) pct = 100.0f;
      Serial.print("BATT raw=");
      Serial.print(raw);
      Serial.print(" Vmeas=");
      Serial.print(vMeasured, 3);
      Serial.print(" VBAT=");
      Serial.print(vBat, 3);
      Serial.print(" %=");
      Serial.println((int)(pct + 0.5f));
    }
  }
#endif

  // === Deferred work from timer interrupt (playNote) ===
  // Keep all Serial/LED/I2C/encoder work out of ISRs.
  if (isrPlayButtonTick) {
    // Single-byte flag; on ARM this is atomic. Avoid masking interrupts to keep MIDI clock tight.
    isrPlayButtonTick = false;
    drawPlayButton();
  }

  // Deferred pause UI (I2C) on one loop tick; autosave on a *later* tick so SD
  // I/O doesn't pile onto the same frame (avoids audio glitches while voices decay).
  // Always schedule autosave after a normal pause — only skipSave (MIDI/SD) opts out.
  // The only other skip is autoSave()'s 5s cooldown.
  if (pendingPauseUIUpdate) {
    pendingPauseUIUpdate = false;
    updateLastPage();
    if (currentMode == &draw || currentMode == &singleMode) {
      if (childLockEnabled) {
        enforceChildModeRestrictions();
      } else if (ctrlMode == 0 && SMP_PATTERN_MODE) {
        Encoder[1].writeMax((int32_t)encoderPageMax());
      } else if (ctrlMode == 1) {
        refreshCtrlEncoderConfig();
      }
    }
    Encoder[2].writeRGBCode(0x00FF00);
    if (!pendingPauseSkipSave) {
      pendingPauseAutoSave = true;  // next loop iteration
    }
    pendingPauseSkipSave = false;
  } else if (pendingPauseAutoSave) {
    pendingPauseAutoSave = false;
    autoSave();
  }

  if (isrDbgPatternFinished) {
    isrDbgPatternFinished = false;
  }

  if (isrDbgLoopCountChanged) {
    isrDbgLoopCountChanged = false;
  }

  // Handle deferred stop recording (from timer interrupt)
  if (pendingStopFastRecord) {
    pendingStopFastRecord = false;
    stopFastRecord();
  }

  // Present red border, then start capture — never from the playNote ISR.
  if (pendingStartFastRecord && !fastRecordActive) {
    pendingStartFastRecord = false;
    recordingBorderArmed = true;
    extern void presentRecordingBorder();
    presentRecordingBorder();
    startFastRecord();
  }

  // Drain ADC queue as early/often as possible while capturing.
  if (fastRecordActive) {
    flushAudioQueueToRAM();

    // FastTouchRead() takes noInterrupts() and was called on every pad every tick
    // via checkTouchInputs() — that drops AudioRecordQueue blocks (clicks/gaps).
    // a0dbff6 already skipped FastLED/I2C here; do not re-introduce pad scans.
    static elapsedMillis recTriggerPoll;
    if (recTriggerPoll >= 8) {
      recTriggerPoll = 0;
      checkFastRec();
    }
    flushAudioQueueToRAM();
    yield();
    return;
  }

  // FLOW mode: SAME playback behavior as normal play.
  // ONLY difference: the visible page follows the beat being played (beatForUI).
  // Do page-follow work in the main loop to avoid mid-frame flicker.
  // Do NOT touch encoder 1 when CTRL-VOL is active (ctrlMode==1).
  extern bool songModeActive;
  if (!fastRecordActive && !childLockEnabled && SMP_FLOW_MODE && !(voiceMode && !songModeActive) && patternMode != 3 &&
      isNowPlaying &&
      (currentMode == &draw || currentMode == &singleMode)) {
    static uint16_t lastAppliedFlowPage = 0;
    // 32-bit read on ARM is atomic; avoid masking interrupts to keep MIDI clock tight.
    uint16_t bf = beatForUI;
    uint16_t timerPage = (bf > 0) ? (uint16_t)((bf - 1) / maxX + 1) : 1;
    if (timerPage != lastAppliedFlowPage) {
      // Keep the user-visible page (GLOB.edit) in sync with the beat being played.
      // IMPORTANT: don't override GLOB.page here; it's owned by playback/checkPages() and is used by loopCount logic.
      GLOB.edit = timerPage;
      editpage = timerPage;

      // Keep the cursor on the currently shown page as well.
      // Cursor X is stored as a global step (GLOB.x). Preserve the column offset within the page.
      int localX = mapXtoPageOffset((int)GLOB.x);
      localX = constrain(localX, 1, (int)maxX);
      unsigned int newGlobalX = ((timerPage - 1) * maxX) + (unsigned int)localX;
      if (newGlobalX < 1) newGlobalX = 1;
      if (newGlobalX > (maxlen - 1)) newGlobalX = (maxlen - 1);
      GLOB.x = newGlobalX;
      currentMode->pos[3] = (int)newGlobalX;
      Encoder[3].writeCounter((int32_t)newGlobalX);

      // Only sync encoder 1 when it's actually the page selector
      if (ctrlMode == 0) {
        currentMode->pos[1] = timerPage;
        Encoder[1].writeCounter((int32_t)timerPage);
      }
      lastFlowPage = timerPage;
      lastAppliedFlowPage = timerPage;
    }
  }

  bool pongActive = pong && currentMode == &draw;

  if (pongActive) {
    updatePongBall();
  } else {
    resetPongGame();
  }

  // UI render throttling (TargetFPS/RefreshTime). Input handling stays full speed below.
  // NOTE: FastLEDshow() has its own limiter; keep redraw and show timestamps separate.
  if (currentMode == &draw || currentMode == &singleMode) {
    unsigned long now = millis();
    // When sending master MIDI clock, keep UI updates lighter while PAUSED to reduce any chance
    // of interrupt masking inside display drivers affecting clock tightness.
    unsigned long effectiveRefresh = (unsigned long)RefreshTime;
    if (MIDI_CLOCK_SEND && !isNowPlaying) {
      if (effectiveRefresh < 100UL) effectiveRefresh = 100UL;  // cap at 10 FPS while paused + clocking
    }
    if ((unsigned long)(now - lastDrawUpdate) >= effectiveRefresh) {
      lastDrawUpdate = now;
      drawBase();
      drawTriggers();
      if (isNowPlaying) drawTimer();

      // Draw count-in for ON1 mode
      extern void drawCountIn();
      if (countInActive) {
        drawCountIn();
      }

      // Red border while armed / count-in (before capture). During capture the
      // framebuffer is frozen so this overlay is not redrawn.
      if (recordingBorderArmed || countInActive || countInPending) {
        extern void drawRecordingBorder();
        drawRecordingBorder();
      }

      // DRAW-R fullMute overlay: dark-blue border + W/Y/G/N indicators
      if (fullMuteIsActive()) {
        drawFullMuteBorder();
        drawFullMuteIndicators();
      }

      // Battery warning overlay (red border + empty battery icon)
      extern void drawBatteryWarning();
      extern bool getBatteryWarningActive();
      if (getBatteryWarningActive()) {
        drawBatteryWarning();
      }

      if (pongActive) {
        drawPongBall();
      }

      // Draw fast-filter overlay LAST so timer/base redraws can't overwrite it mid-window.
      if (filterDrawActive) {
        if (millis() <= filterDrawEndTime) {
          drawFilterCheck(filterDrawValue, (FilterType)0, filterDrawColor);
        } else {
          filterDrawActive = false;
        }
      }

      // CTRL / NeoSlider volume overlays (NeoSlider may show even when CTRL!==VOL).
      if (ctrlVolumeOverlayActive && (currentMode == &draw || currentMode == &singleMode)) {
        if (millis() <= ctrlVolumeOverlayUntil) {
          drawCtrlVolumeOverlay(ctrlVolumeOverlayValue);
        } else {
          ctrlVolumeOverlayActive = false;
        }
      }

      // Draw input gain overlay when in draw mode at y==1
      if (inputGainOverlayActive && currentMode == &draw && GLOB.y == 1 && ctrlMode == 1) {
        if (millis() <= inputGainOverlayUntil) {
          drawInputGainOverlay(inputGainOverlayValue, inputGainOverlayMax);
        } else {
          inputGainOverlayActive = false;
        }
      }

      // Draw channel number overlay when in draw mode
      if (channelNrOverlayActive && currentMode == &draw && showChannelNr) {
        if (millis() <= channelNrOverlayUntil && GLOB.y <= 9) {
          drawChannelNrOverlay(channelNrOverlayChannel, GLOB.currentChannel);
        } else {
          channelNrOverlayActive = false;
        }
      }

      // CTRL=PAGE page number (same gate as CRSR=CHNR)
      if (pageNrOverlayActive && showChannelNr
          && (currentMode == &draw || currentMode == &singleMode)) {
        if (millis() <= pageNrOverlayUntil) {
          drawPageNrOverlay(pageNrOverlayPage);
        } else {
          pageNrOverlayActive = false;
        }
      }

      // Yield once per frame after all drawing operations complete (replaces per-pixel yields)
      // This gives the system a chance to process other tasks without causing jitter
      yield();
      // Present the frame (throttled inside FastLEDshow()).
      FastLEDshow();
    }
  }

  // Update LED strip visualization (only if enabled - optimization #3)
  extern bool getLedStripEnabled();
  if (!fastRecordActive && getLedStripEnabled()) {
    updateLedStrip();
  }

  //granular on ch=8
  /*
if (SMP.filter_settings[8][ACTIVE]>0){
      unsigned long granulartime = mapf(SMP.filter_settings[8][PITCH], 0, maxfilterResolution, 0.0, 1500.0); 
                 if (millis() - ganularStartTime > granulartime){
                granular1.beginFreeze(SMP.filter_settings[8][OFFSET]);
                ganularStartTime = millis();
                }
}else{granular1.stop();}
*/

  if (!fastRecordActive && previewIsPlaying) {
    static elapsedMillis peakCaptureTimer;
    if (peakCaptureTimer > 15) {  // capture peaks at ~66 fps max
      peakCaptureTimer = 0;
      // Capture peaks from the audible preview for both ON and PRESS modes while playing
      if (playSdWav1.isPlaying() && g_previewUseLivePeaks && peakIndex < maxPeaks) {
        extern AudioAnalyzePeak peak1;
        if (peak1.available()) {
          peakValues[peakIndex] = peak1.read();
          peakIndex++;
        }
      }
    }

    if (!playSdWav1.isPlaying()) {
      playSdWav1.stop();
      previewIsPlaying = false;  // Playback finished

      // In PREV=="PRESS" mode: do NOT resume peak scan after playback
      // Peaks are locked when encoder(0) is pressed - they should not be modified
      if (previewTriggerMode == PREVIEW_MODE_PRESS) {
        extern bool isEncoder0PressedMode();
        extern void setEncoder0PressedMode(bool state);
        setEncoder0PressedMode(false);  // Clear flag
        // Do NOT resume peak scan - peaks are locked and should not be modified
      }
    }
  }


  checkEncoders();
  if (!fastRecordActive && deviceHasFaders) {
    updateNeoSliderVolume();
  }
  // Never draw the cursor while in MENU (or its submenus).
  // Never draw the grid cursor on screens that own the whole matrix.
  // FILE (load/save) and PACK redraw only when the slot changes, so a cursor
  // drawn on the idle frames stays on top of those screens.
  if (!fastRecordActive && currentMode != &velocity && currentMode != &filterMode && currentMode != &menu
      && currentMode != &set_Wav && currentMode != &recordMode
      && currentMode != &loadSaveTrack && currentMode != &set_SamplePack) {
    drawCursor();
  }
  checkButtons();
  checkTouchInputs();

  // While capturing: drain queue again, then skip paint / SD / mixer slew work.
  if (fastRecordActive) {
    flushAudioQueueToRAM();
    yield();
    return;
  }

  checkPendingSampleNotes();
  serviceSetWavSyncPreview();
  serviceSdPreviewRequests();

  // Periodic system stats to Serial removed (requested): keep runtime silent by default.

  yield();  // Yield periodically to prevent unresponsiveness, especially during file operations

  // === INPUT MONITORING WHEN IN DRAW MODE ===
  // Enable if monitoring toggle is ON (y==1 only) or ALL (always on), and not in record mode
  static bool drawModeInputMonitorActive = false;
  bool shouldMonitor = false;
  if (currentMode == &draw && currentMode->name != "RECORD_MODE") {
    if (inputMonitoringState == 1 && GLOB.y == 1) {
      // ON mode: only when y==1
      shouldMonitor = true;
    } else if (inputMonitoringState == 2) {
      // ALL mode: always on regardless of y position
      shouldMonitor = true;
    }
  }

  if (shouldMonitor) {
    extern AudioMixer4 mixer_end;
    extern AudioAmplifier audioInputAmp;
    extern int recMode;

    // Enable input monitoring with current gain settings
    audioInputAmp.gain(1.0f);  // Unity gain, no additional amplification

    float monitorGain = 0.0f;
    const float maxPlaybackGain = MIX_BUS_HEADROOM * MIX_END_SAMPLES_GAIN;  // Match typical single-hit playback level
    if (recMode == 1) {
      // Mic input: map micGain (0-63) to mixer gain (0.0-maxPlaybackGain) to match loudest playback
      monitorGain = mapf((float)micGain, 0.0f, 63.0f, 0.0f, maxPlaybackGain);
    } else {
      // Line input: map lineInLevel (0-15) to mixer gain (0.0-maxPlaybackGain) to match loudest playback
      monitorGain = mapf((float)lineInLevel, 0.0f, 15.0f, 0.0f, maxPlaybackGain);
    }

    mixer_end.gain(3, monitorGain);
    drawModeInputMonitorActive = true;
  } else if (drawModeInputMonitorActive && currentMode->name != "RECORD_MODE") {
    // Disable monitoring when conditions are no longer met
    extern AudioMixer4 mixer_end;
    mixer_end.gain(3, 0.0f);
    drawModeInputMonitorActive = false;
  }

  // Advance ALL active filter-mixer crossfades (not only the selected channel).
  // Updating only currentChannel froze mid-PASS transitions on neighbors → silent
  // until a filter/EFX reset snapped gains (matches "fixed once after filter reset").
  updateAllMixerGains();

  // Recovery mechanism: Detect and reset stuck pressed[] states
  // If pressed[] is true but no button event is active, it might be stuck
  static unsigned long pressedStateTime[NUM_ENCODERS] = { 0, 0, 0, 0 };
  static bool lastPressedState[NUM_ENCODERS] = { false, false, false, false };
  unsigned long now = millis();
  for (int i = 0; i < NUM_ENCODERS; i++) {
    if (pressed[i] != lastPressedState[i]) {
      // State changed - reset timer
      pressedStateTime[i] = now;
      lastPressedState[i] = pressed[i];
    } else if (pressed[i] && (now - pressedStateTime[i] > 2000)) {
      // pressed[i] has been true for 2+ seconds without change - likely stuck
      // Check if button is actually pressed by reading encoder status
      uint8_t encoderStatus = Encoder[i].readStatus();
      bool actualButtonPressed = (encoderStatus != 0xFF && (encoderStatus & 0x08) != 0);
      if (!actualButtonPressed) {
        // Hardware says button is NOT pressed but pressed[i] is true - force reset
        pressed[i] = false;
        pressedStateTime[i] = 0;
      }
    }
  }

  // Recovery mechanism: Auto-reset preventPaintUnpaint if stuck for too long
  static unsigned long preventPaintUnpaintSetTime = 0;
  static bool lastPreventState = false;
  if (preventPaintUnpaint != lastPreventState) {
    preventPaintUnpaintSetTime = now;
    lastPreventState = preventPaintUnpaint;
  } else if (preventPaintUnpaint && (now - preventPaintUnpaintSetTime > 5000)) {
    // preventPaintUnpaint has been true for 5+ seconds - likely stuck, force reset
    preventPaintUnpaint = false;
    preventPaintUnpaintSetTime = 0;
  }

  // Handle encoder presses based on DRAW mode
  extern int drawMode;  // 0 = L+R (default), 1 = R (right-hand only)

  if (drawMode == 0) {
    // L+R mode: encoder(3) paints, encoder(0) unpaints.
    // IMG short-press paint/cycle is handled in checkMode via "0001" (avoid double-fire here).
    if (!imageMode && note[cursorNoteStep()][GLOB.y].channel == 0
        && (currentMode == &draw || currentMode == &singleMode) && pressed[3] == true && !preventPaintUnpaint) {
      paintMode = false;
      freshPaint = true;
      unpaintMode = false;
      pressed[3] = false;
      paint();
      preventPaintUnpaint = false;
    }

    if ((currentMode == &draw || currentMode == &singleMode) && pressed[0] == true && !preventPaintUnpaint) {
      // Page-row clear is long-press (2000) only — don't wipe on press-down.
      if (GLOB.y == 16) {
        pressed[0] = false;
      } else {
        paintMode = false;
        unpaintMode = false;
        pressed[0] = false;
        unpaint();
      }
    }
  } else if (!childLockEnabled) {
    // R mode: encoder(3) short press is handled in checkMode() using button events
    // encoder(0) velocity editor is handled below

    // R mode: encoder(0) shows velocity editor only while held
    static Mode *rModeSavedMode = nullptr;
    static bool encoder0PressedOnEmptyNote = false;  // Track if encoder(0) was pressed on empty note
    extern bool isPressed[NUM_ENCODERS];

    // Check if encoder(0) button is currently pressed.
    bool encoder0Held = isPressed[0];
    // In R mode, velocity editor should open only on long press.
    bool encoder0LongHeld = (buttons[0] == 2);

    // Track when encoder(0) is pressed on an empty note
    static bool lastEncoder0State = false;
    if (encoder0Held && !lastEncoder0State) {
      // Encoder(0) was just pressed - check if note has value
      if (note[GLOB.x][GLOB.y].channel == 0) {
        encoder0PressedOnEmptyNote = true;  // Mark that it was pressed on empty note
      } else {
        encoder0PressedOnEmptyNote = false;  // Reset if pressed on note with value
      }
    }
    lastEncoder0State = encoder0Held;

    // Reset flag when encoder(0) is released
    if (!encoder0Held) {
      encoder0PressedOnEmptyNote = false;
    }

    if ((currentMode == &draw || currentMode == &singleMode) && encoder0LongHeld && !imageMode) {
      // Long press reached - enter velocity mode if not already in it
      // Only trigger if note has value AND encoder(0) was not pressed on empty note
      if (currentMode != &velocity && !encoder0PressedOnEmptyNote) {
        rModeSavedMode = currentMode;
        if (!freshPaint && note[GLOB.x][GLOB.y].channel != 0) {
          unsigned int velo = round(mapf(note[GLOB.x][GLOB.y].velocity, 1, 127, 1, maxY));
          unsigned int chvol = SMP.channelVol[GLOB.currentChannel];
          GLOB.velocity = velo;

          // Map probability to encoder range 1-5 (0%, 25%, 50%, 75%, 100%)
          unsigned int prob = note[GLOB.x][GLOB.y].probability;
          unsigned int probStep;
          if (prob == 0) probStep = 1;
          else if (prob == 25) probStep = 2;
          else if (prob == 50) probStep = 3;
          else if (prob == 75) probStep = 4;
          else probStep = 5;  // 100%

          unsigned int condStep =
              noteConditionToStep(note[GLOB.x][GLOB.y].condition);

          GLOB.singleMode = (rModeSavedMode == &singleMode);
          suppressDrawRMuteUntilMs = millis() + 800;
          switchMode(&velocity);
          Encoder[0].writeCounter((int32_t)velo);
          Encoder[1].writeCounter((int32_t)probStep);
          Encoder[2].writeCounter((int32_t)condStep);
          Encoder[3].writeCounter((int32_t)chvol);
          currentMode->pos[1] = probStep;
          currentMode->pos[2] = condStep;
          currentMode->pos[3] = chvol;
        }
      }
    } else if (currentMode == &velocity && rModeSavedMode != nullptr && !encoder0Held) {
      // Button released - exit velocity mode and return to saved mode.
      // Never toggle global mute from velocity entry/exit flow.
      switchMode(rModeSavedMode);
      rModeSavedMode = nullptr;
    }
  }

  // Handle encoder 1 press in SET_WAV mode - reverse preview sample
  // (Encoder functions are swapped: Encoder[2]=folder select, Encoder[1]=seekEnd + invert)
  if (currentMode == &set_Wav && pressed[1] == true && !isRecording) {
    pressed[1] = false;
    reversePreviewSample();
  }

  if (childLockEnabled && (currentMode == &filterMode || currentMode == &velocity || currentMode == &subpatternMode)) {
    switchMode(GLOB.singleMode ? &singleMode : &draw);
  }

  // Set stateMashine
  if (currentMode->name == "FILTERMODE") {
    //setFilters();

    setNewFilters();

  } else if (currentMode->name == "VOLUME_BPM") {
    setVolume();
  } else if (currentMode->name == "VELOCITY") {
    setVelocity();
  } else if (currentMode->name == "LOADSAVE_TRACK") {
    showLoadSave();
  } else if (currentMode->name == "MENU") {
    extern bool inLookSubmenu;
    extern bool inRecsSubmenu;
    extern bool inMidiSubmenu;
    extern bool inVolSubmenu;
    extern bool inEtcSubmenu;
    extern void showLookMenu();
    extern void showRecsMenu();
    extern void showMidiMenu();
    extern void showVolMenu();
    extern void showEtcMenu();
    if (inLookSubmenu) {
      showLookMenu();
    } else if (inRecsSubmenu) {
      showRecsMenu();
    } else if (inMidiSubmenu) {
      showMidiMenu();
    } else if (inVolSubmenu) {
      showVolMenu();
    } else if (inEtcSubmenu) {
      showEtcMenu();
    } else {
      showMenu();
    }
  } else if (currentMode->name == "SET_SAMPLEPACK") {
    showSamplePack();
  } else if (currentMode->name == "SET_WAV") {
    if (isRecording) { /* Do Nothing */
    }                  // Avoid return here if FastLEDshow is needed
    else { showWave(); }
  } else if (currentMode->name == "RECORD_MODE") {
    showDoRecord();
  } else if (currentMode->name == "NOTE_SHIFT") {
    shiftNotes();
    drawBase();
    drawTriggers();
    if (isNowPlaying) {
      //filtercheck
      drawTimer();
    }
  } else if (currentMode->name == "NEW_FILE") {
    showNewFileMode();
  } else if (currentMode->name == "SUBPATTERN") {
    switchSubPattern();
  } else if (currentMode->name == "SONGMODE") {
    extern void showSongMode();
    showSongMode();
  }



  for (int ch = 13; ch <= 14; ch++) {
    unsigned long noteLen = getNoteDuration(ch);
    // Only auto-release if the note is not persistent (i.e. not from a live MIDI press)

    if (noteOnTriggered[ch] && !persistentNoteOn[ch] &&
        !sequencedMonoSynthActive[ch] &&
        (millis() - startTime[ch] >= noteLen)) {
      if (!envelopes[ch]) continue;
      envelopes[ch]->noteOff();
      noteOnTriggered[ch] = false;
    }
  }

  autoOffActiveNotes();

  filterfreshsetted = false;

  FastLEDshow();

  yield();
}

FLASHMEM void triggerExternalOneBlink() {
  if (MIDI_CLOCK_SEND) return;  // External clock only
  if (isNowPlaying) return;     // Only blink while waiting to start

  Encoder[EXTERNAL_ONE_ENCODER_INDEX].writeRGBCode(0xFFFFFF);  // White blink
  externalOneBlinkActive = true;

  unsigned long beatDurationMs = 120;  // default short blink
  if (SMP.bpm > 0.0f) {
    beatDurationMs = (unsigned long)(60000.0f / (SMP.bpm * 4.0f));  // quarter-beat blink
    if (beatDurationMs < 50) beatDurationMs = 50;
  }
  externalOneBlinkUntil = millis() + beatDurationMs;
}

FLASHMEM void updateExternalOneBlink() {
  if (!externalOneBlinkActive) return;
  if ((long)(millis() - externalOneBlinkUntil) >= 0) {
    externalOneBlinkActive = false;
    Encoder[EXTERNAL_ONE_ENCODER_INDEX].writeRGBCode(0x000000);  // Turn back off
  }
}

float getNoteDuration(int channel) {
  // Gate time until we send noteOff() for grid / preview / sequencer triggers.
  // Teensy AudioEffectEnvelope runs A→D→S while "on"; noteOff() starts R from the current level.
  // Release must not be included in the hold-open time — that would keep the voice in sustain
  // during what should be the release slope.
  float delayMs = mapf(SMP.param_settings[channel][DELAY], 0, maxfilterResolution, 0, maxParamVal[DELAY]);
  float attackMs = mapf(SMP.param_settings[channel][ATTACK], 0, maxfilterResolution, maxParamVal[ATTACK], 0);
  float holdMs = mapf(SMP.param_settings[channel][HOLD], 0, maxfilterResolution, 0, maxParamVal[HOLD]);
  float decayMs = mapf(SMP.param_settings[channel][DECAY], 0, maxfilterResolution, 0, maxParamVal[DECAY]);

  float gateMs = delayMs + attackMs + holdMs + decayMs;

  if (channel == 13 || channel == 14) {
    // Grid / preview triggers on the synth channels should be short single hits.
    // Send noteOff() right after the attack reaches its target; the envelope's own
    // decay / sustain / release settings then shape the rest of the sound naturally.
    gateMs = delayMs + attackMs + 8.0f;
  }

  // Ensure attack is actually reached before note-off by enforcing at least (attack + small cushion)
  float minLen = attackMs + 5.0f;  // 5ms cushion beyond attack
  if (gateMs < minLen) gateMs = minLen;

  // Absolute floor to avoid zero-length
  if (gateMs < 5.0f) gateMs = 5.0f;
  return gateMs;
}


FLASHMEM void shiftNotes() {
  unsigned int patternLength = lastPage * maxX;
  if (currentMode->pos[3] != GLOB.shiftX) {
    // Determine shift direction (+1 or -1)
    int shiftDirectionX = 0;
    if (currentMode->pos[3] > GLOB.shiftX) {
      shiftDirectionX = 1;
    } else {
      shiftDirectionX = -1;
    }
    GLOB.shiftX = 8;  // Reset conceptual center for encoder delta

    Encoder[3].writeCounter((int32_t)8);  // Reset physical encoder to center
    currentMode->pos[3] = 8;              // Reflect this in currentMode's tracked position
    // Step 1: Clear the tmp array
    for (unsigned int nx = 1; nx <= patternLength; nx++) {  // Start from 1
      for (unsigned int ny = 1; ny <= maxY; ny++) {         // Start from 1
        tmp[nx][ny].channel = 0;
        tmp[nx][ny].velocity = defaultVelocity;
        tmp[nx][ny].probability = 100;  // Default probability
        tmp[nx][ny].condition = 1;      // Default condition
        tmp[nx][ny].midiPitch = NOTE_MIDI_PITCH_NONE;
      }
    }

    // Step 2: Shift notes of the current channel into tmp array
    for (unsigned int nx = 1; nx <= patternLength; nx++) {
      for (unsigned int ny = 1; ny <= maxY; ny++) {
        if (note[nx][ny].channel == GLOB.currentChannel) {
          int newposX = nx + shiftDirectionX;

          // Handle wrapping around the edges
          if (newposX < 1) {
            newposX = patternLength;
          } else if (newposX > patternLength) {
            newposX = 1;
          }
          tmp[newposX][ny].channel = GLOB.currentChannel;
          tmp[newposX][ny].velocity = note[nx][ny].velocity;
          tmp[newposX][ny].probability = note[nx][ny].probability;
          tmp[newposX][ny].condition = note[nx][ny].condition;
          tmp[newposX][ny].midiPitch = note[nx][ny].midiPitch;
        }
      }
    }
    shifted = true;
  }

  if (currentMode->pos[0] != GLOB.shiftY) {
    // Determine shift direction (+1 or -1)
    int shiftDirectionY = 0;
    if (currentMode->pos[0] > GLOB.shiftY) {
      shiftDirectionY = -1;  // Encoder up usually means lower Y value (higher pitch)
    } else {
      shiftDirectionY = +1;  // Encoder down usually means higher Y value (lower pitch)
    }
    GLOB.shiftY = 8;  // Reset conceptual center

    Encoder[0].writeCounter((int32_t)8);  // Reset physical encoder
    currentMode->pos[0] = 8;              // Reflect in currentMode
    // Step 1: Clear the tmp array
    for (unsigned int nx = 1; nx <= patternLength; nx++) {  // Start from 1
      for (unsigned int ny = 1; ny <= maxY; ny++) {         // Start from 1
        tmp[nx][ny].channel = 0;
        tmp[nx][ny].velocity = defaultVelocity;
        tmp[nx][ny].probability = 100;  // Default probability
        tmp[nx][ny].condition = 1;      // Default condition
        tmp[nx][ny].midiPitch = NOTE_MIDI_PITCH_NONE;
      }
    }

    // Step 2: Shift notes of the current channel into tmp array
    for (unsigned int nx = 1; nx <= patternLength; nx++) {
      for (unsigned int ny = 1; ny <= 15; ny++) {
        if (note[nx][ny].channel == GLOB.currentChannel) {
          int newposY = ny + shiftDirectionY;
          // Handle wrapping around the edges
          if (newposY < 1) {
            newposY = 15;
          } else if (newposY > 15) {
            newposY = 1;
          }
          tmp[nx][newposY].channel = GLOB.currentChannel;
          tmp[nx][newposY].velocity = note[nx][ny].velocity;
          tmp[nx][newposY].probability = note[nx][ny].probability;
          tmp[nx][newposY].condition = note[nx][ny].condition;
          tmp[nx][newposY].midiPitch =
              note[nx][ny].midiPitch <= 127
                ? (uint8_t)constrain((int)note[nx][ny].midiPitch + shiftDirectionY, 0, 127)
                : NOTE_MIDI_PITCH_NONE;
        }
      }
    }
    shifted = true;
  }

  // Handle encoder 1 Y-shift for current channel and current page only
  if (currentMode->pos[1] != GLOB.shiftY1) {
    // Determine shift direction (+1 or -1)
    int shiftDirectionY1 = 0;
    if (currentMode->pos[1] > GLOB.shiftY1) {
      shiftDirectionY1 = -1;  // Encoder up usually means lower Y value (higher pitch)
    } else {
      shiftDirectionY1 = +1;  // Encoder down usually means higher Y value (lower pitch)
    }
    GLOB.shiftY1 = 8;  // Reset conceptual center

    Encoder[1].writeCounter((int32_t)8);  // Reset physical encoder
    currentMode->pos[1] = 8;              // Reflect in currentMode

    // Calculate the start and end positions for the current visible page (GLOB.edit)
    unsigned int pageStartX = ((GLOB.edit - 1) * maxX) + 1;
    unsigned int pageEndX = GLOB.edit * maxX;

    // pageTmp is a file-scope EXTMEM array — clear it before use.
    memset(pageTmp, 0, sizeof(pageTmp));

    // Step 1: Copy current page notes to pageTmp
    for (unsigned int nx = pageStartX; nx <= pageEndX; nx++) {
      for (unsigned int ny = 1; ny <= maxY; ny++) {
        pageTmp[nx - pageStartX + 1][ny] = note[nx][ny];
      }
    }

    // Step 2: Shift notes of the current channel on the current page
    // Process in the correct order to avoid overwriting unprocessed notes
    if (shiftDirectionY1 > 0) {
      // Shifting down: process from bottom to top
      for (unsigned int nx = 1; nx <= maxX; nx++) {
        for (int ny = 15; ny >= 1; ny--) {
          if (pageTmp[nx][ny].channel == GLOB.currentChannel) {
            int newposY = ny + shiftDirectionY1;
            // Handle wrapping around the edges
            if (newposY < 1) {
              newposY = 15;
            } else if (newposY > 15) {
              newposY = 1;
            }
            // Store the note data before clearing
            int originalVelocity = pageTmp[nx][ny].velocity;
            uint8_t originalProbability = pageTmp[nx][ny].probability;
            uint8_t originalCondition = pageTmp[nx][ny].condition;
            uint8_t originalMidiPitch = pageTmp[nx][ny].midiPitch;
            // Clear the old position
            pageTmp[nx][ny].channel = 0;
            pageTmp[nx][ny].velocity = defaultVelocity;
            pageTmp[nx][ny].probability = 100;  // Default probability
            pageTmp[nx][ny].condition = 1;      // Default condition
            pageTmp[nx][ny].midiPitch = NOTE_MIDI_PITCH_NONE;
            // Set the new position
            pageTmp[nx][newposY].channel = GLOB.currentChannel;
            pageTmp[nx][newposY].velocity = originalVelocity;
            pageTmp[nx][newposY].probability = originalProbability;
            pageTmp[nx][newposY].condition = originalCondition;
            pageTmp[nx][newposY].midiPitch =
                originalMidiPitch <= 127
                  ? (uint8_t)constrain((int)originalMidiPitch + shiftDirectionY1, 0, 127)
                  : NOTE_MIDI_PITCH_NONE;
          }
        }
      }
    } else {
      // Shifting up: process from top to bottom
      for (unsigned int nx = 1; nx <= maxX; nx++) {
        for (unsigned int ny = 1; ny <= 15; ny++) {
          if (pageTmp[nx][ny].channel == GLOB.currentChannel) {
            int newposY = ny + shiftDirectionY1;
            // Handle wrapping around the edges
            if (newposY < 1) {
              newposY = 15;
            } else if (newposY > 15) {
              newposY = 1;
            }
            // Store the note data before clearing
            int originalVelocity = pageTmp[nx][ny].velocity;
            uint8_t originalProbability = pageTmp[nx][ny].probability;
            uint8_t originalCondition = pageTmp[nx][ny].condition;
            uint8_t originalMidiPitch = pageTmp[nx][ny].midiPitch;
            // Clear the old position
            pageTmp[nx][ny].channel = 0;
            pageTmp[nx][ny].velocity = defaultVelocity;
            pageTmp[nx][ny].probability = 100;  // Default probability
            pageTmp[nx][ny].condition = 1;      // Default condition
            pageTmp[nx][ny].midiPitch = NOTE_MIDI_PITCH_NONE;
            // Set the new position
            pageTmp[nx][newposY].channel = GLOB.currentChannel;
            pageTmp[nx][newposY].velocity = originalVelocity;
            pageTmp[nx][newposY].probability = originalProbability;
            pageTmp[nx][newposY].condition = originalCondition;
            pageTmp[nx][newposY].midiPitch =
                originalMidiPitch <= 127
                  ? (uint8_t)constrain((int)originalMidiPitch + shiftDirectionY1, 0, 127)
                  : NOTE_MIDI_PITCH_NONE;
          }
        }
      }
    }

    // Step 3: Apply the shifted notes back to the note array for the current page only
    for (unsigned int nx = pageStartX; nx <= pageEndX; nx++) {
      for (unsigned int ny = 1; ny <= maxY; ny++) {
        note[nx][ny] = pageTmp[nx - pageStartX + 1][ny];
      }
    }
    // Don't set shifted = true to avoid triggering the global shift logic
  }


  if (shifted) {
    // Step 3: Copy original notes of other channels back to the note array
    // And apply shifted notes for current channel
    for (unsigned int nx = 1; nx <= patternLength; nx++) {
      for (unsigned int ny = 1; ny <= maxY; ny++) {
        if (original[nx][ny].channel != 0 && original[nx][ny].channel != GLOB.currentChannel) {  // Only copy if it's an 'other' channel note
          note[nx][ny] = original[nx][ny];
        } else {  // Clear spot for current channel notes or if it was empty in original
          note[nx][ny].channel = 0;
          note[nx][ny].velocity = defaultVelocity;
          note[nx][ny].probability = 100;  // Default probability
          note[nx][ny].condition = 1;      // Default condition
          note[nx][ny].midiPitch = NOTE_MIDI_PITCH_NONE;
        }
        // Then overlay the shifted notes for the current channel
        if (tmp[nx][ny].channel == GLOB.currentChannel) {
          note[nx][ny] = tmp[nx][ny];
        }
      }
    }
    shifted = false;
  }

  /* shift only this page:*/

  // Reset paint/unpaint prevention flag after shiftNotes operation
  preventPaintUnpaint = false;
}
void tmpMuteAll(bool pressed) {
  if (childLockEnabled) return;

  if (pressed) {
    // only on the *transition* into pressed do we save & mute
    if (!tmpMuteActive) {
      // save current mutes
      for (unsigned i = 1; i <= maxY; i++) {  // Use maxY to include all channels (1-16)
        prevMuteState[i] = getMuteState(i);
      }
      // mute all except the current channel
      for (unsigned i = 1; i <= maxY; i++) {
        setMuteState(i, (i == GLOB.currentChannel) ? false : true);
      }
      tmpMuteActive = true;
    }
  } else {
    // only on the *transition* into released do we restore
    if (tmpMuteActive) {
      for (unsigned i = 1; i <= maxY; i++) {
        setMuteState(i, prevMuteState[i]);
      }
      tmpMuteActive = false;
    }
  }
}

static void silenceAllVoicesForFullMute() {
  for (int ch = 0; ch <= 8; ch++) {
    for (int note = 36; note <= 96; note++) {
      samplerNoteEvent(ch, note, 0, false, false);
    }
  }

  stopSynthChannel(13);
  stopSynthChannel(14);
  resetMidiPressedKeyCount11to14();
}

static void syncMuteArraysToSmp() {
  for (int ch = 0; ch < maxY; ch++) {
    SMP.globalMutes[ch] = globalMutes[ch];
    SMP.mute[ch] = globalMutes[ch] ? 1u : 0u;
    for (int page = 0; page < maxPages; page++) {
      SMP.pageMutes[page][ch] = pageMutes[page][ch];
    }
  }
}

FLASHMEM void fullMuteApplyView() {
  for (int ch = 0; ch < maxY; ch++) {
    bool muted = true;
    switch (fullMuteView) {
      case FullMuteView::AllMuted:
        muted = true;
        break;
      case FullMuteView::Ch12:
        // User ch1/ch2 = mute indices 1/2 (grid y=2/3).
        muted = (ch != 1 && ch != 2);
        break;
      case FullMuteView::Custom: {
        uint16_t mask = drawRFullMuteCustomUnmuteMask;
        muted = (mask & (1u << ch)) == 0;
        break;
      }
      case FullMuteView::UnmuteAll:
        muted = false;
        break;
    }
    globalMutes[ch] = muted;
    for (int page = 0; page < maxPages; page++) {
      pageMutes[page][ch] = muted;
    }
  }
  syncMuteArraysToSmp();
  applyMutesAfterPMODSwitch();
  if (fullMuteView == FullMuteView::AllMuted) {
    silenceAllVoicesForFullMute();
  } else {
    // Stop voices that this view keeps muted (e.g. UnmuteAll -> Ch12).
    for (int ch = 0; ch < maxY; ch++) {
      if (!globalMutes[ch]) continue;
      if (ch >= 1 && ch <= 8) {
        for (int note = 36; note <= 96; note++) {
          samplerNoteEvent(ch, note, 0, false, false);
        }
      } else if (ch == 13 || ch == 14) {
        stopSynthChannel(ch);
      }
    }
  }
}

FLASHMEM void fullMuteEnter() {
  if (childLockEnabled) return;
  if (fullMuteActive) return;

  memcpy(fullMuteSavedGlobal, globalMutes, sizeof(globalMutes));
  memcpy(fullMuteSavedPages, pageMutes, sizeof(pageMutes));
  fullMuteActive = true;
  fullMuteView = FullMuteView::AllMuted;
  fullMuteApplyView();
}

FLASHMEM void fullMuteExitRestore() {
  if (!fullMuteActive) return;

  fullMuteActive = false;
  fullMuteView = FullMuteView::AllMuted;
  memcpy(globalMutes, fullMuteSavedGlobal, sizeof(globalMutes));
  memcpy(pageMutes, fullMuteSavedPages, sizeof(pageMutes));
  syncMuteArraysToSmp();
  applyMutesAfterPMODSwitch();
}

FLASHMEM void fullMuteToggleView(FullMuteView target) {
  if (!fullMuteActive) return;
  if (fullMuteView == target) {
    fullMuteView = FullMuteView::AllMuted;
  } else {
    fullMuteView = target;
  }
  fullMuteApplyView();
}


FLASHMEM void toggleMute() {
  if (childLockEnabled) return;

  // Use getMuteStateForUI() to get mute state from the displayed page (GLOB.edit),
  // not the playing page (GLOB.page). This ensures toggling works correctly in NEXT mode.
  bool currentMuteState = getMuteStateForUI(GLOB.currentChannel);
  setMuteState(GLOB.currentChannel, !currentMuteState);
}

void deleteActiveCopy() {

  GLOB.activeCopy = false;
}



void play(bool fromStart) {
  // MIDI Start is now sent by resetMidiClockForTransportStart() below,
  // after all setup, so the clock timer phase and Start are aligned.

  ctrlVolumeOverlayActive = false;
  // Ensure synth voices are idle before starting
  stopSynthChannel(13);
  stopSynthChannel(14);
  resetMidiPressedKeyCount11to14();
  sequencerSynthTick = 0;
  resetSequencedSynthLegato();

  if (fromStart) {
    updateLastPage();

    // Update encoder 1 limit if pattern mode is ON
    if (currentMode == &draw || currentMode == &singleMode) {
      if (ctrlMode == 0 && SMP_PATTERN_MODE) {
        Encoder[1].writeMax((int32_t)encoderPageMax());
      } else if (ctrlMode == 1) {
        refreshCtrlEncoderConfig();
      }
    }

    lastFlowPage = 0;  // Reset FLOW page tracking when playback starts
    deleteActiveCopy();

    // In song mode, start from the first defined pattern
    extern bool songModeActive;
    extern int currentSongPosition;

    if (songModeActive) {
      // Song mode requires PMOD to be active
      patternMode = 2;  // Ensure PMOD is set to SONG
      SMP_PATTERN_MODE = true;

      // Find first non-empty position in song arrangement
      currentSongPosition = -1;
      for (int i = 0; i < 64; i++) {
        if (SMP.songArrangement[i] > 0) {
          currentSongPosition = i;
          break;
        }
      }

      if (currentSongPosition >= 0 && SMP.songArrangement[currentSongPosition] > 0) {
        int pattern = SMP.songArrangement[currentSongPosition];
        GLOB.edit = pattern;
        GLOB.page = pattern;
        beat = (pattern - 1) * maxX + 1;  // Start from first beat of first pattern
      } else {
        // No patterns defined, fall back to pattern mode behavior
        songModeActive = false;
        patternMode = 1;  // Set to normal pattern mode instead
        SMP_PATTERN_MODE = true;
        beat = (GLOB.edit - 1) * maxX + 1;  // Start from first beat of current page
        GLOB.page = GLOB.edit;
      }
    } else if (SMP_PATTERN_MODE) {
      // In pattern mode, start from the current page's first beat
      extern int patternMode;
      if (patternMode == 3) {
        // NEXT always starts the page that is visible at transport start.
        GLOB.edit = constrain(
            (int)GLOB.edit, 1, effectivePageCount());
        GLOB.page = GLOB.edit;
        pendingPage = 0;
        beat = (GLOB.page - 1) * maxX + 1;
      } else {
        // Other pattern modes: use GLOB.edit
        beat = (GLOB.edit - 1) * maxX + 1;  // Start from first beat of current page
        GLOB.page = GLOB.edit;              // Keep the current page
      }
    } else {
      beat = 1;
      GLOB.page = 1;
    }

    enforceChildModeRestrictions();

    // Reset loop count to 1 when starting playback (first loop)
    loopCount = 1;
    if (voiceMode) {
      extern bool songModeActive;
      updateVoiceLengths();
      for (int c = 0; c < 16; c++) voiceLoopCount[c] = 1;
      if (!songModeActive && !childLockEnabled) {
        beat = 1;
        GLOB.page = 1;
      }
    }

    Encoder[2].writeRGBCode(0xFFFF00);
    if (MIDI_CLOCK_SEND) {
      // Master mode: defer play until effective send-side delay elapses (SNC1 + cross from negative SNC2).
      extern unsigned long effectiveTransportSendDelayMs();
      extern void armMasterTransportStartDelay();
      extern void resetMidiClockForTransportStart();
      resetMidiClockForTransportStart();
      if (effectiveTransportSendDelayMs() == 0) {
        isNowPlaying = true;
        playStartTime = millis();
        extern void pulseClockOnTransportStart();
        pulseClockOnTransportStart();
        if (SMP.bpm > 0.0f) {
          unsigned long currentPlayNoteInterval = (unsigned long)lround(60000000.0 / ((double)SMP.bpm * 4.0));
          playTimer.end();
          playNote();
          playTimer.begin(playNote, currentPlayNoteInterval);
          if (currentPlayNoteInterval >= 4) {
            fillTimer.begin(playFillNote, currentPlayNoteInterval / 4);
          }
        } else {
          playNote();
        }
        fillHasTriggered = false;
        fillRunning = false;
        fillSubTick = 0;
        fillStartSubTick = 0;
        fillTriggerStep = 0;
        fillTriggerRow = 0;
        fillActiveChannel = 0;
        fillActiveVelocity = 0;
        fillActiveRow = 0;
        fillActiveMidiPitch = NOTE_MIDI_PITCH_NONE;
      } else {
        armMasterTransportStartDelay();
        isNowPlaying = false;
      }
    } else {
      // slave-mode: arm for the next bar-1 instead of starting now
      pendingStartOnBar = true;
      isNowPlaying = false;  // It's not playing YET. MIDI clock will start it.
      extern bool getAnalogExtClock();
      extern void analogClockCatchIfHigh();
      if (getAnalogExtClock()) analogClockCatchIfHigh();
    }
  }
  // If !fromStart, it implies a continue, which MIDI also supports.
  // However, current logic only handles fromStart explicitly for MIDI.
  // If play(false) is ever called, MIDI.sendRealTime(midi::Continue) might be appropriate if MIDI_CLOCK_SEND.
}



void pause(bool skipSave) {
  // Send MIDI Stop FIRST (before any other operations) to advance it by ~5ms
  if (MIDI_CLOCK_SEND && MIDI_TRANSPORT_SEND) {
    MIDI.sendRealTime(midi::Stop);  // Send as early as possible for better sync
  }
  MidiReleaseSequencerNotes();
  clearPendingMidiRecordNotes();
  sequencerRecordStepStartedUs = 0;

  // MIDI clock timer continues running in background - never stopped for precise timing
  // Don't reset clock state - timer keeps running in background
  // Only reset playback state

  ctrlVolumeOverlayActive = false;
  isNowPlaying = false;
  pendingStartOnBar = false;
  lastFlowPage = 0;
  fillTimer.end();
  deleteActiveCopy();

  // Stop audio voices immediately (time-critical, no I2C)
  envelope0.noteOff();
  stopSynthChannel(13);
  stopSynthChannel(14);
  resetMidiPressedKeyCount11to14();
  sequencerSynthTick = 0;
  resetSequencedSynthLegato();

  // Reset playback state immediately
  beat = 1;
  beatForUI = beat;
  GLOB.page = 1;
  loopCount = 0;
  fillHasTriggered = false;
  fillRunning = false;
  fillSubTick = 0;
  fillStartSubTick = 0;
  fillTriggerStep = 0;
  fillTriggerRow = 0;
  fillActiveChannel = 0;
  fillActiveVelocity = 0;
  fillActiveRow = 0;
  fillActiveMidiPitch = NOTE_MIDI_PITCH_NONE;

  // Defer all I2C encoder writes and SD save to next loop() iteration so the
  // MIDI clock callback isn't starved by blocking bus transactions.
  pendingPauseUIUpdate = true;
  pendingPauseSkipSave = skipSave;
}
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
