Soundpauli/toern/toern_menu.ino

// Menu page system - completely independent from maxPages
#define MENU_PAGES_COUNT 10
#define LOOK_PAGES_COUNT 12
#define RECS_PAGES_COUNT 5
#define MIDI_PAGES_COUNT 9
#define VOL_PAGES_COUNT 7
#define ETC_PAGES_COUNT 12

// PPQN page value readout: 0=rate/OFF, 1=STOP/CONT, 2=pulse width
static uint8_t g_ppqnUiFocus = 0;
static uint8_t g_cinFocus = 0;  // MIDI → CIN last turned: 0 PPQN (enc3), 1 width (enc1)
// VOL→GAIN: encoder 3 edits ALL (1) or SYN (0). Click toggles.
static uint8_t g_gainEnc3IsAll = 1;
static uint8_t g_gainUiFocus = 3; // 0=1-4, 1=5-8, 2=SYN, 3=ALL
// Encoder 1 (1–4) is inverted: hardware 0 → 2.0, hardware 20 → 0.0
static inline int mixGainEnc0FromStored(uint8_t g) {
  int v = (int)g;
  if (v < 0) v = 0;
  if (v > MIX_GAIN_MAX) v = MIX_GAIN_MAX;
  return MIX_GAIN_MAX - v;
}
static inline uint8_t mixGainStoredFromEnc0(int pos) {
  pos = constrain(pos, 0, MIX_GAIN_MAX);
  return (uint8_t)(MIX_GAIN_MAX - pos);
}

// External variables
extern Mode *currentMode;
extern int ctrlMode;
void refreshCtrlEncoderConfig();
extern bool pong;
extern uint16_t pongUpdateInterval;
extern bool MIDI_TRANSPORT_SEND;
void updatePreviewVolume();
extern int previewTriggerMode;
extern const int PREVIEW_MODE_ON;
extern const int PREVIEW_MODE_PRESS;
extern const int PREVIEW_MODE_SYNC;
extern uint8_t currentColorScheme;
extern void applyColorScheme(uint8_t scheme);
extern uint16_t drawRFullMuteCustomUnmuteMask;

static inline CRGB dimIconColorFromText(CRGB textColor);
static inline CRGB menuTextColorFromCol(uint8_t colIndex);
static inline CRGB currentMenuParentTextColor();
static inline void drawLargeIndicatorCustom(CRGB color, int encoderNum);
static inline uint32_t hashEncoderPositions(const Mode *m);
static inline void clearTextArea(int startX, int startY, int width);
static inline void drawMenuValue(const char* label, int x, int y, CRGB color);

// SETTINGS>MUTE & DRAW-R mask: user CH1..CH16 ↔ internal mute index 0..15 (same as draw: CH1=y2→internal 1; CH16=y1→internal 0).
static inline int userChToInternalDrawR(int uch) {
  if (uch < 1) uch = 1;
  if (uch > 16) uch = 16;
  return (uch == 16) ? 0 : uch;
}
static inline int internalToUserChDrawR(int in) {
  if (in < 0) in = 0;
  if (in > 15) in = 15;
  return (in == 0) ? 16 : in;
}

// Page definitions - each page contains one main setting + additional features
struct MenuPage {
  const char* name;
  int mainSetting;  // The main setting for this page (menuPosition from old system)
  bool hasAdditionalFeatures;  // Whether this page has extra controls (like mic gain)
  const char* additionalFeatureName;  // Name of additional feature if any
};

MenuPage menuPages[MENU_PAGES_COUNT] = {
  {"DAT", 1, false, nullptr},           // Load/Save
  {"KIT", 2, false, nullptr},           // Sample Pack
  {"WAV", 3, false, nullptr},           // Wave Selection
  {"BPM", 5, false, nullptr},           // BPM/Volume
  {"VOL", 26, false, nullptr},          // VOL submenu (MAIN, GAIN, LOUT, PREV, 2-CH)
  {"SETT", 19, false, nullptr},         // SETTINGS submenu (FLW, PREV, VIEW, PMD, LOOP)
  {"RECS", 20, false, nullptr},         // RECS submenu (INPT, MIC, L-IN, TRIG, CLR)
  {"MIDI", 21, false, nullptr},         // MIDI submenu (CHN, TRANSP)
  {"SONG", 22, false, nullptr},         // Song Mode - arrange patterns into songs
  {"ETC", 34, false, nullptr}           // ETC submenu (AUTO, RST)
};

// LOOK/SETTINGS submenu pages (SETTINGS menu uses LOOK submenu)
MenuPage lookPages[LOOK_PAGES_COUNT] = {
  {"FLW", 10, false, nullptr},          // Flow Mode
  {"PREV", 33, false, nullptr},         // Preview trigger mode (ON/PRSS/SYNC)
  {"VIEW", 17, false, nullptr},         // Simple Notes View
  {"PMD", 9, false, nullptr},           // Pattern Mode
  {"LOOP", 18, false, nullptr},         // Loop Length
  {"VMOD", 54, false, nullptr},         // Voice mode: each channel loops its own pages
  {"CTRL", 25, false, nullptr},         // Encoder control mode
  {"LEDS", 23, false, nullptr},         // LED mode (1, 1B, 2, 2B)
  {"PONG", 24, false, nullptr},         // Pong Toggle
  {"CRSR", 32, false, nullptr},         // Cursor type (NORM/CHNR)
  {"DRAW", 38, false, nullptr},         // DRAW mode toggle (L+R / R)
  {"MUTE", 47, false, nullptr}          // DRAW-R full mute: custom unmask set (encoder 0010 exit)
};

static inline uint16_t pongSpeedToInterval(int speed) {
  speed = constrain(speed, 1, 99);
  return static_cast<uint16_t>(mapf(speed, 1, 99, 300, 20));
}

static inline int pongIntervalToSpeed(uint16_t interval) {
  interval = constrain(interval, 20, 300);
  return static_cast<int>(mapf(interval, 300, 20, 1, 99));
}

// RECS submenu pages
MenuPage recsPages[RECS_PAGES_COUNT] = {
  {"INPT", 4, true, "GAIN"},            // Recording Mode (MIC/LINE)
  {"MIC", 30, false, nullptr},          // Microphone gain
  {"L-IN", 31, false, nullptr},         // Line input level
  {"TRIG", 11, false, nullptr},         // Fast Rec Mode (On-The-fly Recording)
  {"CLR", 12, false, nullptr}           // Rec Channel Clear
};

// MIDI submenu pages
MenuPage midiPages[MIDI_PAGES_COUNT] = {
  {"CH", 7, false, nullptr},            // MIDI Voice Select (Channel)
  {"TRAN", 8, false, nullptr},          // MIDI Transport
  {"SEND", 13, false, nullptr},         // MIDI Send (CLCK, NOTE, BOTH)
  {"RCVE", 44, false, nullptr},         // MIDI Note Receive (OFF/NOTE)
  {"CLMP", 51, false, nullptr},         // Fold incoming pitch into the visible grid (ON/OFF)
  {"SYNC", 45, false, nullptr},         // Transport delay: SNC1/SNC2 −127..+127 ms (+ = this path, − = other path)
  {"PPQN", 50, false, nullptr},         // Analog clock: enc1 width, enc2 STOP/CONT, enc3 rate + click POL
  {"SIDE", 58, false, nullptr},         // Sidechain out: which voice pulses J27
  {"CIN", 59, false, nullptr},          // Analog CLK-IN (J26): pulse count + input PPQN
};

// VOL submenu pages
MenuPage volPages[VOL_PAGES_COUNT] = {
  {"MAIN", 27, false, nullptr},         // Headphone output volume
  {"GAIN", 53, false, nullptr},         // Mix bus / synth / master trim (0.0x–2.0x, 1.0x = unity)
  {"LOUT", 28, false, nullptr},         // Line output volume
  {"PREV", 29, false, nullptr},         // Preview volume
  {"2-CH", 36, false, nullptr},         // Stereo routing: OFF, M+P, or L+R
  {"SPKR", 43, false, nullptr},         // Speaker toggle (ON/OFF)
  {"HFC", 46, false, nullptr}           // HF cut 0..256 (step 10, MAX=256) → GEQ treble band only
};

// ETC submenu pages
MenuPage etcPages[ETC_PAGES_COUNT] = {
  {"INFO", 39, false, nullptr},          // Info / version / credits
  {"RAM", 52, false, nullptr},           // Live audio/reverb/memory dashboard
  {"SD", 49, false, nullptr},            // USB Serial SD file server (active while on this page)
  {"AUTO", 15, true, "PAGES"},          // AI Song Generation + Page Count
  {"LGHT", 40, false, nullptr},          // LED Strip toggle (OFF/ON)
  {"COLR", 41, false, nullptr},          // Color scheme selection (1, 2, 3)
  {"BATT", 42, false, nullptr},          // Estimated LiPo percentage from Teensy A16 / pin 40
  {"EYES", 57, false, nullptr},          // Screensaver idle: OFF / 1MIN / 5MIN / 15MIN
  {"CHLD", 48, false, nullptr},          // Child lock: require touch2->touch1 to enter menu
  {"FIRE", 55, false, nullptr},          // Playhead sparks on one voice
  {"IMG", 56, false, nullptr},           // Image mode: black matrix, paint cycles voice/color
  {"RSET", 16, true, "MODE"}             // Reset Effects / SD Rescan (EFX or SD)
};

// --- INFO page animation state ---
static bool infoPageFirstEnter = true;
static uint32_t infoPageEnterMs = 0;

// Force a full redraw on next menu frame (used when entering/exiting menu/submenus).
static bool menuForceFullRedraw = false;
FLASHMEM void menuRequestFullRedraw() {
  menuForceFullRedraw = true;
}

FLASHMEM void togglePulseClockPolarityFromMenu() {
  extern void togglePulseClockPolarity();
  togglePulseClockPolarity();
  g_ppqnUiFocus = 0;
  menuRequestFullRedraw();
}

FLASHMEM void toggleMixGainEnc3Target() {
  g_gainEnc3IsAll = g_gainEnc3IsAll ? 0 : 1;
  g_gainUiFocus = g_gainEnc3IsAll ? 3 : 2;
  menuRequestFullRedraw();
}
static inline bool takeMenuForceFullRedraw() {
  if (!menuForceFullRedraw) return false;
  menuForceFullRedraw = false;
  return true;
}

static int textPixelWidth_3x5(const char *text) {
  if (!text) return 0;
  int w = 0;
  for (int i = 0; text[i] != '\0'; i++) {
    char c = text[i];
    if (c < 32 || c > 126) continue;
    w += alphabet[c - 32][0] + 1;  // char width + 1 space
  }
  return w;
}

FLASHMEM void resetEtcInfoPageAnimation() {
  infoPageFirstEnter = true;
  infoPageEnterMs = 0;
}

#ifndef TOERN_AUDIO_MEMORY_BLOCKS
#define TOERN_AUDIO_MEMORY_BLOCKS 96
#endif

static int etcRamMetric = 0;  // 0=AUD%, 1=REV%, 2=FREE blocks, 3=CPU%
static int lastEtcRamEnc = -1;

static int computeReverbUsagePercent() {
  // Freeverb-equipped voices: average REVERB send vs slider max.
  static const uint8_t kFreeverbChannels[] = { 1, 2, 5, 6, 7, 8, 11 };
  int sum = 0;
  int n = 0;
  for (uint8_t ch : kFreeverbChannels) {
    sum += (int)SMP.filter_settings[ch][REVERB];
    n++;
  }
  if (n <= 0) return 0;
  return constrain((sum * 100) / (n * (int)maxfilterResolution), 0, 100);
}

static int computeAudioUsedPercent() {
  int used = (int)AudioMemoryUsage();
  int pool = TOERN_AUDIO_MEMORY_BLOCKS;
  if (pool < 1) pool = 1;
  return constrain((used * 100) / pool, 0, 100);
}

static int computeAudioFreeBlocks() {
  int used = (int)AudioMemoryUsage();
  int freeBlocks = TOERN_AUDIO_MEMORY_BLOCKS - used;
  return freeBlocks < 0 ? 0 : freeBlocks;
}

FLASHMEM static void drawEtcRamPage() {
  const CRGB tc = currentMenuParentTextColor();
  drawText("RAM", 2, 10, tc);

  char line[8];
  CRGB valueColor = UI_GREEN;
  switch (etcRamMetric) {
    case 1: {
      int rev = computeReverbUsagePercent();
      snprintf(line, sizeof(line), "R%d", rev);
      valueColor = rev > 70 ? UI_YELLOW : UI_GREEN;
      break;
    }
    case 2: {
      int freeBlocks = computeAudioFreeBlocks();
      snprintf(line, sizeof(line), "F%d", freeBlocks);
      valueColor = freeBlocks < 12 ? UI_RED : (freeBlocks < 24 ? UI_YELLOW : UI_GREEN);
      break;
    }
    case 3: {
      int cpu = constrain((int)lroundf(AudioProcessorUsage()), 0, 99);
      snprintf(line, sizeof(line), "C%d", cpu);
      valueColor = cpu > 80 ? UI_RED : (cpu > 55 ? UI_YELLOW : UI_GREEN);
      break;
    }
    default: {
      int used = computeAudioUsedPercent();
      int peak = constrain(
          ((int)AudioMemoryUsageMax() * 100) / max(1, TOERN_AUDIO_MEMORY_BLOCKS),
          0, 100);
      // Prefer live usage; show peak when it is clearly higher.
      if (peak > used + 5) {
        snprintf(line, sizeof(line), "A%d", peak);
      } else {
        snprintf(line, sizeof(line), "A%d", used);
      }
      valueColor = used > 85 ? UI_RED : (used > 65 ? UI_YELLOW : UI_GREEN);
      break;
    }
  }
  drawMenuValue(line, 2, 3, valueColor);
  drawIndicator('L', 'G', 3, false, false);
}

FLASHMEM static void drawEtcInfoPage() {
  // Layout matches other menu pages: title at y=10, value at y=3.
  drawText("INFO", 2, 10, currentMenuParentTextColor());

  const uint32_t now = millis();
  if (infoPageFirstEnter) {
    infoPageFirstEnter = false;
    infoPageEnterMs = now;
  }

  // Phase 1: show version in yellow for 2 seconds
  const uint32_t holdMs = 2000;
  if (now - infoPageEnterMs < holdMs) {
    drawText(VERSION, 2, 3, CRGB(255, 255, 0));  // yellow version number below
    return;
  }

  // Phase 2: scroll version left while scrolling in the thank-you text from the right
  static const char *kMsg =
    "   Thank you for using TOERN. Shout out to Matzesampler, Sabrina, Hairy and all others for supporting me. Jan";

  const uint32_t scrollStartMs = infoPageEnterMs + holdMs;
  const uint32_t elapsedMs = (now >= scrollStartMs) ? (now - scrollStartMs) : 0;
  const uint32_t msPerPixel = 60;  // scroll speed (lower = faster)
  const int offsetPx = (int)(elapsedMs / msPerPixel);

  const int versionBaseX = 2;
  const int versionX = versionBaseX - offsetPx;
  const int msgStartX = (int)maxX + 1;
  const int msgX = msgStartX - offsetPx;

  drawText(VERSION, versionX, 3, CRGB(255, 255, 0));  // yellow, scrolling out
  drawText(kMsg, msgX, 3, UI_WHITE);                   // white, scrolling in

  // Loop once the message has fully exited left.
  const int msgW = textPixelWidth_3x5(kMsg);
  if (msgX < -msgW - 2) {
    infoPageEnterMs = now;
  }
}


int currentMenuPage = 0;
int currentLookPage = 0;
int currentRecsPage = 0;
int currentMidiPage = 0;
int currentVolPage = 0;
int currentEtcPage = 0;
bool inLookSubmenu = false;
bool inRecsSubmenu = false;
bool inMidiSubmenu = false;
bool inVolSubmenu = false;
bool inEtcSubmenu = false;
bool menuEnteredFromSingleMode = false;  // Restore draw vs single when exiting from submenu

// After leaving the menu (or a menu child screen), keep last main page for this long;
// reopen later → jump back to FILE (page 0).
static unsigned long menuExitMs = 0;
static const unsigned long MENU_REENTRY_GRACE_MS = 5000;

FLASHMEM void noteMenuExit() {
  menuExitMs = millis();
}

// Shared enc3 min/max cache across all menu/submenu screens. Per-screen statics
// skipped writeMax when wantMax matched a prior visit, while switchMode/draw had
// already raised HW max (menu.maxValues[3]=16) → dead steps past last page.
static int g_cachedEnc3Max = -999;
static int g_cachedEnc3Min = -999;

FLASHMEM void invalidateEnc3RangeCache() {
  g_cachedEnc3Max = -999;
  g_cachedEnc3Min = -999;
}

FLASHMEM static void ensureEnc3Range(int wantMin, int wantMax) {
  if (g_cachedEnc3Max != wantMax) {
    Encoder[3].writeMax((int32_t)wantMax);
    g_cachedEnc3Max = wantMax;
  }
  if (g_cachedEnc3Min != wantMin) {
    Encoder[3].writeMin((int32_t)wantMin);
    g_cachedEnc3Min = wantMin;
  }
}

FLASHMEM void prepareMenuEntry() {
  // switchMode(&menu) writes Mode.maxValues[3] (16) before showMenu runs —
  // drop cache so the active page-count max is re-applied.
  invalidateEnc3RangeCache();
  if (menuExitMs != 0 && (millis() - menuExitMs) >= MENU_REENTRY_GRACE_MS) {
    currentMenuPage = 0;
    inLookSubmenu = false;
    inRecsSubmenu = false;
    inMidiSubmenu = false;
    inVolSubmenu = false;
    inEtcSubmenu = false;
    currentLookPage = 0;
    currentRecsPage = 0;
    currentMidiPage = 0;
    currentVolPage = 0;
    currentEtcPage = 0;
  }
  extern Mode menu;
  menu.pos[3] = currentMenuPage;
}
int aiTargetPage = 6; // Default target page for AI song generation
int aiBaseStartPage = 1; // Start of base page range for AI analysis
int aiBaseEndPage = 1;   // End of base page range for AI analysis

// Genre generation variables
int genreType = 0; // 0=BLNK, 1=TECH, 2=HIPH, 3=DNB, 4=HOUS, 5=AMBT
int genreLength = 8; // Default length for genre generation

// NEW mode state management
bool newScreenFirstEnter = true;

// Reset menu option: 0 = SD, 1 = EFX, 2 = FULL, 3 = FILE, 4 = PACK, 5 = ASAV (wipe autosaved.txt)
int resetMenuOption = 0;

// DRAW mode: 0 = L+R (default), 1 = R (right-hand only)
int drawMode = 0;

// --- Settings backup (EEPROM <-> SD) ---
// We back up the menu/settings EEPROM block to a small text file on the SD card.
// This lets you restore settings if EEPROM is empty/corrupt after a brownout.
static const char *SETTINGS_BACKUP_PATH = "settings.txt";
static const char *SETTINGS_BACKUP_TMP_PATH = "settings.tmp";
static const char *SETTINGS_BACKUP_HEADER = "TOERN_SETTINGS_V1";
static const uint16_t SETTINGS_EEPROM_BLOCK_LEN = 54; // [53]=CIN PPQN idx + hold-off; [52]=EXT analog CLK-IN; [51]=SIDE …
static const uint16_t EEPROM_SAMPLEPACK_ADDR = 0;
static const uint16_t EEPROM_SP0_STATE_ADDR = 200;
static const uint8_t EEPROM_SP0_STATE_COUNT = 8;
static bool settingsBackupDirty = false;
static uint32_t settingsBackupDirtyMs = 0;
static const uint32_t SETTINGS_BACKUP_DEBOUNCE_MS = 1500;
// Bits 0..3 = 1-4 / 5-8 / SYN / ALL — EEPROM write deferred while sequencer plays
// (Teensy EEPROM is flash-backed; mid-playback writes stall FlexSPI and can bus-fault
// the audio eDMA → CrashReport / HalfKay 7-blink reboot after ~8s).
static uint8_t g_pendingMixGainMask = 0;
static bool g_pendingSp0Eeprom = false;
// All other settings-block bytes deferred the same way while isNowPlaying.
static uint8_t g_pendingEepromBytes[SETTINGS_EEPROM_BLOCK_LEN];
static uint8_t g_pendingEepromMask[(SETTINGS_EEPROM_BLOCK_LEN + 7) / 8];
static bool g_pendingEepromAny = false;

static inline void pendingEepromSet(int index, uint8_t value) {
  if (index < 0 || index >= (int)SETTINGS_EEPROM_BLOCK_LEN) return;
  g_pendingEepromBytes[index] = value;
  g_pendingEepromMask[index >> 3] |= (uint8_t)(1u << (index & 7));
  g_pendingEepromAny = true;
}

FLASHMEM static void flushPendingEepromWrites() {
  if (!g_pendingEepromAny) return;
  for (int i = 0; i < (int)SETTINGS_EEPROM_BLOCK_LEN; i++) {
    if (g_pendingEepromMask[i >> 3] & (uint8_t)(1u << (i & 7))) {
      EEPROM.write(EEPROM_DATA_START + i, g_pendingEepromBytes[i]);
    }
  }
  memset(g_pendingEepromMask, 0, sizeof(g_pendingEepromMask));
  g_pendingEepromAny = false;
}

// Large buffers off DTCM: only used from loadMenuFromEEPROM / readSettingsBackupFromSD (single-threaded).
EXTMEM static char g_settingsBackupReadLine[1024];
EXTMEM static uint8_t g_eepromRestoredBlock[SETTINGS_EEPROM_BLOCK_LEN];
EXTMEM static uint8_t g_eepromRestoredSp0[EEPROM_SP0_STATE_COUNT];

static inline uint32_t crc32_update(uint32_t crc, uint8_t data) {
  crc ^= data;
  for (int i = 0; i < 8; i++) {
    crc = (crc & 1) ? (crc >> 1) ^ 0xEDB88320UL : (crc >> 1);
  }
  return crc;
}

static uint32_t crc32_compute(const uint8_t *data, size_t len) {
  uint32_t crc = 0xFFFFFFFFUL;
  for (size_t i = 0; i < len; i++) crc = crc32_update(crc, data[i]);
  return ~crc;
}

static bool readLine(File &f, char *buf, size_t bufSize) {
  if (!f) return false;
  size_t idx = 0;
  while (f.available()) {
    int c = f.read();
    if (c < 0) break;
    if (c == '\r') continue;
    if (c == '\n') break;
    if (idx + 1 < bufSize) buf[idx++] = (char)c;
  }
  buf[idx] = 0;
  // If we read nothing and hit EOF, signal failure
  if (idx == 0 && !f.available()) return false;
  return true;
}

static int hexNibble(char c) {
  if (c >= '0' && c <= '9') return c - '0';
  if (c >= 'a' && c <= 'f') return 10 + (c - 'a');
  if (c >= 'A' && c <= 'F') return 10 + (c - 'A');
  return -1;
}

static bool decodeHexBytes(const char *hex, uint8_t *out, size_t outLen) {
  for (size_t i = 0; i < outLen; i++) {
    int hi = hexNibble(hex[i * 2]);
    int lo = hexNibble(hex[i * 2 + 1]);
    if (hi < 0 || lo < 0) return false;
    out[i] = (uint8_t)((hi << 4) | lo);
  }
  return true;
}

static void encodeHexBytes(const uint8_t *in, size_t inLen, char *out, size_t outSize) {
  // NOTE: Arduino defines HEX as a macro (base 16 for Print::print), so don't use HEX as an identifier.
  static const char *HEX_CHARS = "0123456789ABCDEF";
  size_t needed = inLen * 2 + 1;
  if (outSize < needed) {
    if (outSize > 0) out[0] = 0;
    return;
  }
  for (size_t i = 0; i < inLen; i++) {
    out[i * 2]     = HEX_CHARS[(in[i] >> 4) & 0xF];
    out[i * 2 + 1] = HEX_CHARS[in[i] & 0xF];
  }
  out[inLen * 2] = 0;
}

void markSettingsBackupDirty() {
  settingsBackupDirty = true;
  settingsBackupDirtyMs = millis();
}

FLASHMEM static bool writeSettingsBackupToSD() {
  extern void stopSdPreviewIfPlaying();
  stopSdPreviewIfPlaying();

  // payload = samplePackID (4 bytes, 0 = SP0 fallback) + settings block + SP0 override flags
  unsigned int spid = 1;
  EEPROM.get(EEPROM_SAMPLEPACK_ADDR, spid);
  if (spid > 999) {
    spid = 0;
  }

  uint8_t block[SETTINGS_EEPROM_BLOCK_LEN];
  for (uint16_t i = 0; i < SETTINGS_EEPROM_BLOCK_LEN; i++) {
    block[i] = (uint8_t)EEPROM.read(EEPROM_DATA_START + i);
  }

  uint8_t sp0Block[EEPROM_SP0_STATE_COUNT];
  for (uint8_t i = 0; i < EEPROM_SP0_STATE_COUNT; i++) {
    sp0Block[i] = (uint8_t)EEPROM.read(EEPROM_SP0_STATE_ADDR + 1 + i);
  }

  uint8_t payload[sizeof(unsigned int) + SETTINGS_EEPROM_BLOCK_LEN + EEPROM_SP0_STATE_COUNT];
  memcpy(payload, &spid, sizeof(unsigned int));
  memcpy(payload + sizeof(unsigned int), block, SETTINGS_EEPROM_BLOCK_LEN);
  memcpy(payload + sizeof(unsigned int) + SETTINGS_EEPROM_BLOCK_LEN, sp0Block, EEPROM_SP0_STATE_COUNT);
  uint32_t crc = crc32_compute(payload, sizeof(payload));

  // Write atomically: settings.tmp -> rename to settings.txt
  if (SD.exists(SETTINGS_BACKUP_TMP_PATH)) SD.remove(SETTINGS_BACKUP_TMP_PATH);
  File f = SD.open(SETTINGS_BACKUP_TMP_PATH, O_WRITE | O_CREAT | O_TRUNC);
  if (!f) return false;

  f.println(SETTINGS_BACKUP_HEADER);
  f.print("LEN=");
  f.println((unsigned int)sizeof(payload));
  f.print("CRC=");
  f.println(crc, HEX);
  f.print("DATA=");
  char hex[(sizeof(payload) * 2) + 1];
  encodeHexBytes(payload, sizeof(payload), hex, sizeof(hex));
  f.println(hex);
  f.close();

  if (SD.exists(SETTINGS_BACKUP_PATH)) SD.remove(SETTINGS_BACKUP_PATH);
  if (!SD.rename(SETTINGS_BACKUP_TMP_PATH, SETTINGS_BACKUP_PATH)) {
    // Fallback: if rename fails, keep tmp as evidence
    return false;
  }
  return true;
}

FLASHMEM static bool readSettingsBackupFromSD(unsigned int &outSamplePackID, uint8_t *outBlock, size_t outBlockLen, uint8_t *outSp0Block, size_t outSp0BlockLen) {
  if (!SD.exists(SETTINGS_BACKUP_PATH)) return false;
  File f = SD.open(SETTINGS_BACKUP_PATH, FILE_READ);
  if (!f) return false;

  char *const line = g_settingsBackupReadLine;
  if (!readLine(f, line, sizeof(g_settingsBackupReadLine))) { f.close(); return false; }
  if (strcmp(line, SETTINGS_BACKUP_HEADER) != 0) { f.close(); return false; }

  if (!readLine(f, line, sizeof(g_settingsBackupReadLine))) { f.close(); return false; }
  if (strncmp(line, "LEN=", 4) != 0) { f.close(); return false; }
  unsigned int len = (unsigned int)atoi(line + 4);

  if (!readLine(f, line, sizeof(g_settingsBackupReadLine))) { f.close(); return false; }
  if (strncmp(line, "CRC=", 4) != 0) { f.close(); return false; }
  uint32_t expectedCrc = (uint32_t)strtoul(line + 4, nullptr, 16);

  if (!readLine(f, line, sizeof(g_settingsBackupReadLine))) { f.close(); return false; }
  if (strncmp(line, "DATA=", 5) != 0) { f.close(); return false; }
  const char *hex = line + 5;

  // Backward compatible: allow older backups with smaller EEPROM blocks.
  const size_t minLen = sizeof(unsigned int) + 1; // at least 1 byte of settings
  const size_t maxLen = sizeof(unsigned int) + SETTINGS_EEPROM_BLOCK_LEN + EEPROM_SP0_STATE_COUNT;
  if (len < minLen || len > maxLen) { f.close(); return false; }
  if (strlen(hex) < (size_t)len * 2) { f.close(); return false; }

  uint8_t payload[sizeof(unsigned int) + SETTINGS_EEPROM_BLOCK_LEN + EEPROM_SP0_STATE_COUNT];
  if (!decodeHexBytes(hex, payload, (size_t)len)) { f.close(); return false; }
  uint32_t crc = crc32_compute(payload, (size_t)len);
  if (crc != expectedCrc) { f.close(); return false; }

  // Unpack
  memcpy(&outSamplePackID, payload, sizeof(unsigned int));
  if (outBlockLen < SETTINGS_EEPROM_BLOCK_LEN) { f.close(); return false; }
  memset(outBlock, 0, SETTINGS_EEPROM_BLOCK_LEN);
  // Added after the V1 backup format shipped: an absent CLMP byte must preserve
  // the historical pitch-folding behavior (ON), not restore as OFF.
  outBlock[37] = 1;
  // GAIN defaults applied after memcpy (see below) so short/old backups don't mute.
  if (outSp0BlockLen < EEPROM_SP0_STATE_COUNT) { f.close(); return false; }
  memset(outSp0Block, 0, EEPROM_SP0_STATE_COUNT);
  // Payload layout: samplePackID (4) + settings block (variable up to SETTINGS_EEPROM_BLOCK_LEN) + sp0 (8).
  // Older backups used a shorter block; never read SP0 bytes into the settings block when block grows.
  {
    size_t totalAfterSpid = (size_t)len - sizeof(unsigned int);
    size_t blkInFile = 0;
    size_t sp0Copy = 0;
    if (totalAfterSpid >= EEPROM_SP0_STATE_COUNT) {
      blkInFile = totalAfterSpid - EEPROM_SP0_STATE_COUNT;
      sp0Copy = EEPROM_SP0_STATE_COUNT;
    } else {
      blkInFile = totalAfterSpid;
    }
    size_t blkCopy = blkInFile;
    if (blkCopy > SETTINGS_EEPROM_BLOCK_LEN) blkCopy = SETTINGS_EEPROM_BLOCK_LEN;
    memcpy(outBlock, payload + sizeof(unsigned int), blkCopy);
    if (sp0Copy > 0) {
      memcpy(outSp0Block, payload + sizeof(unsigned int) + blkInFile, sp0Copy);
    }
    // CLMP absent in short backups
    if (blkCopy <= 37) outBlock[37] = 1;
    // VOL→GAIN (38–41): absent, virgin 0xFF, or zero-padded old backups → 1.0×
    {
      const bool gainAbsentOrBlank =
          (blkCopy <= 38) ||
          ((outBlock[38] | outBlock[39] | outBlock[40] | outBlock[41]) == 0);
      for (int i = 38; i <= 41; i++) {
        if (blkCopy <= (size_t)i || outBlock[i] > MIX_GAIN_MAX || gainAbsentOrBlank) {
          outBlock[i] = (uint8_t)MIX_GAIN_UNITY;
        }
      }
    }
  }
  f.close();
  return true;
}

FLASHMEM void serviceSettingsBackup() {
  // Persist anything deferred while the sequencer was running.
  extern bool isNowPlaying;
  extern uint8_t mixGain14;
  extern uint8_t mixGain58;
  extern uint8_t mixGainSynth;
  extern uint8_t mixGainMaster;
  if (!isNowPlaying) {
    if (g_pendingMixGainMask) {
      if (g_pendingMixGainMask & 0x01) EEPROM.write(EEPROM_DATA_START + EEPROM_MIX_GAIN_14, mixGain14);
      if (g_pendingMixGainMask & 0x02) EEPROM.write(EEPROM_DATA_START + EEPROM_MIX_GAIN_58, mixGain58);
      if (g_pendingMixGainMask & 0x04) EEPROM.write(EEPROM_DATA_START + EEPROM_MIX_GAIN_SYN, mixGainSynth);
      if (g_pendingMixGainMask & 0x08) EEPROM.write(EEPROM_DATA_START + EEPROM_MIX_GAIN_ALL, mixGainMaster);
      g_pendingMixGainMask = 0;
      markSettingsBackupDirty();
    }
    if (g_pendingEepromAny) {
      flushPendingEepromWrites();
      markSettingsBackupDirty();
    }
    // SP0 voice flags deferred while playing (same flash/bus-fault class as mix-gain).
    if (g_pendingSp0Eeprom) {
      g_pendingSp0Eeprom = false;
      saveSp0StateToEEPROM();
    }
  }

  if (!settingsBackupDirty) return;
  // Defer SD write while sequencer is playing — keep dirty and retry when stopped.
  if (isNowPlaying) return;
  if ((uint32_t)(millis() - settingsBackupDirtyMs) < SETTINGS_BACKUP_DEBOUNCE_MS) return;
  // Best effort: if SD write fails, keep dirty flag and try later.
  if (writeSettingsBackupToSD()) {
    settingsBackupDirty = false;
  }
}

// Flush settings + SP0 backup to SD immediately (no debounce). Use after load/save paths
// that should not leave a multi-second deferred write for loop() / DRAW mode.
// While playing, leave dirty so serviceSettingsBackup flushes after stop.
FLASHMEM void flushSettingsBackupNow() {
  if (!settingsBackupDirty) return;
  extern bool isNowPlaying;
  if (isNowPlaying) return;
  if (writeSettingsBackupToSD()) {
    settingsBackupDirty = false;
  }
}

FLASHMEM static uint16_t hfcNormalize256(uint16_t h) {
  if (h >= 256u) return 256u;
  return (uint16_t)((h / 10u) * 10u);
}

FLASHMEM static uint16_t hfcMigrate22000To256(uint16_t oldv) {
  if (oldv > 22000u) oldv = 22000u;
  oldv = (uint16_t)((oldv / 100u) * 100u);
  uint32_t m = (uint32_t)oldv * 256u + 11000u;
  uint16_t hv = (uint16_t)(m / 22000u);
  return hfcNormalize256(hv);
}

FLASHMEM static uint16_t hfcMigrate44200To256(uint16_t raw3) {
  if (raw3 > 44200u) raw3 = 44200u;
  raw3 = (uint16_t)((raw3 / 100u) * 100u);
  uint32_t m = (uint32_t)raw3 * 256u + 22100u;
  uint16_t hv = (uint16_t)(m / 44200u);
  return hfcNormalize256(hv);
}

FLASHMEM void loadMenuFromEEPROM() {
  if (EEPROM.read(EEPROM_MAGIC_ADDR) != EEPROM_MAGIC) {
    // EEPROM "empty" - try SD backup first, otherwise initialize defaults
    unsigned int restoredPack = 0;
    uint8_t *const restoredBlock = g_eepromRestoredBlock;
    uint8_t *const restoredSp0Block = g_eepromRestoredSp0;
    bool restored = readSettingsBackupFromSD(restoredPack, restoredBlock, SETTINGS_EEPROM_BLOCK_LEN, restoredSp0Block, EEPROM_SP0_STATE_COUNT);

    if (restored) {
      if (restoredPack > 999) {
        restoredPack = 0;
      }
      EEPROM.write(EEPROM_MAGIC_ADDR, EEPROM_MAGIC);
      EEPROM.put(EEPROM_SAMPLEPACK_ADDR, restoredPack);
      for (uint16_t i = 0; i < SETTINGS_EEPROM_BLOCK_LEN; i++) {
        EEPROM.write(EEPROM_DATA_START + i, restoredBlock[i]);
      }
      for (uint8_t i = 0; i < EEPROM_SP0_STATE_COUNT; i++) {
        EEPROM.write(EEPROM_SP0_STATE_ADDR + 1 + i, restoredSp0Block[i]);
      }

      // Keep runtime in sync for the rest of boot (loadSamplePack uses samplePackID)
      extern unsigned int samplePackID;
      samplePackID = restoredPack;
      SMP.pack = restoredPack;
    } else {
      // first run! write magic + defaults
      EEPROM.write(EEPROM_MAGIC_ADDR, EEPROM_MAGIC);
      EEPROM.put(EEPROM_SAMPLEPACK_ADDR, (unsigned int)1);            // samplePackID default (1)
      EEPROM.write(EEPROM_DATA_START + 0,  1);   // recMode default (MIC)
      EEPROM.write(EEPROM_DATA_START + 1,  1);   // clockMode default (INT)
      EEPROM.write(EEPROM_DATA_START + 2,  2);   // transportMode default (SEND)
      EEPROM.write(EEPROM_DATA_START + 3,  1);   // patternMode default (ON)
      EEPROM.write(EEPROM_DATA_START + 4, -1);   // voiceSelect default (OFF)
      EEPROM.write(EEPROM_DATA_START + 5,  1);   // fastRecMode default
      EEPROM.write(EEPROM_DATA_START + 6,  1);   // recChannelClear default
      EEPROM.write(EEPROM_DATA_START + 7,  20);   // previewVol default (0-50 range, middle = 20)
      EEPROM.write(EEPROM_DATA_START + 8, -1);   // flowMode default (OFF)
      EEPROM.write(EEPROM_DATA_START + 9, 10);   // micGain default (10)
      // slot 10: PPQN packed (bit0=on, bit1=polarity-, bits2-4=ppqn idx, bit5=STOP); default OFF / + / 24 / CONT
      EEPROM.write(EEPROM_DATA_START + 10, (uint8_t)(6 << 2));
      EEPROM.write(EEPROM_DATA_START + 30, 12);  // PPQN pulse width ms
      EEPROM.write(EEPROM_DATA_START + 11, 1);   // simpleNotesView default (1 = EASY)
      EEPROM.write(EEPROM_DATA_START + 12, 0);   // loopLength default (0 = OFF)
      EEPROM.write(EEPROM_DATA_START + 13, 1);   // ledMode default (1 = one panel, normal orientation)
      EEPROM.write(EEPROM_DATA_START + 14, 0);   // ctrlMode default (0 = PAGE)
      EEPROM.write(EEPROM_DATA_START + 15, 30);  // lineOutLevelSetting default (30)
      EEPROM.write(EEPROM_DATA_START + 16, 8);   // lineInLevel default (8)
      EEPROM.write(EEPROM_DATA_START + 17, 100);  // GLOB.vol default (100, maps to 1.0 volume, 0-100 range)
      EEPROM.write(EEPROM_DATA_START + 18, 0);   // cursorType default (0 = NORM)
      EEPROM.write(EEPROM_DATA_START + 19, 0);   // showChannelNr default (0 = false, NORM mode)
      EEPROM.write(EEPROM_DATA_START + 20, 0);   // previewTriggerMode default (ON)
      EEPROM.write(EEPROM_DATA_START + 21, 0);   // drawMode default (0 = L+R)
      EEPROM.write(EEPROM_DATA_START + 22, 0);   // colorScheme default (0 = default scheme)
      EEPROM.write(EEPROM_DATA_START + 23, 0);   // stereoChannel default (OFF)
      EEPROM.write(EEPROM_DATA_START + 24, 2);   // midiSendMode default (2 = BOTH)
      EEPROM.write(EEPROM_DATA_START + 25, 0);   // ledStripEnabled default (0 = OFF)
      EEPROM.write(EEPROM_DATA_START + 26, 64);  // ledBrightness default (64, range 3-255)
      EEPROM.write(EEPROM_DATA_START + 27, 1);   // spkrEnabled default (1 = ON)
      EEPROM.write(EEPROM_DATA_START + 28, 1);   // midiNoteReceive default (1 = NOTE/on)
      // Transport delays: slot 29 SEND, slot 31 RCVE (1 byte each, 0-127)
      EEPROM.write(EEPROM_DATA_START + 29, 0);   // transportSendDelayMs default (0)
      EEPROM.write(EEPROM_DATA_START + 31, 0);   // transportRcveDelayMs default (0)
      EEPROM.put(EEPROM_DATA_START + 32, (uint16_t)256);  // codecHfCut default (256)
      EEPROM.write(EEPROM_DATA_START + 33, 4);
      EEPROM.put(EEPROM_DATA_START + 34, (uint16_t)0x0006);  // internal bits 1+2 = user CH1+CH2 (y=2,3)
      EEPROM.write(EEPROM_DATA_START + 36, 0);   // childLockEnabled default (OFF)
      EEPROM.write(EEPROM_DATA_START + 37, 1);   // MIDI pitch clamp default (ON)
      EEPROM.write(EEPROM_DATA_START + 38, 10);  // mixGain14 default (unity)
      EEPROM.write(EEPROM_DATA_START + 39, 10);  // mixGain58 default (unity)
      EEPROM.write(EEPROM_DATA_START + 40, 10);  // mixGainSynth default (unity)
      EEPROM.write(EEPROM_DATA_START + 41, 10);  // mixGainMaster default (unity)
      EEPROM.write(EEPROM_DATA_START + 42, 0);   // voiceMode default (OFF)
      EEPROM.write(EEPROM_DATA_START + 43, 0);   // fireVoice default (OFF)
      EEPROM.write(EEPROM_DATA_START + 44, 8);   // fireLevel default (8 particles)
      EEPROM.write(EEPROM_DATA_START + 45, 1);   // fireSize default (1 cell)
      EEPROM.write(EEPROM_DATA_START + 46, 0);   // fireGravity default (float up)
      EEPROM.write(EEPROM_DATA_START + 47, 8);   // fireColor default (full voice colour)
      EEPROM.write(EEPROM_DATA_START + 48, 0);   // imageMode default (OFF)
      EEPROM.write(EEPROM_DATA_START + 49, 1);   // eyesMode default (1 min)
      EEPROM.write(EEPROM_DATA_START + 51, 1);   // SIDE voice default (CH1)
      EEPROM.write(EEPROM_DATA_START + 52, 0);   // EXT clock source: 0=MIDI, 1=analog PPQN
      EEPROM.write(EEPROM_DATA_START + 53, 2);   // CIN: 4 PPQN, 1 ms hold-off
      for (uint8_t i = 0; i < EEPROM_SP0_STATE_COUNT; i++) {
        EEPROM.write(EEPROM_SP0_STATE_ADDR + 1 + i, 0);
      }

      // Create/refresh SD backup for defaults (debounced)
      markSettingsBackupDirty();
    }
  }

  // now pull them in with validation for corrupted EEPROM values
  recMode       = (int8_t) EEPROM.read(EEPROM_DATA_START + 0);
  if (recMode != 1 && recMode != -1) {
    recMode = 1;  // Default to MIC
    saveSingleModeToEEPROM(0, recMode);
  }
  
  clockMode     = (int8_t) EEPROM.read(EEPROM_DATA_START + 1);
  if (clockMode != 0 && clockMode != 1) {
    clockMode = 1;  // Default to INT (internal clock)
    saveSingleModeToEEPROM(1, clockMode);
  }
  
  transportMode = (int8_t) EEPROM.read(EEPROM_DATA_START + 2);
  if (transportMode != -1 && transportMode != 1 && transportMode != 2) {
    transportMode = 2;  // Default to SEND
    saveSingleModeToEEPROM(2, transportMode);
  }
  
  patternMode   = (int8_t) EEPROM.read(EEPROM_DATA_START + 3);
  if (patternMode != -1 && patternMode != 1 && patternMode != 2 && patternMode != 3) {
    patternMode = 1;  // Default to ON
    saveSingleModeToEEPROM(3, patternMode);
  }
  
  voiceSelect   = (int8_t) EEPROM.read(EEPROM_DATA_START + 4);
  if (voiceSelect != -1 && voiceSelect != 1 && voiceSelect != 2) {
    voiceSelect = -1;  // Default to OFF
    saveSingleModeToEEPROM(4, voiceSelect);
  }
  
  fastRecMode   = (int8_t) EEPROM.read(EEPROM_DATA_START + 5);
  if (fastRecMode < -1 || fastRecMode > 1) {
    fastRecMode = 1;  // Default to ON
    saveSingleModeToEEPROM(5, fastRecMode);
  }
  
  recChannelClear   = (int8_t) EEPROM.read(EEPROM_DATA_START + 6);
  if (recChannelClear < 0 || recChannelClear > 4) {
    recChannelClear = 1;  // Default to ON
    saveSingleModeToEEPROM(6, recChannelClear);
  }
  
  previewVol   = (int8_t) EEPROM.read(EEPROM_DATA_START + 7);
  if (previewVol < 1 || previewVol > 50) {
    previewVol = 20;  // Default to mid
    saveSingleModeToEEPROM(7, previewVol);
  }
  
  flowMode     = (int8_t) EEPROM.read(EEPROM_DATA_START + 8);
  if (flowMode != -1 && flowMode != 1) {
    flowMode = -1;  // Default to OFF
    saveSingleModeToEEPROM(8, flowMode);
  }

  {
    extern bool voiceMode;
    uint8_t voiceModeValue = EEPROM.read(EEPROM_DATA_START + 42);
    voiceMode = (voiceModeValue == 1);
    if (voiceModeValue > 1) EEPROM.write(EEPROM_DATA_START + 42, 0);
  }

  {
    extern uint8_t fireVoice;
    extern uint8_t fireLevel;
    extern uint8_t fireSize;
    extern uint8_t fireGravity;
    extern uint8_t fireColor;
    uint8_t fireValue = EEPROM.read(EEPROM_DATA_START + 43);
    const bool fireOk = (fireValue == 0) || (fireValue == 15) ||
                        (fireValue >= 1 && fireValue <= 8) ||
                        fireValue == 11 || fireValue == 13 || fireValue == 14;
    if (!fireOk) {
      fireValue = 0;
      saveSingleModeToEEPROM(43, 0);
    }
    fireVoice = fireValue;
    uint8_t levelValue = EEPROM.read(EEPROM_DATA_START + 44);
    if (levelValue < 1 || levelValue > 25) {
      levelValue = 8;
      saveSingleModeToEEPROM(44, 8);
    }
    fireLevel = levelValue;
    uint8_t sizeValue = EEPROM.read(EEPROM_DATA_START + 45);
    if (sizeValue < 1 || sizeValue > 4) {
      sizeValue = 1;
      saveSingleModeToEEPROM(45, 1);
    }
    fireSize = sizeValue;
    uint8_t gravValue = EEPROM.read(EEPROM_DATA_START + 46);
    if (gravValue > 8) {
      gravValue = 0;
      saveSingleModeToEEPROM(46, 0);
    }
    fireGravity = gravValue;
    uint8_t colorValue = EEPROM.read(EEPROM_DATA_START + 47);
    if (colorValue > 8) {
      colorValue = 8;
      saveSingleModeToEEPROM(47, 8);
    }
    fireColor = colorValue;
  }

  {
    extern bool imageMode;
    extern bool voiceMode;
    // One-time recovery: early IMG bring-up could leave EEPROM+48 stuck ON, which
    // hides draw-mode base colors and looked like “IMG always on”. Clear once.
    const int IMG_MIGRATE_ADDR = EEPROM_DATA_START + 50;
    if (EEPROM.read(IMG_MIGRATE_ADDR) != 0xA5) {
      EEPROM.write(EEPROM_DATA_START + 48, 0);
      EEPROM.write(IMG_MIGRATE_ADDR, 0xA5);
    }
    uint8_t imageModeValue = EEPROM.read(EEPROM_DATA_START + 48);
    imageMode = (imageModeValue == 1);
    if (imageModeValue > 1) {
      imageMode = false;
      EEPROM.write(EEPROM_DATA_START + 48, 0);
    }
    // VMOD is not allowed with IMG — force VMOD off if both were stored on.
    if (imageMode && voiceMode) {
      voiceMode = false;
      EEPROM.write(EEPROM_DATA_START + 42, 0);
    }
    if (imageMode) {
      extern void enforceImageModeConstraints();
      enforceImageModeConstraints();
    }
  }

  {
    extern uint8_t eyesMode;
    uint8_t eyesValue = EEPROM.read(EEPROM_DATA_START + 49);
    // 0=OFF, 1=1min, 2=5min, 3=15min (legacy BAT/ON values 0–2 still map sanely)
    if (eyesValue > 3) {
      eyesValue = 1;  // default 1 min
      EEPROM.write(EEPROM_DATA_START + 49, 1);
    }
    eyesMode = eyesValue;
  }
  
  micGain     = (int8_t) EEPROM.read(EEPROM_DATA_START + 9);
  if (micGain < 1 || micGain > 63) {
    micGain = 10;  // Default to 10
    saveSingleModeToEEPROM(9, micGain);
  }
  
  simpleNotesView = (int) EEPROM.read(EEPROM_DATA_START + 11);
  if (simpleNotesView < 1 || simpleNotesView > 2) {
    simpleNotesView = 1;  // Default to EASY
    saveSingleModeToEEPROM(11, simpleNotesView);
  }
  
  loopLength = (int) EEPROM.read(EEPROM_DATA_START + 12);
  if (loopLength < 0 || loopLength > 8) {
    loopLength = 0;  // Default to OFF
    saveSingleModeToEEPROM(12, loopLength);
  }
  uint8_t ledMode = EEPROM.read(EEPROM_DATA_START + 13);
  extern bool ledModulesRotated;
  if (ledMode < 1 || ledMode > 4) {
    ledMode = 1;
    saveSingleModeToEEPROM(13, 1);
  }
  ledModules = (ledMode == 1 || ledMode == 3) ? 1 : 2;
  ledModulesRotated = (ledMode >= 3);
  
  ctrlMode = (int8_t) EEPROM.read(EEPROM_DATA_START + 14);
  if (ctrlMode != 0 && ctrlMode != 1) {
    ctrlMode = 0;  // Default to PAGE
    saveSingleModeToEEPROM(14, ctrlMode);
  }
  
  // Load lineInLevel from EEPROM (stored at EEPROM_DATA_START + 16)
  extern unsigned int lineInLevel;
  lineInLevel = (unsigned int)EEPROM.read(EEPROM_DATA_START + 16);
  if (lineInLevel > 15) {
    lineInLevel = 8;  // Default to 8 if invalid
    saveSingleModeToEEPROM(16, lineInLevel);
  }
  
  // Slot 18 used to store BIG cursor. That mode is gone; keep the byte at 0.
  if (EEPROM.read(EEPROM_DATA_START + 18) != 0) {
    saveSingleModeToEEPROM(18, 0);
  }
  
  // Load showChannelNr from EEPROM (stored at EEPROM_DATA_START + 19)
  extern bool showChannelNr;
  showChannelNr = (EEPROM.read(EEPROM_DATA_START + 19) != 0);
  
  // Load drawMode from EEPROM (stored at EEPROM_DATA_START + 21)
  drawMode = (int8_t)EEPROM.read(EEPROM_DATA_START + 21);
  if (drawMode < 0 || drawMode > 1) {
    drawMode = 0;  // Default to 0 (L+R) if invalid
    saveSingleModeToEEPROM(21, drawMode);
  }

  // Load stereoChannel from EEPROM (stored at EEPROM_DATA_START + 23)
  // 0=OFF, 1=M+P, 2=L+R
  // Convert old values for backward compatibility (conversion happens in menu first enter)
  extern int8_t stereoChannel;
  stereoChannel = (int8_t)EEPROM.read(EEPROM_DATA_START + 23);
  if (stereoChannel < 0 || stereoChannel > 8) {
    // Invalid value, default to OFF
    stereoChannel = 0;
    saveSingleModeToEEPROM(23, stereoChannel);
  }
  // Note: Values 1-8 will be converted in menu first enter (old 1->2, old 2-8->2)
  // Apply routing after loading from EEPROM
  extern void applyStereoChannelRouting();
  applyStereoChannelRouting();
  
  // Load midiSendMode from EEPROM (stored at EEPROM_DATA_START + 24)
  // 0=CLCK, 1=NOTE, 2=BOTH
  extern int midiSendMode;
  midiSendMode = (int8_t)EEPROM.read(EEPROM_DATA_START + 24);
  if (midiSendMode < 0 || midiSendMode > 2) {
    // Invalid value, default to BOTH
    midiSendMode = 2;
    saveSingleModeToEEPROM(24, midiSendMode);
  }
  
  // Load ledStripEnabled from EEPROM (stored at EEPROM_DATA_START + 25)
  extern bool getLedStripEnabled();
  extern void setLedStripEnabled(bool enabled);
  uint8_t ledStripValue = EEPROM.read(EEPROM_DATA_START + 25);
  bool ledStripEnabled = (ledStripValue != 0);
  if (ledStripValue > 1) {
    // Invalid value, default to OFF
    ledStripEnabled = false;
    saveSingleModeToEEPROM(25, 0);
  }
  setLedStripEnabled(ledStripEnabled);

  // Load spkrEnabled from EEPROM (stored at EEPROM_DATA_START + 27)
  extern bool getSpkrEnabled();
  extern void setSpkrEnabled(bool enabled);
  uint8_t spkrValue = EEPROM.read(EEPROM_DATA_START + 27);
  bool spkrEnabled = (spkrValue != 0);
  if (spkrValue > 1) {
    // Invalid value, default to ON
    spkrEnabled = true;
    saveSingleModeToEEPROM(27, 1);
  }
  setSpkrEnabled(spkrEnabled);

  // Load childLockEnabled from EEPROM (stored at EEPROM_DATA_START + 36)
  extern bool getChildLockEnabled();
  extern void setChildLockEnabled(bool enabled);
  uint8_t childLockValue = EEPROM.read(EEPROM_DATA_START + 36);
  bool childLockEnabled = (childLockValue != 0);
  if (childLockValue > 1) {
    // Invalid value, default to OFF
    childLockEnabled = false;
    saveSingleModeToEEPROM(36, 0);
  }
  setChildLockEnabled(childLockEnabled);

  // Load midiNoteReceive from EEPROM (slot 28)
  extern bool MIDI_NOTE_RECEIVE;
  uint8_t rcveValue = EEPROM.read(EEPROM_DATA_START + 28);
  if (rcveValue > 1) { rcveValue = 1; saveSingleModeToEEPROM(28, 1); }
  MIDI_NOTE_RECEIVE = (rcveValue != 0);

  // Load MIDI pitch clamp (slot 37). Existing EEPROM is 0xFF here, which
  // migrates to ON so firmware behavior does not change after upgrading.
  extern bool MIDI_NOTE_CLAMP;
  uint8_t clampValue = EEPROM.read(EEPROM_DATA_START + 37);
  if (clampValue > 1) {
    clampValue = 1;
    saveSingleModeToEEPROM(37, 1);
  }
  MIDI_NOTE_CLAMP = (clampValue != 0);

  // VOL→GAIN (slots 38–41). Missing EEPROM / virgin 0xFF / >20 → 1.0× (10).
  // All-zero (pre-GAIN firmware or zero-padded backup) also → 1.0× for every bus.
  {
    extern uint8_t mixGain14;
    extern uint8_t mixGain58;
    extern uint8_t mixGainSynth;
    extern uint8_t mixGainMaster;
    uint8_t g14 = EEPROM.read(EEPROM_DATA_START + EEPROM_MIX_GAIN_14);
    uint8_t g58 = EEPROM.read(EEPROM_DATA_START + EEPROM_MIX_GAIN_58);
    uint8_t gSyn = EEPROM.read(EEPROM_DATA_START + EEPROM_MIX_GAIN_SYN);
    uint8_t gAll = EEPROM.read(EEPROM_DATA_START + EEPROM_MIX_GAIN_ALL);
    bool migrated = false;
    const bool blank = ((g14 | g58 | gSyn | gAll) == 0);
    auto fixGain = [&](uint8_t g) -> uint8_t {
      if (blank || g > MIX_GAIN_MAX) return (uint8_t)MIX_GAIN_UNITY;
      return g;
    };
    uint8_t n14 = fixGain(g14);
    uint8_t n58 = fixGain(g58);
    uint8_t nSyn = fixGain(gSyn);
    uint8_t nAll = fixGain(gAll);
    if (n14 != g14) { EEPROM.write(EEPROM_DATA_START + EEPROM_MIX_GAIN_14, n14); migrated = true; }
    if (n58 != g58) { EEPROM.write(EEPROM_DATA_START + EEPROM_MIX_GAIN_58, n58); migrated = true; }
    if (nSyn != gSyn) { EEPROM.write(EEPROM_DATA_START + EEPROM_MIX_GAIN_SYN, nSyn); migrated = true; }
    if (nAll != gAll) { EEPROM.write(EEPROM_DATA_START + EEPROM_MIX_GAIN_ALL, nAll); migrated = true; }
    mixGain14 = n14;
    mixGain58 = n58;
    mixGainSynth = nSyn;
    mixGainMaster = nAll;
    if (migrated) markSettingsBackupDirty();
  }

  // Load transport delay settings (slot 29 SNC1, slot 31 SNC2, int8_t -127..+127, EEPROM stores raw byte)
  extern int8_t transportSendDelayMs;
  extern int8_t transportRcveDelayMs;
  uint8_t raw29 = EEPROM.read(EEPROM_DATA_START + 29);
  uint8_t raw31 = EEPROM.read(EEPROM_DATA_START + 31);
  // Migration: old layout had slot 31=0xFF, 29=SEND, 30=RCVE (unsigned 0-127)
  if (raw31 == 0xFF) {
    uint8_t raw30 = EEPROM.read(EEPROM_DATA_START + 30);
    int8_t v29 = (raw29 <= 127) ? (int8_t)raw29 : 17;
    int8_t v30 = (raw30 <= 127) ? (int8_t)raw30 : 17;
    transportSendDelayMs = (int8_t)constrain((int)v29, -127, 127);
    transportRcveDelayMs = (int8_t)constrain((int)v30, -127, 127);
    EEPROM.write(EEPROM_DATA_START + 29, (uint8_t)transportSendDelayMs);
    EEPROM.write(EEPROM_DATA_START + 31, (uint8_t)transportRcveDelayMs);
    EEPROM.write(EEPROM_DATA_START + 30, 12);  // slot 30 reused as PPQN pulse width ms
  } else {
    transportSendDelayMs = (int8_t)constrain((int)(int8_t)raw29, -127, 127);
    transportRcveDelayMs = (int8_t)constrain((int)(int8_t)raw31, -127, 127);
  }

  // Load PPQN pulse settings after delay migration so slot 30 is pulse width, not leftover RCVE
  {
    extern void loadPulseClockFromEEPROM();
    loadPulseClockFromEEPROM();
    extern void loadSidechainFromEEPROM();
    loadSidechainFromEEPROM();
    extern void loadAnalogExtClockFromEEPROM();
    loadAnalogExtClockFromEEPROM();
  }

  {
    extern uint16_t codecHfCut;
    uint8_t eqFmt = EEPROM.read(EEPROM_DATA_START + 33);
    uint16_t raw = 0;
    EEPROM.get(EEPROM_DATA_START + 32, raw);
    uint16_t cut = 110;

    if (eqFmt == 4) {
      cut = raw;
      if (cut > 256u) cut = 256u;
      cut = hfcNormalize256(cut);
    } else if (eqFmt == 3) {
      cut = hfcMigrate44200To256(raw);
      EEPROM.put(EEPROM_DATA_START + 32, cut);
      EEPROM.write(EEPROM_DATA_START + 33, 4);
      markSettingsBackupDirty();
    } else if (eqFmt == 2) {
      uint16_t r = raw;
      if (r > 500u) r = 500u;
      r = (uint16_t)((r / 10u) * 10u);
      uint32_t m = (uint32_t)r * 256u + 250u;
      uint16_t h = (uint16_t)(m / 500u);
      cut = hfcNormalize256(h);
      EEPROM.put(EEPROM_DATA_START + 32, cut);
      EEPROM.write(EEPROM_DATA_START + 33, 4);
      markSettingsBackupDirty();
    } else if (eqFmt == 1) {
      uint16_t oldv = raw;
      if (oldv > 22000u) oldv = 22000u;
      oldv = (uint16_t)((oldv / 100u) * 100u);
      cut = hfcMigrate22000To256(oldv);
      EEPROM.put(EEPROM_DATA_START + 32, cut);
      EEPROM.write(EEPROM_DATA_START + 33, 4);
      markSettingsBackupDirty();
    } else {
      uint16_t oldv;
      if (raw >= 6000u && raw <= 20000u && (raw % 100u) == 0) {
        uint32_t delta = raw - 6000u;
        oldv = (uint16_t)(((14000u - delta) * 22000u + 7000u) / 14000u);
      } else if (raw > 0u && raw <= 22000u) {
        oldv = raw;
      } else {
        oldv = 10000;
      }
      oldv = (uint16_t)((oldv / 100u) * 100u);
      if (oldv > 22000u) oldv = 22000u;
      cut = hfcMigrate22000To256(oldv);
      EEPROM.put(EEPROM_DATA_START + 32, cut);
      EEPROM.write(EEPROM_DATA_START + 33, 4);
      markSettingsBackupDirty();
    }
    codecHfCut = cut;
  }

  {
    uint16_t fm = 0;
    EEPROM.get(EEPROM_DATA_START + 34, fm);
    drawRFullMuteCustomUnmuteMask = fm;
  }

  if (previewVol < 0 || previewVol > 50) {
    previewVol = 20;
    saveSingleModeToEEPROM(7, previewVol);
  }
  
  // Safety: Ensure monitoring is OFF on startup to prevent feedback
  mixer_end.gain(3, 0.0);
  
  // Update maxX based on loaded ledModules value
  extern unsigned int maxX;
  maxX = MATRIX_WIDTH * ledModules;
  
  if (recChannelClear < 0 || recChannelClear > 4) {
    recChannelClear = 1;  // Default to ON if invalid
    saveSingleModeToEEPROM(6, recChannelClear);
  }
  
  // Ensure flowMode is valid (-1 or 1)
  if (flowMode != -1 && flowMode != 1) {
    flowMode = -1;  // Default to OFF if invalid value
    saveSingleModeToEEPROM(8, flowMode);
  }
  
  // Ensure simpleNotesView is valid (1-2)
  if (simpleNotesView < 1 || simpleNotesView > 2) {
    simpleNotesView = 1;  // Default to EASY if invalid value
    saveSingleModeToEEPROM(11, simpleNotesView);
  }
  
  if (transportMode != -1 && transportMode != 1 && transportMode != 2) {
    transportMode = -1;  // Default to OFF if invalid value
    saveSingleModeToEEPROM(2, transportMode);
  }

  // Ensure loopLength is valid (0-8)
  if (loopLength < 0 || loopLength > 8) {
    loopLength = 0;  // Default to OFF if invalid value
    saveSingleModeToEEPROM(12, loopLength);
  }
  
  // Ensure voiceSelect is valid (-1, 1, or 2)
  if (voiceSelect != -1 && voiceSelect != 1 && voiceSelect != 2) {
    voiceSelect = 1;  // Default to MIDI if invalid value
    saveSingleModeToEEPROM(4, voiceSelect);
  }
  
  // Ensure patternMode is valid (-1, 1, or 2)
  if (patternMode != -1 && patternMode != 1 && patternMode != 2 && patternMode != 3) {
    patternMode = -1;  // Default to OFF if invalid value
    saveSingleModeToEEPROM(3, patternMode);
  }
  
  // Ensure led mode is valid (1,2,3,4 => 1,2,1B,2B)
  if (ledMode < 1 || ledMode > 4) {
    ledMode = 1;     // Default to 1 if invalid value
    ledModules = 1;
    ledModulesRotated = false;
    saveSingleModeToEEPROM(13, 1);
  }

  if (ctrlMode != 0 && ctrlMode != 1) {
    ctrlMode = 0;
    saveSingleModeToEEPROM(14, ctrlMode);
  }


  // Set global flags
  SMP_PATTERN_MODE       = (patternMode   == 1 || patternMode == 2 || patternMode == 3);  // ON, SONG, or NEXT mode
  SMP_FLOW_MODE          = (flowMode      == 1);
  MIDI_VOICE_SELECT      = (voiceSelect   == 1 || voiceSelect == 2);  // MIDI or KEYS mode
  MIDI_TRANSPORT_RECEIVE = (transportMode == 1);
  MIDI_TRANSPORT_SEND = (transportMode == 2);
  SMP_FAST_REC           = fastRecMode;
  SMP_REC_CHANNEL_CLEAR  = (recChannelClear == 1);  // Only true for ON mode
  
  // Set song mode active flag
  extern bool songModeActive;
  songModeActive = (patternMode == 2);
  
  // Set audio input based on recMode
  recInput = (recMode == 1) ? AUDIO_INPUT_MIC : AUDIO_INPUT_LINEIN;
  
  // Set MIDI clock send based on clockMode
  MIDI_CLOCK_SEND = (clockMode == 1);
  
  // Set MIDI send flags based on midiSendMode (0=CLCK, 1=NOTE, 2=BOTH)
  // Note: MIDI_CLOCK_SEND is already set above, but we need to respect midiSendMode
  extern int midiSendMode;
  extern bool MIDI_NOTE_SEND;
  if (midiSendMode == 0) {
    // CLCK only: keep MIDI_CLOCK_SEND as set by clockMode, disable notes
    MIDI_NOTE_SEND = false;
  } else if (midiSendMode == 1) {
    // NOTE only: disable clock, enable notes
    MIDI_CLOCK_SEND = false;
    MIDI_NOTE_SEND = true;
  } else {
    // BOTH: keep MIDI_CLOCK_SEND as set by clockMode, enable notes
    MIDI_NOTE_SEND = true;
  }
  
  // Codec I2C is applied later by initSoundChip() / applyAudioSettingsFromGlobals().
  // Writing the SGTL5000 here runs before enable() on the boot path and wedges
  // the bus on the first start after a flash.

  // Note: These draw functions are for menu display, not startup initialization.
  // They should only be called when actually displaying the menu, not during setup().
  // The initialization logic (loading values from EEPROM) is complete above.
  // Drawing during startup causes brief text flashes (e.g., "MIC" before "KIT:").
  // drawRecMode();
  // drawClockMode();
  // drawMidiTransport();
  // drawPatternMode();
  // drawFlowMode();
  // drawMidiVoiceSelect();
  // drawFastRecMode();
  // drawRecChannelClear();
}

// Apply all audio-related global variables to hardware
FLASHMEM void applyAudioSettingsFromGlobals() {
  // GLOB, lineOutLevelSetting, previewVol, micGain, and lineInLevel are already in scope as globals
  extern struct GlobalVars GLOB;
  extern uint8_t lineOutLevelSetting;
  extern unsigned int previewVol;
  extern unsigned int micGain;
  extern unsigned int lineInLevel;
  
  // Apply main volume (headphone output)
  // Handle both legacy (0-10) and new (0-100) ranges
  float vol;
  if (GLOB.vol <= 10) {
    // Legacy value (0-10): convert to 0.0-1.0
    vol = GLOB.vol / 10.0f;
  } else {
    // New value (0-100): convert to 0.0-1.0
    vol = GLOB.vol / 100.0f;
  }
  vol = constrain(vol, 0.0f, 1.0f);
  sgtl5000_1.volume(vol);
  
  // Apply line output level
  sgtl5000_1.lineOutLevel(lineOutLevelSetting);
  
  // Apply mic gain only when MIC is selected; otherwise force 0 to keep MIC path off.
  extern unsigned int recInput;
  if (recInput == AUDIO_INPUT_MIC) {
    sgtl5000_1.micGain(micGain);
  } else {
    sgtl5000_1.micGain(0);
  }
  
  // Apply line input level
  sgtl5000_1.lineInLevel(lineInLevel);

  extern void applySgtl5000AdcHighPass();
  applySgtl5000AdcHighPass();
  extern void applySgtl5000CodecOutputPath();
  applySgtl5000CodecOutputPath();
  
  // Apply preview volume
  updatePreviewVolume();

  extern void applyMixBusGains();
  applyMixBusGains();
}

// call this after you change *any* one of the six modes in switchMenu():
FLASHMEM void saveSingleModeToEEPROM(int index, int8_t value) {
  extern bool isNowPlaying;
  if (index < 0 || index >= (int)SETTINGS_EEPROM_BLOCK_LEN) return;
  if (isNowPlaying) {
    pendingEepromSet(index, (uint8_t)value);
    markSettingsBackupDirty();
    return;
  }
  EEPROM.write(EEPROM_DATA_START + index, (uint8_t)value);
  markSettingsBackupDirty();
}

// Live-apply mix gain; defer flash EEPROM while playing (avoids mid-playback stalls).
static inline void saveMixGainToEEPROM(int eepromIndex, uint8_t value, uint8_t pendingBit) {
  extern bool isNowPlaying;
  if (isNowPlaying) {
    g_pendingMixGainMask |= pendingBit;
    return;
  }
  saveSingleModeToEEPROM(eepromIndex, (int8_t)value);
}

static void saveTransportDelayToEEPROM(int slotBase, int8_t value) {
  saveSingleModeToEEPROM(slotBase, value);
}

// uint16 settings (HFC cut, draw mute mask). Format byte written separately when needed.
FLASHMEM static void saveSettingsU16ToEEPROM(int index, uint16_t value) {
  extern bool isNowPlaying;
  if (index < 0 || index + 1 >= (int)SETTINGS_EEPROM_BLOCK_LEN) return;
  if (isNowPlaying) {
    pendingEepromSet(index, (uint8_t)(value & 0xFF));
    pendingEepromSet(index + 1, (uint8_t)((value >> 8) & 0xFF));
    markSettingsBackupDirty();
    return;
  }
  EEPROM.put(EEPROM_DATA_START + index, value);
  markSettingsBackupDirty();
}


// Save samplepack 0 state to EEPROM (which voices are using sp0)
FLASHMEM void saveSp0StateToEEPROM() {
  extern bool isNowPlaying;
  // Mid-playback flash writes stall the same way mix-gain did — defer until stopped.
  if (isNowPlaying) {
    g_pendingSp0Eeprom = true;
    markSettingsBackupDirty();
    return;
  }
  // Use addresses 200-208 for sp0 state (8 voices = 8 bytes)
  for (int i = 1; i < maxFiles; i++) {
    uint8_t value = SMP.sp0Active[i] ? 1 : 0;
    EEPROM.write(EEPROM_SP0_STATE_ADDR + i, value);
  }
  markSettingsBackupDirty();
}

// Load samplepack 0 state from EEPROM
FLASHMEM void loadSp0StateFromEEPROM() {
  for (int i = 1; i < maxFiles; i++) {
    uint8_t stored = EEPROM.read(EEPROM_SP0_STATE_ADDR + i);
    SMP.sp0Active[i] = (stored == 1);
  }
}

FLASHMEM void showMenu() {
  // Only redraw the menu UI when the page/setting changes (or a value changed).
  // This avoids unnecessary clears/shows each loop.

  // Handle page navigation with encoder 4
  static int lastPagePosition = -1;
  static bool menuFirstEnter = true;
  
  // Reset tracking when returning from submenu (currentMenuPage doesn't match mode pos)
  if (currentMenuPage != currentMode->pos[3] && lastPagePosition != currentMenuPage) {
    lastPagePosition = -1;
    menuFirstEnter = true;
    currentMode->pos[3] = currentMenuPage;  // Sync mode position with current page
  }
  
  if (menuFirstEnter) {
    Encoder[3].writeCounter((int32_t)currentMenuPage);
    lastPagePosition = currentMenuPage;
    menuFirstEnter = false;
  }
  
  ensureEnc3Range(0, (int)(MENU_PAGES_COUNT - 1));
  
  if (currentMode->pos[3] != lastPagePosition) {
    currentMenuPage = currentMode->pos[3];
    if (currentMenuPage >= MENU_PAGES_COUNT) currentMenuPage = MENU_PAGES_COUNT - 1;
    if (currentMenuPage < 0) currentMenuPage = 0;
    lastPagePosition = currentMenuPage;
  }

  // Current page/setting
  const int pageIndex = currentMenuPage;
  MenuPage* currentPageInfo = &menuPages[pageIndex];
  const int mainSetting = currentPageInfo->mainSetting;

  static int lastRenderedPageIndex = -1;
  static int lastRenderedSetting = -1;
  const bool fullRedraw = takeMenuForceFullRedraw() || (pageIndex != lastRenderedPageIndex) || (mainSetting != lastRenderedSetting);

  if (fullRedraw) {
    FastLEDclear();
    // New indicator system: menu: | | | L[G]
    drawIndicator('L', 'G', 4);  // Encoder 4: menu navigation

    // Page indicator line at y=maxY
    int startX = (int)maxX - MENU_PAGES_COUNT + 1;
    if (startX < 1) startX = 1;
    for (int i = 0; i < MENU_PAGES_COUNT; i++) {
      CRGB indicatorColor = (i == pageIndex) ? UI_RED : UI_BLUE;
      light(startX + i, maxY, indicatorColor);
    }

    // Encoder RGB defaults (only when page changes)
    if (mainSetting == 15) {
      // AI page: multiple indicators - L[G], L[Y], L[W], L[X]
      CRGB greenColor = getIndicatorColor('G');
      CRGB yellowColor = getIndicatorColor('Y');
      CRGB whiteColor = getIndicatorColor('W');
      CRGB blueColor = getIndicatorColor('X');
      Encoder[0].writeRGBCode(greenColor.r << 16 | greenColor.g << 8 | greenColor.b);
      Encoder[1].writeRGBCode(yellowColor.r << 16 | yellowColor.g << 8 | yellowColor.b);
      Encoder[2].writeRGBCode(whiteColor.r << 16 | whiteColor.g << 8 | whiteColor.b);
      Encoder[3].writeRGBCode(blueColor.r << 16 | blueColor.g << 8 | blueColor.b);
    } else {
      // Keep encoder 4 aligned with the visible menu-navigation indicator color.
      CRGB menuNavColor = getIndicatorColor('G');
      Encoder[0].writeRGBCode(0x000000);
      Encoder[1].writeRGBCode(0x000000);
      Encoder[2].writeRGBCode(0x000000);
      Encoder[3].writeRGBCode(menuNavColor.r << 16 | menuNavColor.g << 8 | menuNavColor.b);
    }

    drawMainSettingStatus(mainSetting);
    if (currentPageInfo->hasAdditionalFeatures) {
      drawAdditionalFeatures(mainSetting);
    }

    lastRenderedPageIndex = pageIndex;
    lastRenderedSetting = mainSetting;
  }

  // Handle encoder changes for pages with adjustable values.
  const bool didRedraw = handleAdditionalFeatureControls(mainSetting);
  if (fullRedraw || didRedraw) {
    // FastLED.setBrightness(ledBrightness);
    FastLEDshow();
  }
}

FLASHMEM void showLookMenu() {
  static uint32_t lastPosHash = 0;
  // Redraw only when page/setting changes (or a value changed).
  int pageIndex = currentLookPage;
  MenuPage* currentPageInfo = &lookPages[pageIndex];
  int mainSetting = currentPageInfo->mainSetting;

  static int lastRenderedLookPage = -1;
  static int lastRenderedLookSetting = -1;
  const bool fullRedraw = takeMenuForceFullRedraw() || (pageIndex != lastRenderedLookPage) || (mainSetting != lastRenderedLookSetting);

  if (fullRedraw) {
    FastLEDclear();

  // Submenu indicator (encoder 4) should always match submenu text color.
  drawLargeIndicatorCustom(currentMenuParentTextColor(), 4);

  // Get current page info
  // (pageIndex/currentPageInfo already computed above)
  
  // Draw page indicator as a line at y=maxY (right-aligned)
  // Match the parent menu color (SETTINGS).
  const CRGB parent = currentMenuParentTextColor();
  const CRGB parentDim = dimIconColorFromText(parent);
  int startX = (int)maxX - LOOK_PAGES_COUNT + 1;
  if (startX < 1) startX = 1;
  for (int i = 0; i < LOOK_PAGES_COUNT; i++) {
    CRGB indicatorColor = (i == pageIndex) ? parent : parentDim;
    light(startX + i, maxY, indicatorColor);
  }

  // Handle the main setting for this page
  // (mainSetting already computed above)
  
  // SETTINGS submenu: encoder 2 = value on toggle pages
  CRGB indicatorColor = currentMenuParentTextColor();
  const bool playValuePage = (mainSetting == 9 || mainSetting == 10 || mainSetting == 17 ||
      mainSetting == 18 || mainSetting == 23 || mainSetting == 24 || mainSetting == 25 ||
      mainSetting == 32 || mainSetting == 33 || mainSetting == 38 || mainSetting == 47 ||
      mainSetting == 54);
  Encoder[0].writeRGBCode(0x000000);
  Encoder[1].writeRGBCode(0x000000);
  Encoder[2].writeRGBCode(playValuePage ? (indicatorColor.r << 16 | indicatorColor.g << 8 | indicatorColor.b) : 0x000000);
  Encoder[3].writeRGBCode(indicatorColor.r << 16 | indicatorColor.g << 8 | indicatorColor.b);

  // Draw the main setting status
  drawMainSettingStatus(mainSetting);
  
  // Draw additional features if this page has them
  if (currentPageInfo->hasAdditionalFeatures) {
    drawAdditionalFeatures(mainSetting);
  }

  // FastLED.setBrightness(ledBrightness);
  FastLEDshow();

  lastRenderedLookPage = pageIndex;
  lastRenderedLookSetting = mainSetting;
  }

  // Handle page navigation with encoder 3
  static int lastLookPagePosition = -1;
  static bool lookMenuFirstEnter = true;
  
  // Reset tracking when entering submenu (currentLookPage is 0 and mode pos doesn't match)
  if (currentLookPage == 0 && currentMode->pos[3] != 0 && lastLookPagePosition != 0) {
    lastLookPagePosition = -1;
    lookMenuFirstEnter = true;
  }
  
  if (lookMenuFirstEnter) {
    Encoder[3].writeCounter((int32_t)currentLookPage);
    lastLookPagePosition = currentLookPage;
    lookMenuFirstEnter = false;
  }
  
  ensureEnc3Range(0, (int)(LOOK_PAGES_COUNT - 1));
  
  if (currentMode->pos[3] != lastLookPagePosition) {
    currentLookPage = currentMode->pos[3];
    if (currentLookPage >= LOOK_PAGES_COUNT) currentLookPage = LOOK_PAGES_COUNT - 1;
    if (currentLookPage < 0) currentLookPage = 0;
    lastLookPagePosition = currentLookPage;
  }
  
  // Handle encoder changes for pages with adjustable values.
  const bool didRedraw = handleAdditionalFeatureControls(mainSetting);
  if (!fullRedraw && didRedraw) {
    // FastLED.setBrightness(ledBrightness);
    FastLEDshow();
  }

  // Mark render dirty on any encoder movement while in submenu.
  // Skip if controls already redrew this frame (avoids re-I2C RGB on every tick).
  uint32_t h = hashEncoderPositions(currentMode);
  if (h != lastPosHash) {
    if (!didRedraw) menuRequestFullRedraw();
    lastPosHash = h;
  }
}

FLASHMEM void showRecsMenu() {
  static uint32_t lastPosHash = 0;
  // Redraw only when page/setting changes (or a value changed).
  int pageIndex = currentRecsPage;
  MenuPage* currentPageInfo = &recsPages[pageIndex];
  int mainSetting = currentPageInfo->mainSetting;

  static int lastRenderedRecsPage = -1;
  static int lastRenderedRecsSetting = -1;
  const bool fullRedraw = takeMenuForceFullRedraw() || (pageIndex != lastRenderedRecsPage) || (mainSetting != lastRenderedRecsSetting);

  if (fullRedraw) {
    FastLEDclear();

  // Submenu indicator (encoder 4) should always match submenu text color.
  drawLargeIndicatorCustom(currentMenuParentTextColor(), 4);

  // Get current page info
  // (pageIndex/currentPageInfo already computed above)
  
  // Show header only on MIC/LINE toggle page
  if (currentPageInfo->mainSetting == 4) {
    drawText("INPT", 2, 10, menuTextColorFromCol(7));
  }
  
  // Draw page indicator as a line at y=maxY (right-aligned)
  // Match the parent menu color (RECS).
  const CRGB parent = currentMenuParentTextColor();
  const CRGB parentDim = dimIconColorFromText(parent);
  int startX = (int)maxX - RECS_PAGES_COUNT + 1;
  if (startX < 1) startX = 1;
  for (int i = 0; i < RECS_PAGES_COUNT; i++) {
    CRGB indicatorColor = (i == pageIndex) ? parent : parentDim;
    light(startX + i, maxY, indicatorColor);
  }

  // Handle the main setting for this page
  // (mainSetting already computed above)
  
  // Set encoder colors based on main setting
  if (mainSetting == 11 || mainSetting == 4 || mainSetting == 12) {
    // TRIG, INPT, CLR: encoder 2 = value, encoder 3 = page nav
    CRGB indicatorColor = currentMenuParentTextColor();
    Encoder[0].writeRGBCode(0x000000);
    Encoder[1].writeRGBCode(0x000000);
    Encoder[2].writeRGBCode(indicatorColor.r << 16 | indicatorColor.g << 8 | indicatorColor.b);
    Encoder[3].writeRGBCode(indicatorColor.r << 16 | indicatorColor.g << 8 | indicatorColor.b);
  } else {
    // Default: encoder 4 ring matches submenu text color
    CRGB indicatorColor = currentMenuParentTextColor();
    Encoder[0].writeRGBCode(0x000000); // Black (no indicator)
    Encoder[1].writeRGBCode(0x000000); // Black (no indicator)
    Encoder[2].writeRGBCode(0x000000); // Black (no indicator)
    Encoder[3].writeRGBCode(indicatorColor.r << 16 | indicatorColor.g << 8 | indicatorColor.b);
  }

  // Draw the main setting status
  drawMainSettingStatus(mainSetting);
  
  // Draw additional features if this page has them
  if (currentPageInfo->hasAdditionalFeatures) {
    drawAdditionalFeatures(mainSetting);
  }

  // FastLED.setBrightness(ledBrightness);
  FastLEDshow();

  lastRenderedRecsPage = pageIndex;
  lastRenderedRecsSetting = mainSetting;
  }

  // Handle page navigation with encoder 3
  static int lastRecsPagePosition = -1;
  static bool recsMenuFirstEnter = true;
  
  // Reset tracking when entering submenu (currentRecsPage is 0 and mode pos doesn't match)
  if (currentRecsPage == 0 && currentMode->pos[3] != 0 && lastRecsPagePosition != 0) {
    lastRecsPagePosition = -1;
    recsMenuFirstEnter = true;
  }
  
  if (recsMenuFirstEnter) {
    Encoder[3].writeCounter((int32_t)currentRecsPage);
    lastRecsPagePosition = currentRecsPage;
    recsMenuFirstEnter = false;
  }
  
  ensureEnc3Range(0, (int)(RECS_PAGES_COUNT - 1));
  
  if (currentMode->pos[3] != lastRecsPagePosition) {
    currentRecsPage = currentMode->pos[3];
    if (currentRecsPage >= RECS_PAGES_COUNT) currentRecsPage = RECS_PAGES_COUNT - 1;
    if (currentRecsPage < 0) currentRecsPage = 0;
    lastRecsPagePosition = currentRecsPage;
  }
  
  // Handle encoder changes for pages with adjustable values.
  const bool didRedraw = handleAdditionalFeatureControls(mainSetting);
  if (!fullRedraw && didRedraw) {
    // FastLED.setBrightness(ledBrightness);
    FastLEDshow();
  }

  // Mark render dirty on any encoder movement while in submenu.
  // Skip if controls already redrew this frame (avoids re-I2C RGB on every tick).
  uint32_t h = hashEncoderPositions(currentMode);
  if (h != lastPosHash) {
    if (!didRedraw) menuRequestFullRedraw();
    lastPosHash = h;
  }
}

FLASHMEM void showMidiMenu() {
  static uint32_t lastPosHash = 0;
  // Redraw only when page/setting changes (or a value changed).
  int pageIndex = currentMidiPage;
  MenuPage* currentPageInfo = &midiPages[pageIndex];
  int mainSetting = currentPageInfo->mainSetting;

  static int lastRenderedMidiPage = -1;
  static int lastRenderedMidiSetting = -1;
  const bool fullRedraw = takeMenuForceFullRedraw() || (pageIndex != lastRenderedMidiPage) || (mainSetting != lastRenderedMidiSetting);

  if (fullRedraw) {
    FastLEDclear();

  // Submenu page-nav indicator (encoder 4)
  drawLargeIndicatorCustom(currentMenuParentTextColor(), 4);

  // Get current page info
  // (pageIndex/currentPageInfo already computed above)
  
  // Draw page indicator as a line at y=maxY (right-aligned)
  // Match the parent menu color (MIDI).
  const CRGB parent = currentMenuParentTextColor();
  const CRGB parentDim = dimIconColorFromText(parent);
  int startX = (int)maxX - MIDI_PAGES_COUNT + 1;
  if (startX < 1) startX = 1;
  for (int i = 0; i < MIDI_PAGES_COUNT; i++) {
    CRGB indicatorColor = (i == pageIndex) ? parent : parentDim;
    light(startX + i, maxY, indicatorColor);
  }

  // Handle the main setting for this page
  // (mainSetting already computed above)
  
  // MIDI: encoder 2 = value on CH/TRAN/SEND/RCVE/CLMP/SIDE; enc1+2 = SYNC;
  // PPQN: enc1=width, enc2=STOP/CONT, enc3=OFF/rate (click=POL); enc4 = page nav
  CRGB indicatorColor = currentMenuParentTextColor();
  const bool midiValuePage = (mainSetting == 7 || mainSetting == 8 || mainSetting == 13 || mainSetting == 44 || mainSetting == 51 || mainSetting == 45 || mainSetting == 50 || mainSetting == 58 || mainSetting == 59);
  Encoder[0].writeRGBCode(0x000000);
  if (mainSetting == 50) {
    extern bool getPulseClockPolarityPositive();
    extern bool getPulseClockStopWithPlay();
    const bool polPos = getPulseClockPolarityPositive();
    const bool stopPlay = getPulseClockStopWithPlay();
    Encoder[0].writeRGBCode(0xFFFFFF);
    Encoder[1].writeRGBCode(stopPlay ? 0xFF0000 : 0x00FF00);
    Encoder[2].writeRGBCode(polPos ? 0x00FF00 : 0xFF0000);
    Encoder[3].writeRGBCode(indicatorColor.r << 16 | indicatorColor.g << 8 | indicatorColor.b);
  } else if (mainSetting == 59) {
    Encoder[0].writeRGBCode(0xFFFFFF);
    Encoder[1].writeRGBCode(0x000000);
    Encoder[2].writeRGBCode(0xFFFFFF);
    Encoder[3].writeRGBCode(indicatorColor.r << 16 | indicatorColor.g << 8 | indicatorColor.b);
  } else {
    Encoder[1].writeRGBCode(mainSetting == 45 ? (indicatorColor.r << 16 | indicatorColor.g << 8 | indicatorColor.b) : 0x000000);
    Encoder[2].writeRGBCode(midiValuePage ? (indicatorColor.r << 16 | indicatorColor.g << 8 | indicatorColor.b) : 0x000000);
    Encoder[3].writeRGBCode(indicatorColor.r << 16 | indicatorColor.g << 8 | indicatorColor.b);
  }

  // Draw the main setting status
  drawMainSettingStatus(mainSetting);
  
  // Draw additional features if this page has them
  if (currentPageInfo->hasAdditionalFeatures) {
    drawAdditionalFeatures(mainSetting);
  }

  // FastLED.setBrightness(ledBrightness);
  FastLEDshow();

  lastRenderedMidiPage = pageIndex;
  lastRenderedMidiSetting = mainSetting;
  }

  // Handle page navigation with encoder 4
  static int lastMidiPagePosition = -1;
  static bool midiMenuFirstEnter = true;
  
  // Reset tracking when entering submenu (currentMidiPage is 0 and mode pos doesn't match)
  if (currentMidiPage == 0 && currentMode->pos[3] != 0 && lastMidiPagePosition != 0) {
    lastMidiPagePosition = -1;
    midiMenuFirstEnter = true;
  }
  
  if (midiMenuFirstEnter) {
    Encoder[3].writeCounter((int32_t)currentMidiPage);
    lastMidiPagePosition = currentMidiPage;
    midiMenuFirstEnter = false;
  }
  
  ensureEnc3Range(0, (int)(MIDI_PAGES_COUNT - 1));
  
  if (currentMode->pos[3] != lastMidiPagePosition) {
    currentMidiPage = currentMode->pos[3];
    if (currentMidiPage >= MIDI_PAGES_COUNT) currentMidiPage = MIDI_PAGES_COUNT - 1;
    if (currentMidiPage < 0) currentMidiPage = 0;
    lastMidiPagePosition = currentMidiPage;
  }
  
  // Handle encoder changes for pages with adjustable values.
  const bool didRedraw = handleAdditionalFeatureControls(mainSetting);
  if (!fullRedraw && didRedraw) {
    // FastLED.setBrightness(ledBrightness);
    FastLEDshow();
  }

  // Mark render dirty on any encoder movement while in submenu.
  // Skip if controls already redrew this frame (avoids re-I2C RGB on every tick).
  uint32_t h = hashEncoderPositions(currentMode);
  if (h != lastPosHash) {
    if (!didRedraw) menuRequestFullRedraw();
    lastPosHash = h;
  }
}

FLASHMEM void showVolMenu() {
  static uint32_t lastPosHash = 0;
  // Redraw only when page/setting changes (or a value changed).
  int pageIndex = currentVolPage;
  MenuPage* currentPageInfo = &volPages[pageIndex];
  int mainSetting = currentPageInfo->mainSetting;

  static int lastRenderedVolPage = -1;
  static int lastRenderedVolSetting = -1;
  const bool fullRedraw = takeMenuForceFullRedraw() || (pageIndex != lastRenderedVolPage) || (mainSetting != lastRenderedVolSetting);

  if (fullRedraw) {
    FastLEDclear();

  // VOL submenu: page-nav indicator should always match VOL text color (e.g. "MAIN")
  drawLargeIndicatorCustom(currentMenuParentTextColor(), 4);

  // Get current page info
  // (pageIndex/currentPageInfo already computed above)
  
  // Draw page indicator as a line at y=maxY (right-aligned)
  // Match the parent menu color (VOL).
  const CRGB parent = currentMenuParentTextColor();
  const CRGB parentDim = dimIconColorFromText(parent);
  int startX = (int)maxX - VOL_PAGES_COUNT + 1;
  if (startX < 1) startX = 1;
  for (int i = 0; i < VOL_PAGES_COUNT; i++) {
    CRGB indicatorColor = (i == pageIndex) ? parent : parentDim;
    light(startX + i, maxY, indicatorColor);
  }

  // Handle the main setting for this page
  // (mainSetting already computed above)
  
  // VOL: encoder 3 = value on SPKR/HFC; GAIN uses enc1–3
  CRGB indicatorColor = currentMenuParentTextColor();
  const bool volGainPage = (mainSetting == 53);
  const bool volValuePage = (mainSetting == 43 || mainSetting == 46);
  Encoder[0].writeRGBCode(volGainPage ? 0x00C8C8 : 0x000000); // 1-4 cyan
  Encoder[1].writeRGBCode(volGainPage ? 0xC86400 : 0x000000); // 5-8 orange
  if (volGainPage) {
    Encoder[2].writeRGBCode(g_gainEnc3IsAll ? 0x00FF00 : 0xC828C8); // ALL green / SYN magenta
  } else {
    Encoder[2].writeRGBCode(volValuePage ? (indicatorColor.r << 16 | indicatorColor.g << 8 | indicatorColor.b) : 0x000000);
  }
  Encoder[3].writeRGBCode(indicatorColor.r << 16 | indicatorColor.g << 8 | indicatorColor.b);

  // Draw the main setting status
  drawMainSettingStatus(mainSetting);
  
  // Draw additional features if this page has them
  if (currentPageInfo->hasAdditionalFeatures) {
    drawAdditionalFeatures(mainSetting);
  }

  // FastLED.setBrightness(ledBrightness);
  FastLEDshow();

  lastRenderedVolPage = pageIndex;
  lastRenderedVolSetting = mainSetting;
  }

  // Handle page navigation with encoder 3
  static int lastVolPagePosition = -1;
  static bool volMenuFirstEnter = true;
  
  // Reset tracking when entering submenu (currentVolPage is 0 and mode pos doesn't match)
  if (currentVolPage == 0 && currentMode->pos[3] != 0 && lastVolPagePosition != 0) {
    lastVolPagePosition = -1;
    volMenuFirstEnter = true;
  }
  
  if (volMenuFirstEnter) {
    Encoder[3].writeCounter((int32_t)currentVolPage);
    lastVolPagePosition = currentVolPage;
    volMenuFirstEnter = false;
  }
  
  ensureEnc3Range(0, (int)(VOL_PAGES_COUNT - 1));
  
  if (currentMode->pos[3] != lastVolPagePosition) {
    currentVolPage = currentMode->pos[3];
    if (currentVolPage >= VOL_PAGES_COUNT) currentVolPage = VOL_PAGES_COUNT - 1;
    if (currentVolPage < 0) currentVolPage = 0;
    lastVolPagePosition = currentVolPage;
  }
  
  // Handle encoder changes for pages with adjustable values.
  const bool didRedraw = handleAdditionalFeatureControls(mainSetting);
  if (!fullRedraw && didRedraw) {
    // FastLED.setBrightness(ledBrightness);
    FastLEDshow();
  }

  // Mark render dirty on any encoder movement while in submenu.
  // Skip if controls already redrew this frame (GAIN used to double-redraw + re-I2C).
  uint32_t h = hashEncoderPositions(currentMode);
  if (h != lastPosHash) {
    if (!didRedraw) menuRequestFullRedraw();
    lastPosHash = h;
  }
}

FLASHMEM void showEtcMenu() {
  static uint32_t lastPosHash = 0;
  // Redraw only when page/setting changes, except INFO which animates continuously.
  int pageIndex = currentEtcPage;
  MenuPage* currentPageInfo = &etcPages[pageIndex];
  int mainSetting = currentPageInfo->mainSetting;

  static int lastRenderedEtcPage = -1;
  static int lastRenderedEtcSetting = -1;
  bool fullRedraw = (pageIndex != lastRenderedEtcPage) || (mainSetting != lastRenderedEtcSetting);
  if (takeMenuForceFullRedraw()) fullRedraw = true;
  if (mainSetting == 39) fullRedraw = true;  // INFO animates
  // RAM (52): live audio/reverb/free dashboard
  if (mainSetting == 52) {
    static elapsedMillis ramMenuRedraw;
    if (ramMenuRedraw >= 200) {
      ramMenuRedraw = 0;
      fullRedraw = true;
    }
  }
  if (mainSetting == 49) {
    // SD page: refresh when wait/connected state changes
    extern bool sdSerialServerIsActive();
    extern bool sdSerialServerClientConnected();
    static bool lastSdActive = false;
    static bool lastSdClient = false;
    bool nowActive = sdSerialServerIsActive();
    bool nowClient = sdSerialServerClientConnected();
    if (nowActive != lastSdActive || nowClient != lastSdClient) {
      lastSdActive = nowActive;
      lastSdClient = nowClient;
      fullRedraw = true;
    }
  }
  // BATT (42): redraw every 200 ms for live updates
  if (mainSetting == 42) {
    static elapsedMillis battMenuRedraw;
    if (battMenuRedraw >= 200) {
      battMenuRedraw = 0;
      fullRedraw = true;
    }
  }

  if (fullRedraw) {
    FastLEDclear();

    // Draw page indicator as a line at y=maxY (right-aligned)
    // Match the parent menu color (ETC).
    const CRGB parent = currentMenuParentTextColor();
    const CRGB parentDim = dimIconColorFromText(parent);
    int startX = (int)maxX - ETC_PAGES_COUNT + 1;
    if (startX < 1) startX = 1;
    for (int i = 0; i < ETC_PAGES_COUNT; i++) {
      CRGB indicatorColor = (i == pageIndex) ? parent : parentDim;
      light(startX + i, maxY, indicatorColor);
    }

    // Indicators / encoder ring colors
    // For AUTO (mainSetting 15): encoder(0) is the green "generate" trigger; no blue exit indicator on encoder(3).
    // Otherwise keep ETC parent-colored encoder(3) ring (page nav).
    // Cache RGB: INFO/RAM/BATT force fullRedraw periodically — repeating identical
    // Duppa writes every frame stalls while playing.
    static uint32_t lastEtcRGB[4] = { 0xFFFFFFFFu, 0xFFFFFFFFu, 0xFFFFFFFFu, 0xFFFFFFFFu };
    static int lastEtcRgbPage = -1;
    if (pageIndex != lastEtcRgbPage) {
      for (int i = 0; i < 4; i++) lastEtcRGB[i] = 0xFFFFFFFFu;
      lastEtcRgbPage = pageIndex;
    }
    auto setEtcRGB = [&](int enc, uint32_t rgb) {
      if (enc < 0 || enc > 3) return;
      if (lastEtcRGB[enc] == rgb) return;
      lastEtcRGB[enc] = rgb;
      Encoder[enc].writeRGBCode(rgb);
    };
    if (mainSetting == 15) {
      drawIndicator('L', 'G', 1, false, false);  // Encoder(0): Large Green (generate)
      // Keep encoder(1)/(2) indicators from AI page itself (drawMainSettingStatus/drawAdditionalFeatures)
      setEtcRGB(0, 0x00FF00);
      CRGB y = getIndicatorColor('Y');
      CRGB w = getIndicatorColor('W');
      setEtcRGB(1, (uint32_t)y.r << 16 | (uint32_t)y.g << 8 | y.b);
      setEtcRGB(2, (uint32_t)w.r << 16 | (uint32_t)w.g << 8 | w.b);
      // Page-nav indicator (encoder 4) should always match ETC text color (e.g. "RSET")
      {
        CRGB c = currentMenuParentTextColor();
        drawLargeIndicatorCustom(c, 4);
        // drawLargeIndicatorCustom writes RGB — re-cache so later frames skip
        lastEtcRGB[3] = (uint32_t)c.r << 16 | (uint32_t)c.g << 8 | c.b;
      }
    } else {
      // ETC submenu: encoder 3 = value on RSET(16), LGHT(40), COLR(41), CHLD(48), RAM(52), FIRE(55), IMG(56), EYES(57)
      CRGB indicatorColor = currentMenuParentTextColor();
      const bool etcValuePage =
          (mainSetting == 16 || mainSetting == 40 || mainSetting == 41 || mainSetting == 48 ||
           mainSetting == 52 || mainSetting == 55 || mainSetting == 56 ||
           mainSetting == 57);
      // Matrix chrome without I2C; rings via cache
      {
        extern void getIndicatorXPositions(int encoderNum, int &x1, int &x2, int &x3);
        extern int ledModules;
        int x1, x2, x3;
        getIndicatorXPositions(4, x1, x2, x3);
        const bool isWide = (ledModules == 2 && maxX > 16);
        const int x4 = isWide ? min((int)maxX, x3 + 1) : x3;
        light(x1, 1, indicatorColor);
        light(x2, 1, indicatorColor);
        light(x3, 1, indicatorColor);
        if (isWide) light(x4, 1, indicatorColor);
      }
      setEtcRGB(0, 0x000000);
      setEtcRGB(1, 0x000000);
      setEtcRGB(2, etcValuePage ? ((uint32_t)indicatorColor.r << 16 | (uint32_t)indicatorColor.g << 8 | indicatorColor.b) : 0x000000);
      setEtcRGB(3, (uint32_t)indicatorColor.r << 16 | (uint32_t)indicatorColor.g << 8 | indicatorColor.b);
    }

    drawMainSettingStatus(mainSetting);
    if (currentPageInfo->hasAdditionalFeatures) {
      drawAdditionalFeatures(mainSetting);
    }

    // FastLED.setBrightness(ledBrightness);
    FastLEDshow();

    lastRenderedEtcPage = pageIndex;
    lastRenderedEtcSetting = mainSetting;
  }

  // Handle page navigation with encoder 3
  static int lastEtcPagePosition = -1;
  static bool etcMenuFirstEnter = true;
  
  // Reset tracking when entering submenu (currentEtcPage is 0 and mode pos doesn't match)
  if (currentEtcPage == 0 && currentMode->pos[3] != 0 && lastEtcPagePosition != 0) {
    lastEtcPagePosition = -1;
    etcMenuFirstEnter = true;
  }
  
  if (etcMenuFirstEnter) {
    Encoder[3].writeCounter((int32_t)currentEtcPage);
    lastEtcPagePosition = currentEtcPage;
    etcMenuFirstEnter = false;
  }
  
  ensureEnc3Range(0, (int)(ETC_PAGES_COUNT - 1));
  if (currentMode->pos[3] != lastEtcPagePosition) {
    currentEtcPage = currentMode->pos[3];
    if (currentEtcPage >= ETC_PAGES_COUNT) currentEtcPage = ETC_PAGES_COUNT - 1;
    if (currentEtcPage < 0) currentEtcPage = 0;
    lastEtcPagePosition = currentEtcPage;
  }

  const bool didRedraw = handleAdditionalFeatureControls(mainSetting);
  if (!fullRedraw && didRedraw) {
    // FastLED.setBrightness(ledBrightness);
    FastLEDshow();
  }

  // Mark render dirty on any encoder movement while in submenu (except INFO which animates).
  // Skip if controls already redrew this frame (avoids re-I2C RGB on every tick).
  if (mainSetting != 39) {
    uint32_t h = hashEncoderPositions(currentMode);
    if (h != lastPosHash) {
      if (!didRedraw) menuRequestFullRedraw();
      lastPosHash = h;
    }
  }
}

static inline CRGB dimIconColorFromText(CRGB textColor) {
  // Match the existing UI dim level (~20) regardless of the base text color.
  CRGB c = textColor;
  uint8_t maxv = max(c.r, max(c.g, c.b));
  if (maxv == 0) return c;
  const uint8_t target = 20; // matches UI_DIM_* constants in colors.h
  uint16_t scale = (uint16_t)target * 255u / maxv;
  if (scale > 255) scale = 255;
  c.nscale8_video((uint8_t)scale);
  return c;
}

static inline CRGB menuTextColorFromCol(uint8_t colIndex) {
  // Use palette colors from `col[]` (voice colors), but normalize brightness
  // to match the rest of the UI text (~120 peak channel).
  extern CRGB col[];
  CRGB c = col[colIndex];
  uint8_t maxv = max(c.r, max(c.g, c.b));
  if (maxv == 0) return c;
  const uint8_t target = 120; // similar to UI_* brightness
  uint16_t scale = (uint16_t)target * 255u / maxv;
  if (scale > 255) scale = 255;
  c.nscale8_video((uint8_t)scale);
  return c;
}

static inline CRGB currentMenuParentTextColor() {
  // Submenus should match their main-menu parent item color:
  // SETT=col[6], RECS=col[7], MIDI=col[8], VOL=col[5], ETC=col[14]
  if (inLookSubmenu) return menuTextColorFromCol(6);
  if (inRecsSubmenu) return menuTextColorFromCol(7);
  if (inMidiSubmenu) return menuTextColorFromCol(8);
  if (inVolSubmenu)  return menuTextColorFromCol(5);
  if (inEtcSubmenu)  return menuTextColorFromCol(14);
  return UI_WHITE;
}

// Draw a "large" top-row indicator and set encoder ring to an arbitrary color.
// This is used where we want the indicator color to match submenu text colors (palette-derived),
// not one of the fixed indicator color codes.
static inline void drawLargeIndicatorCustom(CRGB color, int encoderNum) {
  extern void getIndicatorXPositions(int encoderNum, int &x1, int &x2, int &x3);
  extern int ledModules;
  extern unsigned int maxX;

  int x1, x2, x3;
  getIndicatorXPositions(encoderNum, x1, x2, x3);
  const bool isWide = (ledModules == 2 && maxX > 16);
  const int x4 = isWide ? min((int)maxX, x3 + 1) : x3;

  light(x1, 1, color);
  light(x2, 1, color);
  light(x3, 1, color);
  if (isWide) {
    light(x4, 1, color);
  }

  if (encoderNum >= 1 && encoderNum <= NUM_ENCODERS) {
    uint32_t rgbCode = (uint32_t(color.r) << 16) | (uint32_t(color.g) << 8) | (uint32_t)color.b;
    Encoder[encoderNum - 1].writeRGBCode(rgbCode);
  }
}

static inline uint32_t hashEncoderPositions(const Mode *m) {
  // Simple FNV-1a over the 4 encoder positions to detect any knob changes.
  uint32_t h = 2166136261u;
  for (int i = 0; i < NUM_ENCODERS; i++) {
    h ^= (uint32_t)m->pos[i];
    h *= 16777619u;
  }
  return h;
}

FLASHMEM void drawMainSettingStatus(int setting) {
  switch (setting) {
    case 1: // DAT - Load/Save
      // FILE = folder
      {
        const CRGB tc = menuTextColorFromCol(1);
        showIcons(ICON_FOLDER_BIG, dimIconColorFromText(tc));
        drawText("FILE", 2, 3, tc);
      }
      break;
      
    case 2: // KIT - Sample Pack
      // Pack = pack
      {
        const CRGB tc = menuTextColorFromCol(2);
        showIcons(OLD_ICON_SAMPLEPACK, dimIconColorFromText(tc));
        drawText("PACK", 2, 3, tc);
      }
      break;
      
    case 3: // WAV - Wave Selection
      // wave = sample
      {
        const CRGB tc = menuTextColorFromCol(3);
        showIcons(ICON_SAMPLE_BIG, dimIconColorFromText(tc));
      if (GLOB.currentChannel > 0 && GLOB.currentChannel < 9) {
        drawText("WAVE", 2, 3, tc);
      } else {
        drawText("(-)", 2, 3, tc);
      }
      }
      break;
      
    case 4: // REC - Recording Mode (menu/mic) - encoder 3: MIC/LINE
      drawText("INPT", 2, 10, currentMenuParentTextColor());
      drawRecMode();
      drawIndicator('L', recMode == 1 ? 'W' : 'X', 3);  // White=MIC, Blue=LINE
      break;
      
    case 5: // BPM - BPM/Volume
      // BPM = Clock
      {
        const CRGB tc = menuTextColorFromCol(4);
        showIcons(ICON_CLOCK, dimIconColorFromText(tc));
        drawText("BPM", 2, 3, tc);
      }
      break;
      
    case 7: // CHN - MIDI Voice Select - encoder 3: YPOS/MIDI/KEYS
      drawText("CH", 2, 10, currentMenuParentTextColor());
      drawMidiVoiceSelect();
      drawIndicator('L', voiceSelect == 1 ? 'X' : (voiceSelect == 2 ? 'M' : 'G'), 3);
      break;
      
    case 8: // TRN - MIDI Transport - encoder 3: OFF/GET/SEND
      drawText("TRAN", 2, 10, currentMenuParentTextColor());
      drawMidiTransport();
      drawIndicator('L', transportMode == 0 ? 'R' : (transportMode == 1 ? 'G' : 'X'), 3);
      break;
      
    case 13: // SEND - MIDI Send (CLCK, NOTE, BOTH) - encoder 3
      drawText("SEND", 2, 10, currentMenuParentTextColor());
      drawMidiSend();
      {
        extern int midiSendMode;
        drawIndicator('L', midiSendMode == 0 ? 'Y' : (midiSendMode == 1 ? 'G' : 'X'), 3);
      }
      break;

    case 44: // RCVE - MIDI Note Receive (OFF/NOTE) - encoder 3
      {
        extern bool MIDI_NOTE_RECEIVE;
        drawText("RCVE", 2, 10, currentMenuParentTextColor());
        drawMenuValue(MIDI_NOTE_RECEIVE ? "NOTE" : "OFF", 2, 3, MIDI_NOTE_RECEIVE ? UI_GREEN : UI_RED);
        drawIndicator('L', MIDI_NOTE_RECEIVE ? 'G' : 'R', 3);
      }
      break;

    case 51: // CLMP - fold incoming pitch into the visible grid
      {
        extern bool MIDI_NOTE_CLAMP;
        drawText("CLMP", 2, 10, currentMenuParentTextColor());
        drawMenuValue(MIDI_NOTE_CLAMP ? "ON" : "OFF", 2, 3, MIDI_NOTE_CLAMP ? UI_GREEN : UI_RED);
        drawIndicator('L', MIDI_NOTE_CLAMP ? 'G' : 'R', 3);
      }
      break;

    case 45: // SYNC - Transport delay SNC1/SNC2 −127..+127 ms
      {
        extern int8_t transportSendDelayMs;
        extern int8_t transportRcveDelayMs;
        const CRGB tc = currentMenuParentTextColor();
        int syncEdit = (currentMode->pos[1] == 0) ? 0 : 1;
        drawText(syncEdit == 0 ? "SNC1" : "SNC2", 2, 10, tc);
        int val = (syncEdit == 0) ? (int)transportSendDelayMs : (int)transportRcveDelayMs;
        char buf[10];
        snprintf(buf, sizeof(buf), "%d", val);
        drawMenuValue(buf, 2, 3, syncEdit == 0 ? UI_GREEN : UI_RED);
        drawIndicator('L', 'Y', 1);
        drawIndicator('L', 'W', 2);
      }
      break;

    case 50: { // PPQN - enc1 width, enc2 STOP/CONT, enc3 OFF/rate (click POL)
      extern bool getPulseClockEnabled();
      extern bool getPulseClockPolarityPositive();
      extern bool getPulseClockStopWithPlay();
      extern uint8_t getPulseClockPpqn();
      extern uint8_t getPulseClockWidthMs();
      const CRGB tc = currentMenuParentTextColor();
      drawText("PPQN", 2, 10, tc);
      bool on = getPulseClockEnabled();
      bool polPos = getPulseClockPolarityPositive();
      bool stopPlay = getPulseClockStopWithPlay();
      if (g_ppqnUiFocus == 2) {
        char buf[8];
        snprintf(buf, sizeof(buf), "%u", (unsigned)getPulseClockWidthMs());
        drawMenuValue(buf, 2, 3, UI_WHITE);
      } else if (g_ppqnUiFocus == 1) {
        drawMenuValue(stopPlay ? "STOP" : "CONT", 2, 3, stopPlay ? UI_RED : UI_GREEN);
      } else if (!on) {
        drawMenuValue("OFF", 2, 3, UI_RED);
      } else {
        char buf[8];
        snprintf(buf, sizeof(buf), "%c%u", polPos ? '+' : '-', (unsigned)getPulseClockPpqn());
        drawMenuValue(buf, 2, 3, polPos ? UI_GREEN : UI_RED);
      }
      drawIndicator('L', 'W', 1);
      drawIndicator('L', stopPlay ? 'R' : 'G', 2);
      drawIndicator('L', polPos ? 'G' : 'R', 3);
      break;
    }

    case 58: { // SIDE - which voice pulses analog sidechain out
      extern uint8_t getSidechainVoice();
      extern CRGB col[];
      const uint8_t ch = getSidechainVoice();
      drawText("SIDE", 2, 10, currentMenuParentTextColor());
      if (!ch) {
        drawMenuValue("OFF", 2, 3, UI_RED);
        drawIndicator('L', 'R', 3);
      } else {
        char buf[8];
        snprintf(buf, sizeof(buf), "%u", (unsigned)ch);
        drawMenuValue(buf, 2, 3, col[ch]);
        drawIndicator('L', 'G', 3);
      }
      break;
    }

    case 59: { // CIN - enc1 width (hold-off ms), enc3 PPQN
      extern uint8_t getAnalogInPpqn();
      extern uint8_t getAnalogInHoldMs();
      const CRGB tc = currentMenuParentTextColor();
      char buf[8];
      if (g_cinFocus == 1) {
        drawText("WID", 2, 10, tc);
        snprintf(buf, sizeof(buf), "%u", (unsigned)getAnalogInHoldMs());
        drawMenuValue(buf, 2, 3, UI_WHITE);
      } else {
        drawText("CIN", 2, 10, tc);
        snprintf(buf, sizeof(buf), "%u", (unsigned)getAnalogInPpqn());
        drawMenuValue(buf, 2, 3, UI_WHITE);
      }
      drawIndicator('L', 'W', 1);
      drawIndicator('L', 'W', 3);
      break;
    }
      
    case 9: // PMD - Pattern Mode - encoder 3
      drawText("PMODE", 2, 10, currentMenuParentTextColor());
      drawPatternMode();
      drawIndicator('L', patternMode == -1 ? 'R' : (patternMode == 1 ? 'G' : (patternMode == 2 ? 'Y' : 'N')), 3);
      break;
      
    case 10: // FLW - Flow Mode - encoder 3
      drawText("FLOW", 2, 10, currentMenuParentTextColor());
      drawFlowMode();
      drawIndicator('L', flowMode == 1 ? 'G' : 'R', 3);
      break;
      
    case 11: // OTR - Fast Rec Mode
      drawText("TRIG", 2, 10, currentMenuParentTextColor());
      drawFastRecMode();
      break;
      
    case 12: // CLR - Rec Channel Clear - encoder 3
      drawText("CLR", 2, 10, currentMenuParentTextColor());
      drawRecChannelClear();
      drawIndicator('L', 'W', 3);
      break;
      
    case 15: // AI - Song Generation
      drawText("AUTO", 2, 10, currentMenuParentTextColor());
      // AUTO generate: encoder(0) press triggers generation -> green indicator on encoder(0)
      drawIndicator('L', 'G', 1);  // Encoder(0): Large Green (generate)
      drawIndicator('L', 'Y', 2);  // Encoder 2: Large Yellow (base start)
      drawIndicator('L', 'W', 3);  // Encoder 3: Large White (base end)
      break;
      
    case 16: // RST - Reset
      drawText("RSET", 2, 10, currentMenuParentTextColor());
      /*if (resetMenuOption == 0) {
        drawText("EFX", 2, 3, CRGB(100, 0, 0));  // Dark Red
      } else {
        drawText("FULL", 2, 3, CRGB(100, 0, 0));  // Dark Red
      }*/
      drawIndicator('L', 'G', 2);  // Encoder 2: press applies the reset
      drawIndicator('L', 'O', 3);  // Encoder 3: turn to pick SD/EFX/FULL/FILE/PACK/ASAV
      
      break;

    case 39: // INFO - Version / credits scroll
      drawEtcInfoPage();
      break;

    case 52: // RAM - live audio memory / reverb / free blocks dashboard
      drawEtcRamPage();
      break;

    case 49: // SD - USB Serial file server (active while this page is open)
      {
        extern bool sdSerialServerClientConnected();
        const CRGB tc = currentMenuParentTextColor();
        drawText("SD", 2, 10, tc);
        bool connected = sdSerialServerClientConnected();
        // WAIT (yellow) until host connects; OK (green) once client talks
        drawMenuValue(connected ? "OK" : "WAIT", 2, 3, connected ? UI_GREEN : UI_YELLOW);
      }
      break;
      
    case 40: // LGHT - LED Strip toggle (OFF/ON) - encoder 3
      {
        extern bool getLedStripEnabled();
        const CRGB tc = currentMenuParentTextColor();
        drawText("LGHT", 2, 10, tc);
        bool enabled = getLedStripEnabled();
        drawMenuValue(enabled ? "ON" : "OFF", 2, 3, enabled ? CRGB(0, 255, 0) : CRGB(255, 0, 0));
        drawIndicator('L', enabled ? 'G' : 'R', 3);
      }
      break;
      
    case 41: // COLR - Color scheme selection (0=default, 1, 2, 3=custom) - encoder 3
      {
        const CRGB tc = currentMenuParentTextColor();
        drawText("COLR", 2, 10, tc);
        char schemeText[2];
        snprintf(schemeText, sizeof(schemeText), "%d", currentColorScheme);
        drawMenuValue(schemeText, 2, 3, UI_GREEN);
        drawIndicator('L', 'G', 3);
      }
      break;

    case 42: // BATT - voltage-based estimate using calibrated divider ratio
      {
        extern int getBatteryPercent();
        const CRGB tc = currentMenuParentTextColor();
        drawText("BATT", 2, 10, tc);
        
        int pct = getBatteryPercent();
        pct = constrain(pct, 0, 100);
        
        char pctText[6];
        snprintf(pctText, sizeof(pctText), "%d%%", pct);
        
        // Color scale: >30% Green, 15-30% Orange, <15% Red
        CRGB stateColor = (pct > 30) ? UI_GREEN : (pct > 15) ? CRGB(255, 165, 0) : UI_RED;
        drawText(pctText, 2, 3, stateColor);
      }
      break;

    case 48: // CHLD - Child lock toggle (OFF/ON) - encoder 3
      {
        extern bool getChildLockEnabled();
        const CRGB tc = currentMenuParentTextColor();
        drawText("CHLD", 2, 10, tc);
        bool enabled = getChildLockEnabled();
        drawMenuValue(enabled ? "ON" : "OFF", 2, 3, enabled ? CRGB(0, 255, 0) : CRGB(255, 0, 0));
        drawIndicator('L', enabled ? 'G' : 'R', 3);
      }
      break;

    case 56: { // IMG - Image mode (OFF/ON)
      extern bool imageMode;
      const CRGB tc = currentMenuParentTextColor();
      drawText("IMG", 2, 10, tc);
      drawMenuValue(imageMode ? "ON" : "OFF", 2, 3, imageMode ? UI_GREEN : UI_RED);
      drawIndicator('L', imageMode ? 'G' : 'R', 3);
      break;
    }

    case 57: { // EYES - screensaver idle OFF / 1MIN / 5MIN / 15MIN
      extern uint8_t eyesMode;
      const CRGB tc = currentMenuParentTextColor();
      drawText("EYES", 2, 10, tc);
      const char *label = "OFF";
      CRGB vc = UI_RED;
      if (eyesMode == 1) { label = "1MIN"; vc = UI_GREEN; }
      else if (eyesMode == 2) { label = "5MIN"; vc = UI_GREEN; }
      else if (eyesMode == 3) { label = "15MIN"; vc = UI_GREEN; }
      drawMenuValue(label, 2, 3, vc);
      drawIndicator('L', eyesMode == 0 ? 'R' : 'G', 3);
      break;
    }

    case 55: // FIRE - enc1 size, enc2 count, enc3 voice (click: gravity, colour)
      {
        extern uint8_t fireVoice;
        extern uint8_t fireLevel;
        extern uint8_t fireSize;
        extern uint8_t fireGravity;
        extern uint8_t fireColor;
        extern uint8_t fireFocus;
        extern CRGB col[];
        const CRGB tc = currentMenuParentTextColor();
        drawText("FIRE", 2, 10, tc);
        clearTextArea(1, 3, (int)maxX);
        char num[4];
        snprintf(num, sizeof(num), "%u", fireSize);
        drawText(num, 1, 3, CRGB(255, 140, 20));
        snprintf(num, sizeof(num), "%u", fireLevel);
        drawText(num, (int)maxX >= 24 ? 8 : 5, 3, CRGB(255, 180, 60));
        const bool wide = (int)maxX >= 24;
        int voiceX = wide ? 26 : 12;
        if (wide) {
          snprintf(num, sizeof(num), "%u", fireGravity);
          drawText(num, 14, 3, fireFocus == 1 ? CRGB(220, 220, 220) : CRGB(70, 70, 70));
          snprintf(num, sizeof(num), "%u", fireColor);
          drawText(num, 20, 3, fireFocus == 2 ? CRGB(255, 220, 120) : CRGB(80, 70, 30));
        }
        if (!wide && fireFocus != 0) {
          snprintf(num, sizeof(num), "%u", fireFocus == 1 ? fireGravity : fireColor);
          drawText(num, 12, 3, fireFocus == 1 ? CRGB(220, 220, 220) : CRGB(255, 220, 120));
        } else if (!fireVoice) {
          drawText(wide ? "OFF" : "-", voiceX, 3, CRGB(255, 0, 0));
        } else if (fireVoice == 15) {
          drawText(wide ? "ALL" : "A", voiceX, 3, CRGB(255, 220, 120));
        } else {
          snprintf(num, sizeof(num), "%u", fireVoice);
          int vx = voiceX;
          if (!wide && fireVoice >= 10) vx = 10;
          drawText(num, vx, 3, col[fireVoice]);
        }
        int half = (int)maxX / 2;
        if (half < 1) half = 1;
        int gDots = (fireGravity * half) / 8;
        int cDots = (fireColor * ((int)maxX - half)) / 8;
        for (int x = 1; x <= (int)maxX; x++) {
          CRGB bar = CRGB(0, 0, 0);
          if (x <= half && x <= gDots) {
            bar = CRGB(180, 180, 180);
            if (fireFocus == 1) bar = CRGB(255, 255, 255);
          } else if (x > half && (x - half) <= cDots) {
            bar = CRGB(140, 90, 20);
            if (fireFocus == 2) bar = CRGB(255, 200, 60);
          }
          light(x, 8, bar);
        }
        drawIndicator('L', 'O', 1);
        drawIndicator('L', 'O', 2);
        char focusCode = fireVoice ? 'G' : 'R';
        if (fireFocus == 1) focusCode = 'W';
        else if (fireFocus == 2) focusCode = 'Y';
        drawIndicator('L', focusCode, 3);
      }
      break;

    case 19: // SETTINGS - Submenu
      // SETTINGS = settings icon
      {
        const CRGB tc = menuTextColorFromCol(6);
        showIcons(ICON_SETTINGS_BIG, dimIconColorFromText(tc));
        drawText("SETT", 2, 3, tc);
      }
      break;
      
    case 20: // RECS - Submenu
      // REC = record (icon shown on main menu entry)
      {
        const CRGB tc = menuTextColorFromCol(7);
        showIcons(ICON_RECORD, dimIconColorFromText(tc));
        drawText("REC", 2, 3, tc);
      }
      break;
      
    case 21: // MIDI - Submenu
      // MIDI = midi
      {
        const CRGB tc = menuTextColorFromCol(8);
        showIcons(ICON_MIDISYNC, dimIconColorFromText(tc));
        drawText("MIDI", 2, 3, tc);
      }
      break;
      
    case 22: // SONG - Song Mode
      // SONG = song
      {
        const CRGB tc = menuTextColorFromCol(13);
        showIcons(ICON_SONG, dimIconColorFromText(tc));
        drawText("SONG", 2, 3, tc);
      }
      break;
      
    case 17: // VIEW - Simple Notes View - encoder 3
      drawText("VIEW", 2, 10, currentMenuParentTextColor());
      drawSimpleNotesView();
      drawIndicator('L', 'W', 3);
      break;
      
    case 18: // LOOP - Loop Length - encoder 3
      drawText("LOOP", 2, 10, currentMenuParentTextColor());
      drawLoopLength();
      drawIndicator('L', 'G', 3);
      break;

    case 54: { // VMOD - per-voice page loops (OFF/ON)
      extern bool voiceMode;
      extern bool imageMode;
      const CRGB tc = currentMenuParentTextColor();
      drawText("VMOD", 2, 10, tc);
      // VMOD locked off while IMG is on.
      const bool on = voiceMode && !imageMode;
      drawMenuValue(on ? "ON" : "OFF", 2, 3, on ? UI_GREEN : UI_RED);
      drawIndicator('L', on ? 'G' : 'R', 3);
      break;
    }
      
    case 23: // LEDS - LED mode (1, 1B, 2, 2B) - encoder 3
      drawText("LEDS", 2, 10, currentMenuParentTextColor());
      drawLedModules();
      drawIndicator('L', 'G', 3);
      break;

    case 24: // PONG toggle
      drawText("PONG", 2, 10, currentMenuParentTextColor());
      clearTextArea(2, 3, 8);
      clearTextArea(6, 3, 8);
      clearTextArea(10, 3, 8);
      if (pong) {
        drawText("ON", 10, 3, UI_GREEN);
      } else {
        drawMenuValue("OFF", 6, 3, UI_RED);
      }
      if (pong) {
        char speedText[6];
        int speedValue = pongIntervalToSpeed(pongUpdateInterval);
        snprintf(speedText, sizeof(speedText), "%02d", speedValue);
        drawText(speedText, 2, 3, CRGB(0, 150, 255));
        {
          CRGB indicatorColor = getIndicatorColor('B');
          Encoder[2].writeRGBCode(indicatorColor.r << 16 | indicatorColor.g << 8 | indicatorColor.b);
        }
        drawIndicator('L', 'B', 3);
      } else {
        Encoder[2].writeRGBCode(0x000000);
      }
      break;

    case 34: // ETC - Submenu
      {
        const CRGB tc = menuTextColorFromCol(14);
        showIcons(ICON_PATTERN, dimIconColorFromText(tc));
        drawText("ETC", 2, 3, tc);
      }
      break;
      
    case 38: // DRAW - Toggle between L+R and R modes
      drawText("DRAW", 2, 10, currentMenuParentTextColor());
      drawMenuValue(drawMode == 0 ? "L+R" : "R", 2, 3, UI_GREEN);
      break;

    case 47: { // MUTE — columns 1..16 = user CH1..CH16 (see userChToInternalDrawR); green=in mask, red=out; enc1=CH, enc2=toggle
      const CRGB tc = currentMenuParentTextColor();
      drawText("MUTE", 2, 10, tc);
      int selUch = constrain((int)currentMode->pos[1], 1, 16);
      const int rowDots = 3;
      for (int uch = 1; uch <= 16; uch++) {
        int in = userChToInternalDrawR(uch);
        bool inMask = (drawRFullMuteCustomUnmuteMask & (1u << in)) != 0;
        CRGB dot = inMask ? UI_GREEN : UI_RED;
        if (uch == selUch) {
          dot.r = (uint8_t)min(255, (int)dot.r + 100);
          dot.g = (uint8_t)min(255, (int)dot.g + 60);
          dot.b = (uint8_t)min(255, (int)dot.b + 60);
        }
        light(uch, rowDots, dot);
      }
      drawIndicator('L', 'Y', 2);
      drawIndicator('L', 'W', 3);
      break;
    }

    case 25: { // CTRL - encoder behaviour
      drawText("CTRL", 2, 10, currentMenuParentTextColor());
      drawMenuValue(ctrlMode == 0 ? "PAGE" : "VOL", 2, 3, ctrlMode == 0 ? UI_GREEN : UI_ORANGE);
      // Enc3 edits PAGE/VOL — green for PAGE, orange for VOL (ring + row-1 indicator).
      drawIndicator('L', ctrlMode == 0 ? 'G' : 'O', 3);
      break;
    }
    
    case 26: // VOL - Submenu
      // VOL = volume
      {
        const CRGB tc = menuTextColorFromCol(5);
        showIcons(ICON_VOLUME_BIG, dimIconColorFromText(tc));
        drawText("VOL", 2, 3, tc);
      }
      break;

    case 27: { // MAIN - Headphone output volume - encoder 3
      drawText("MAIN", 2, 10, currentMenuParentTextColor());
      extern Mode *currentMode;
      extern struct GlobalVars GLOB;
      
      // Display GLOB.vol directly as 0-100
      int volDisplay = GLOB.vol;
      // Handle legacy values (0-10) for backward compatibility
      if (volDisplay <= 10) {
        volDisplay = volDisplay * 10;
      }
      char volText[8];
      snprintf(volText, sizeof(volText), "%d", volDisplay);
      drawText(volText, 2, 3, CRGB(55, 10, 0)); // Orange-red gradient
      
      // Dynamic gradient color based on volume level (use float for color calculation)
      float vol = GLOB.vol / 10.0f;
      int r = (int)(vol * 255.0f);
      int g = (int)((1.0f - vol) * 100.0f);
      int b = 0;
      CRGB volColor = CRGB(r, g, b);
      Encoder[2].writeRGBCode(volColor.r << 16 | volColor.g << 8 | volColor.b);
      drawIndicator('L', 'O', 3);
      break;
    }
    
    case 28: { // LOUT - Line output volume - encoder 3
      drawText("LOUT", 2, 10, currentMenuParentTextColor());
      extern uint8_t lineOutLevelSetting;
      char levelText[8];
      // Display mapped range 1..19 (LINEOUT_MIN..LINEOUT_MAX) for user friendliness
      int displayVal = (lineOutLevelSetting - LINEOUT_MIN) + 1;  // 13->1, 31->19
      snprintf(levelText, sizeof(levelText), "%d", displayVal);
      drawText(levelText, 2, 3, CRGB(255, 192, 203)); // Pink
      
      // Pink color for encoder
      CRGB pinkColor = CRGB(255, 192, 203);
      Encoder[2].writeRGBCode(pinkColor.r << 16 | pinkColor.g << 8 | pinkColor.b);
      drawIndicator('L', 'M', 3);
      break;
    }
    
    case 29: { // PREV - Preview volume - encoder 3
      drawText("PREV", 2, 10, currentMenuParentTextColor());
      extern unsigned int previewVol;
      // Display as 0-50 instead of 0.00-0.50
      char volText[8];
      snprintf(volText, sizeof(volText), "%d", previewVol);
      drawText(volText, 2, 3, CRGB(0, 160, 80)); // Green
      
      // Green color for encoder
      CRGB greenColor = CRGB(0, 160, 80);
      Encoder[2].writeRGBCode(greenColor.r << 16 | greenColor.g << 8 | greenColor.b);
      drawIndicator('L', 'G', 3);
      break;
    }
    
    case 30: { // MIC - Microphone gain - encoder 3
      drawText("MIC", 2, 10, currentMenuParentTextColor());
      extern unsigned int micGain;
      char gainText[8];
      snprintf(gainText, sizeof(gainText), "%d", micGain);
      drawText(gainText, 2, 3, CRGB(55, 0, 0)); // Red
      
      // Red color for encoder
      CRGB redColor = CRGB(55, 0, 0);
      Encoder[2].writeRGBCode(redColor.r << 16 | redColor.g << 8 | redColor.b);
      drawIndicator('L', 'R', 3);
      break;
    }
    
    case 31: { // L-IN - Line input level - encoder 3
      drawText("L-IN", 2, 10, currentMenuParentTextColor());
      extern unsigned int lineInLevel;
      char levelText[8];
      snprintf(levelText, sizeof(levelText), "%d", lineInLevel);
      drawText(levelText, 2, 3, CRGB(0, 0, 55)); // Blue
      
      // Blue color for encoder
      CRGB blueColor = CRGB(0, 0, 55);
      Encoder[2].writeRGBCode(blueColor.r << 16 | blueColor.g << 8 | blueColor.b);
      drawIndicator('L', 'X', 3);
      break;
    }

    case 36: { // 2-CH - Stereo routing (OFF, M+P, or L+R) - encoder 3
      drawText("2-CH", 2, 10, currentMenuParentTextColor());
      // Clear text area before drawing (3 chars max: "OFF", "M+P", "L+R")
      clearTextArea(6, 3, 8);
      extern int8_t stereoChannel;
      if (stereoChannel == 0) {
        drawText("OFF", 6, 3, UI_RED);
      } else if (stereoChannel == 1) {
        drawText("M+P", 6, 3, UI_GREEN);
      } else { // stereoChannel == 2
        drawText("L+R", 6, 3, UI_GREEN);
      }
      CRGB blueColor = getIndicatorColor('X');
      Encoder[2].writeRGBCode(blueColor.r << 16 | blueColor.g << 8 | blueColor.b);
      drawIndicator('L', 'X', 3);
      break;
    }

    case 43: { // SPKR - Speaker toggle - encoder 3
      extern bool getSpkrEnabled();
      const CRGB tc = currentMenuParentTextColor();
      drawText("SPKR", 2, 10, tc);
      // Display was inverted: the internal "enabled" flag actually corresponds to the speaker
      // being OFF, so present the real speaker state (ON when !enabled).
      bool speakerOn = !getSpkrEnabled();
      drawMenuValue(speakerOn ? "ON" : "OFF", 2, 3, speakerOn ? CRGB(0, 255, 0) : CRGB(255, 0, 0));
      drawIndicator('L', speakerOn ? 'G' : 'R', 3);
      break;
    }

    case 46: { // HFC — 0, 10..250, 256 (encoder 2)
      drawText("HFC", 2, 10, currentMenuParentTextColor());
      extern uint16_t codecHfCut;
      char valText[8];
      unsigned disp = (unsigned)codecHfCut;
      if (disp > 256u) disp = 256u;
      if (disp != 256u) disp = (disp / 10u) * 10u;
      snprintf(valText, sizeof(valText), "%u", disp);
      clearTextArea(2, 3, 16);
      drawText(valText, 2, 3, CRGB(200, 40, 40));
      CRGB encCol = CRGB(200, 40, 40);
      Encoder[2].writeRGBCode(encCol.r << 16 | encCol.g << 8 | encCol.b);
      drawIndicator('L', 'R', 3);
      break;
    }

    case 53: { // GAIN — enc1 1-4, enc2 5-8, enc3 SYN or ALL (click toggles)
      extern uint8_t mixGain14;
      extern uint8_t mixGain58;
      extern uint8_t mixGainSynth;
      extern uint8_t mixGainMaster;
      const char* title = "ALL";
      uint8_t shown = mixGainMaster;
      CRGB valCol = CRGB(0, 255, 0);
      if (g_gainUiFocus == 0) { title = "1-4"; shown = mixGain14; valCol = CRGB(0, 200, 200); }
      else if (g_gainUiFocus == 1) { title = "5-8"; shown = mixGain58; valCol = CRGB(200, 100, 0); }
      else if (g_gainUiFocus == 2) { title = "SYN"; shown = mixGainSynth; valCol = CRGB(200, 40, 200); }
      // Title length changes (ALL/1-4/SYN) — clear before draw (partial redraw path).
      clearTextArea(1, 10, (int)maxX);
      drawText(title, 2, 10, currentMenuParentTextColor());
      char valText[8];
      snprintf(valText, sizeof(valText), "%u.%ux", (unsigned)(shown / 10u), (unsigned)(shown % 10u));
      drawText(valText, 2, 3, valCol);
      const uint8_t bars[4] = { mixGain14, mixGain58, mixGainSynth, mixGainMaster };
      const CRGB barCol[4] = { CRGB(0, 200, 200), CRGB(200, 100, 0), CRGB(200, 40, 200), CRGB(0, 255, 0) };
      for (int i = 0; i < 4; i++) {
        int filled = ((int)bars[i] * 4 + MIX_GAIN_MAX / 2) / MIX_GAIN_MAX;
        if (filled > 4) filled = 4;
        int x0 = 1 + i * 4;
        CRGB on = barCol[i];
        if ((int)g_gainUiFocus != i) {
          on.nscale8(90);
        }
        for (int k = 0; k < 4; k++) {
          light(x0 + k, 8, (k < filled) ? on : CRGB(0, 0, 0));
        }
      }
      drawIndicator('L', 'X', 1);
      drawIndicator('L', 'O', 2);
      drawIndicator('L', g_gainEnc3IsAll ? 'G' : 'M', 3);
      break;
    }
    
    case 32: { // CRSR - Cursor type - encoder 3
      drawText("CRSR", 2, 10, currentMenuParentTextColor());
      extern bool showChannelNr;
      const char* lbl = showChannelNr ? "CHNR" : "NORM";
      CRGB col = showChannelNr ? CRGB(150, 200, 0) : CRGB(150, 100, 0);
      drawMenuValue(lbl, 2, 3, col);
      Encoder[2].writeRGBCode(CRGB(0, 255, 0).r << 16 | CRGB(0, 255, 0).g << 8 | CRGB(0, 255, 0).b);
      drawIndicator('L', 'G', 3);
      break;
    }

    case 33: { // PREV - Preview trigger mode - encoder 3
      drawText("PREV", 2, 10, currentMenuParentTextColor());
      const char* prevLbl = "ON";
      CRGB prevCol = UI_GREEN;
      if (previewTriggerMode == PREVIEW_MODE_PRESS) {
        prevLbl = "PRSS";
        prevCol = CRGB(0, 150, 255);
      } else if (previewTriggerMode == PREVIEW_MODE_SYNC) {
        prevLbl = "SYNC";
        prevCol = CRGB(255, 165, 0);
      }
      drawMenuValue(prevLbl, 2, 3, prevCol);
      CRGB greenColor = getIndicatorColor('G');
      Encoder[2].writeRGBCode(greenColor.r << 16 | greenColor.g << 8 | greenColor.b);
      drawIndicator('L', 'B', 3);
      break;
    }
  }
}

FLASHMEM void drawAdditionalFeatures(int setting) {
  switch (setting) {
    case 4: { // REC page - Mic Gain
      //drawText("GAIN:", 2, 12, UI_DIM_WHITE);
      char gainText[8];
      sprintf(gainText, "%d", micGain);
      //drawText(gainText, 8, 12, UI_WHITE);
      
      // Mic gain meter is now drawn vertically in drawRecMode() on x=16
      // No horizontal meter needed here since page indicator uses y=16
      break;
    }
      
    
    case 15: { // AI page - Base Page Range + Additional Pages Count (all on one line)
      // Draw everything on y=8: Orange base range + Green additional pages count
      for (int x = 1; x <= 16; x++) {
        if (x >= aiBaseStartPage && x <= aiBaseEndPage) {
          light(x, 8, CRGB(255, 165, 0)); // Orange for base pages
        } else if (x > aiBaseEndPage && x <= aiBaseEndPage + aiTargetPage) {
          light(x, 8, CRGB(0, 255, 0)); // Green for additional pages to generate
        } else {
          light(x, 8, CRGB(0, 0, 0));
        }
      }
      
      // Draw "PAGE" text in pink at the bottom
      drawText("PAGE", 2, 3, CRGB(0, 0, 10)); // Pink color
      break;
    }

    case 16: { // RST page - show current mode (SD, EFX, FULL, FILE, PACK, ASAV)
      const char* modeText;
      if (resetMenuOption == 0) {
        modeText = "SD";
      } else if (resetMenuOption == 1) {
        modeText = "EFX";
      } else if (resetMenuOption == 2) {
        modeText = "FULL";
      } else if (resetMenuOption == 3) {
        modeText = "FILE";
      } else if (resetMenuOption == 4) {
        modeText = "PACK";
      } else {
        modeText = "ASAV";
      }
      drawMenuValue(modeText, 2, 3, UI_ORANGE);
      break;
    }
    
  }
}

FLASHMEM void drawGenreSelection() {
  // Draw genre options on y=8
  const char* genres[] = {"BLNK", "TECH", "HIPH", "DNB", "HOUS", "AMBT"};
  CRGB genreColors[] = {
    CRGB(100, 100, 100), // BLNK - gray
    CRGB(255, 100, 0),   // TECH - orange
    CRGB(255, 0, 255),   // HIPH - magenta
    CRGB(0, 255, 0),     // DNB - green
    CRGB(0, 100, 255),   // HOUS - blue
    CRGB(255, 255, 0)    // AMBT - yellow
  };
  
  // Draw current genre text
  drawText(genres[genreType], 2, 3, genreColors[genreType]);
}

void cycleFireMenuFocus() {
  extern uint8_t fireFocus;
  fireFocus = (uint8_t)((fireFocus + 1) % 3);
  menuRequestFullRedraw();
}
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
