Soundpauli/toern/toern_synths.ino

#define POLY_VOICES 3
#define INSTRUMENT_CHANNELS 2
#define MAXSLIDER 32.0 // float version of maxfilterResonance

// (1) Synth globals must not use DMAMEM on Teensy 4.x: OCRAM is cleared at boot and static
//     initializers are ignored, so waveform/pulse/volume defaults were lost.
// (2) Explicit per-channel initializers below.

#define NOTE_EMPTY INT16_MIN

unsigned long voiceStartTime[INSTRUMENT_CHANNELS][POLY_VOICES] = {
  { 0, 0, 0 },
  { 0, 0, 0 },
};

int16_t cents[INSTRUMENT_CHANNELS][POLY_VOICES] = {
  { 0, 0, 0 },
  { 0, 0, 0 },
};
int16_t semitones[INSTRUMENT_CHANNELS][POLY_VOICES] = {
  { 0, 0, 0 },
  { 0, 0, 0 },
};
int16_t pan[INSTRUMENT_CHANNELS][POLY_VOICES] = {
  { 0, 0, 0 },
  { 0, 0, 0 },
};
uint8_t volume[INSTRUMENT_CHANNELS][POLY_VOICES] = {
  { 100, 100, 100 },
  { 100, 100, 100 },
};

uint16_t attackAmp[INSTRUMENT_CHANNELS][POLY_VOICES] = {
  { 100, 100, 100 },
  { 100, 100, 100 },
};
uint16_t decayAmp[INSTRUMENT_CHANNELS][POLY_VOICES] = {
  { 100, 100, 100 },
  { 100, 100, 100 },
};
float sustainAmp[INSTRUMENT_CHANNELS][POLY_VOICES] = {
  { 1, 1, 1 },
  { 1, 1, 1 },
};
uint16_t releaseAmp[INSTRUMENT_CHANNELS][POLY_VOICES] = {
  { 100, 100, 100 },
  { 100, 100, 100 },
};

uint16_t attackFilter[INSTRUMENT_CHANNELS][POLY_VOICES] = {
  { 100, 100, 100 },
  { 100, 100, 100 },
};
uint16_t decayFilter[INSTRUMENT_CHANNELS][POLY_VOICES] = {
  { 100, 100, 100 },
  { 100, 100, 100 },
};
float sustainFilter[INSTRUMENT_CHANNELS][POLY_VOICES] = {
  { 1, 1, 1 },
  { 1, 1, 1 },
};
uint16_t releaseFilter[INSTRUMENT_CHANNELS][POLY_VOICES] = {
  { 100, 100, 100 },
  { 100, 100, 100 },
};

uint16_t cutoff[INSTRUMENT_CHANNELS][POLY_VOICES] = {
  { 1000, 1000, 1000 },
  { 1000, 1000, 1000 },
};
float resonance[INSTRUMENT_CHANNELS][POLY_VOICES] = {
  { 2.0f, 2.0f, 2.0f },
  { 2.0f, 2.0f, 2.0f },
};
float filterAmount[INSTRUMENT_CHANNELS][POLY_VOICES] = {
  { 2.0f, 2.0f, 2.0f },
  { 2.0f, 2.0f, 2.0f },
};

uint8_t waveforms[INSTRUMENT_CHANNELS][POLY_VOICES] = {
  { WAVEFORM_SAWTOOTH, WAVEFORM_SAWTOOTH, WAVEFORM_SAWTOOTH },
  { WAVEFORM_SAWTOOTH, WAVEFORM_SAWTOOTH, WAVEFORM_SAWTOOTH },
};
uint8_t waveformsArray[INSTRUMENT_CHANNELS][5] = {
  { WAVEFORM_SAWTOOTH, WAVEFORM_PULSE, WAVEFORM_SQUARE, WAVEFORM_TRIANGLE, WAVEFORM_SINE },
  { WAVEFORM_SAWTOOTH, WAVEFORM_PULSE, WAVEFORM_SQUARE, WAVEFORM_TRIANGLE, WAVEFORM_SINE },
};
float pulseWidth[INSTRUMENT_CHANNELS][POLY_VOICES] = {
  { 0.25f, 0.25f, 0.25f },
  { 0.25f, 0.25f, 0.25f },
};

// (3)(4) Empty slots use NOTE_EMPTY so MIDI note 0 is not treated as "no note".
int16_t noteArray[INSTRUMENT_CHANNELS][8] = {
  { NOTE_EMPTY, NOTE_EMPTY, NOTE_EMPTY, NOTE_EMPTY, NOTE_EMPTY, NOTE_EMPTY, NOTE_EMPTY, NOTE_EMPTY },
  { NOTE_EMPTY, NOTE_EMPTY, NOTE_EMPTY, NOTE_EMPTY, NOTE_EMPTY, NOTE_EMPTY, NOTE_EMPTY, NOTE_EMPTY },
};
int16_t notePlaying[INSTRUMENT_CHANNELS] = { 0, 0 };

static uint32_t sequencedSoundCurrentTick = 0;
static uint32_t sequencedSoundLastTick = 0;
static bool sequencedSoundLegato = false;
static bool sequencedSoundTouched[POLY_VOICES] = {};

static float synthNoteFrequency(int noteIndex) {
  if (noteIndex >= 0 && noteIndex < 108) return notesArray[noteIndex];
  // notesArray index 0 is C0. Extend the same equal-tempered tuning beyond
  // the table so preserved MIDI octaves are not flattened at either edge.
  return NOTE_C0 * powf(2.0f, (float)noteIndex / 12.0f);
}

static void setSoundVoice(int note, int ch, int velocity, int voiceIdx,
                          bool triggerEnvelope) {
  int noteIdx0 = note + semitones[ch][0];
  int noteIdx1 = note + semitones[ch][1];
  int noteIdx2 = note + semitones[ch][2];

  noteArray[ch][voiceIdx] = note;
  voiceStartTime[ch][voiceIdx] = millis();
  Swaveform1[voiceIdx]->frequency(
    synthNoteFrequency(noteIdx0) * pow(2, cents[ch][0] / 1200.0) * pow(2, random(-2, 3) / 1200.0));
  Swaveform2[voiceIdx]->frequency(
    synthNoteFrequency(noteIdx1) * pow(2, cents[ch][1] / 1200.0) * pow(2, random(-2, 3) / 1200.0));
  Swaveform3[voiceIdx]->frequency(
    synthNoteFrequency(noteIdx2) * pow(2, cents[ch][2] / 1200.0) * pow(2, random(-2, 3) / 1200.0));

  int velMidi = constrain(velocity > 0 ? velocity : defaultVelocity, 1, 127);
  float amp = mapf((float)velMidi, 1.0f, 127.0f, 0.0f, 1.0f);
  Swaveform1[voiceIdx]->amplitude(amp);
  Swaveform2[voiceIdx]->amplitude(amp);
  Swaveform3[voiceIdx]->amplitude(amp);
  if (triggerEnvelope) {
    Senvelope1[voiceIdx]->noteOn();
    Senvelope2[voiceIdx]->noteOn();
    SenvelopeFilter1[voiceIdx]->noteOn();
  }
}

// arp_synth preset (menuIndex==?) with additional parameters

void arp_synth(int ch, int p1, int p2, int p3, int p4, int p5, int p6) {
  // Default tuning and sound parameters
  octave[ch] = 5.0;
  cents[ch][0] = 7;  cents[ch][1] = -7; cents[ch][2] = 0;
  semitones[ch][0] = 0; semitones[ch][1] = 12; semitones[ch][2] = 19;
  pan[ch][0] = -70; pan[ch][1] = 70; pan[ch][2] = 0;
  volume[ch][0] = 100; volume[ch][1] = 65; volume[ch][2] = 35;

  attackAmp[ch][0] = 0;  attackAmp[ch][1] = 0;  attackAmp[ch][2] = 0;
  decayAmp[ch][0] = 0;   decayAmp[ch][1] = 0;   decayAmp[ch][2] = 0;
  sustainAmp[ch][0] = 1.0; sustainAmp[ch][1] = 1.0; sustainAmp[ch][2] = 1.0;
  releaseAmp[ch][0] = 2; releaseAmp[ch][1] = 2; releaseAmp[ch][2] = 2;

  attackFilter[ch][0] = 0;  attackFilter[ch][1] = 0;  attackFilter[ch][2] = 0;
  decayFilter[ch][0] = 0;   decayFilter[ch][1] = 0;   decayFilter[ch][2] = 0;
  sustainFilter[ch][0] = 1.0; sustainFilter[ch][1] = 1.0; sustainFilter[ch][2] = 1.0;
  releaseFilter[ch][0] = 2;  releaseFilter[ch][1] = 2;  releaseFilter[ch][2] = 2;

  // Extreme modulation mapping for filter parameters (p1, p2, p3)
  float minCutoff = 400.0,   maxCutoff = 6000.0;
  float minResonance = 0.1,  maxResonance = 5.0;
  float minFilterAmount = 1.0, maxFilterAmount = 10.0;
  float mappedCutoff       = minCutoff + (p1 / MAXSLIDER) * (maxCutoff - minCutoff);
  float mappedResonance    = minResonance + (p2 / MAXSLIDER) * (maxResonance - minResonance);
  float mappedFilterAmount = minFilterAmount + (p3 / MAXSLIDER) * (maxFilterAmount - minFilterAmount);
  cutoff[ch][0] = cutoff[ch][1] = cutoff[ch][2] = mappedCutoff;
  resonance[ch][0] = resonance[ch][1] = resonance[ch][2] = mappedResonance;
  filterAmount[ch][0] = filterAmount[ch][1] = filterAmount[ch][2] = mappedFilterAmount;

  // Default waveform settings (for voices 1–3 remain)
  waveforms[ch][0] = 1;
  waveforms[ch][1] = 1;
  waveforms[ch][2] = 0;

  // --- Additional modulation ---

  // p4 for pitch offset:
  // Map p4 (0-64) to an additional offset from -50 to +50 cents...
  // and -2 to +2 semitones.
  float offsetCents = -50.0 + (p4 / MAXSLIDER) * 100.0;  
  int offsetSemitones = (int)round(-2.0 + (p4 / MAXSLIDER) * 4.0);  
  for (int i = 0; i < 3; i++) {
      cents[ch][i] += offsetCents;
      semitones[ch][i] += offsetSemitones;
  }

  // p5 for octave override: map from 1.0 to 8.0.
  octave[ch] = 1.0 + (p5 / MAXSLIDER) * 7.0;

  // p6 for waveform of first voice: map to an integer between 0 and 7.
  int newWaveform = (int)floor((p6 / MAXSLIDER) * 8);
  waveforms[ch][0] = newWaveform;

  updateVals(ch);
}


// lead_synth preset (menuIndex==?) with additional parameters
void lead_synth(int ch, int p1, int p2, int p3, int p4, int p5, int p6) {
  octave[ch] = 4.0;
  cents[ch][0] = 0;   cents[ch][1] = -7;  cents[ch][2] = 7;
  semitones[ch][0] = 0; semitones[ch][1] = 12; semitones[ch][2] = 0;
  pan[ch][0] = 0;     pan[ch][1] = 35;    pan[ch][2] = -35;
  volume[ch][0] = 100; volume[ch][1] = 45; volume[ch][2] = 20;

  attackAmp[ch][0] = 0;  attackAmp[ch][1] = 0;  attackAmp[ch][2] = 0;
  decayAmp[ch][0] = 250; decayAmp[ch][1] = 250; decayAmp[ch][2] = 250;
  sustainAmp[ch][0] = 0; sustainAmp[ch][1] = 0; sustainAmp[ch][2] = 0;
  releaseAmp[ch][0] = 250; releaseAmp[ch][1] = 250; releaseAmp[ch][2] = 250;

  attackFilter[ch][0] = 0;  attackFilter[ch][1] = 0;  attackFilter[ch][2] = 0;
  decayFilter[ch][0] = 250;  decayFilter[ch][1] = 250;  decayFilter[ch][2] = 250;
  sustainFilter[ch][0] = 0;  sustainFilter[ch][1] = 0;  sustainFilter[ch][2] = 0;
  releaseFilter[ch][0] = 250; releaseFilter[ch][1] = 250; releaseFilter[ch][2] = 250;

  // Extreme modulation mapping for filter parameters (p1, p2, p3)
  float minCutoff = 400.0,   maxCutoff = 6000.0;
  float minResonance = 0.1,  maxResonance = 5.0;
  float minFilterAmount = 1.0, maxFilterAmount = 10.0;
  float mappedCutoff       = minCutoff + (p1 / MAXSLIDER) * (maxCutoff - minCutoff);
  float mappedResonance    = minResonance + (p2 / MAXSLIDER) * (maxResonance - minResonance);
  float mappedFilterAmount = minFilterAmount + (p3 / MAXSLIDER) * (maxFilterAmount - minFilterAmount);
  cutoff[ch][0] = cutoff[ch][1] = cutoff[ch][2] = mappedCutoff;
  resonance[ch][0] = resonance[ch][1] = resonance[ch][2] = mappedResonance;
  filterAmount[ch][0] = filterAmount[ch][1] = filterAmount[ch][2] = mappedFilterAmount;

  waveforms[ch][0] = 2;
  waveforms[ch][1] = 1;
  waveforms[ch][2] = 3;

  // --- Additional modulation ---
  float offsetCents = -50.0 + (p4 / MAXSLIDER) * 100.0;
  int offsetSemitones = (int)round(-2.0 + (p4 / MAXSLIDER) * 4.0);
  for (int i = 0; i < 3; i++) {
      cents[ch][i] += offsetCents;
      semitones[ch][i] += offsetSemitones;
  }
  octave[ch] = 1.0 + (p5 / MAXSLIDER) * 7.0;
  int newWaveform = (int)floor((p6 / MAXSLIDER) * 8);
  waveforms[ch][0] = newWaveform;

  updateVals(ch);
}


// keys_synth preset (menuIndex==1) with additional parameters
void keys_synth(int ch, int p1, int p2, int p3, int p4, int p5, int p6) {
  octave[ch] = 4.0;
  cents[ch][0] = 2;   cents[ch][1] = -2;   cents[ch][2] = 0;
  semitones[ch][0] = 0; semitones[ch][1] = 0; semitones[ch][2] = 12;
  pan[ch][0] = -100;  pan[ch][1] = 100;  pan[ch][2] = 0;
  volume[ch][0] = 100; volume[ch][1] = 100; volume[ch][2] = 100;

  attackAmp[ch][0] = 0;  attackAmp[ch][1] = 0;  attackAmp[ch][2] = 0;
  decayAmp[ch][0] = 2500; decayAmp[ch][1] = 2500; decayAmp[ch][2] = 2500;
  sustainAmp[ch][0] = 0;   sustainAmp[ch][1] = 0;   sustainAmp[ch][2] = 0;
  releaseAmp[ch][0] = 300; releaseAmp[ch][1] = 300; releaseAmp[ch][2] = 300;

  attackFilter[ch][0] = 0;  attackFilter[ch][1] = 0;  attackFilter[ch][2] = 0;
  decayFilter[ch][0] = 2500; decayFilter[ch][1] = 2500; decayFilter[ch][2] = 2500;
  sustainFilter[ch][0] = 0;  sustainFilter[ch][1] = 0;  sustainFilter[ch][2] = 0;
  releaseFilter[ch][0] = 300; releaseFilter[ch][1] = 300; releaseFilter[ch][2] = 300;

  // Extreme filter modulation (p1, p2, p3)
  float minCutoff = 400.0,   maxCutoff = 6000.0;
  float minResonance = 0.1,  maxResonance = 5.0;
  float minFilterAmount = 1.0, maxFilterAmount = 10.0;
  float mappedCutoff       = minCutoff + (p1 / MAXSLIDER) * (maxCutoff - minCutoff);
  float mappedResonance    = minResonance + (p2 / MAXSLIDER) * (maxResonance - minResonance);
  float mappedFilterAmount = minFilterAmount + (p3 / MAXSLIDER) * (maxFilterAmount - minFilterAmount);
  cutoff[ch][0] = cutoff[ch][1] = cutoff[ch][2] = mappedCutoff;
  resonance[ch][0] = resonance[ch][1] = resonance[ch][2] = mappedResonance;
  filterAmount[ch][0] = filterAmount[ch][1] = filterAmount[ch][2] = mappedFilterAmount;

  waveforms[ch][0] = 0;
  waveforms[ch][1] = 0;
  waveforms[ch][2] = 0;

  // --- Additional modulation ---
  float offsetCents = -50.0 + (p4 / MAXSLIDER) * 100.0;
  int offsetSemitones = (int)round(-2.0 + (p4 / MAXSLIDER) * 4.0);
  for (int i = 0; i < 3; i++) {
      cents[ch][i] += offsetCents;
      semitones[ch][i] += offsetSemitones;
  }
  octave[ch] = 1.0 + (p5 / MAXSLIDER) * 7.0;
  int newWaveform = (int)floor((p6 / MAXSLIDER) * 8);
  waveforms[ch][0] = newWaveform;

  updateVals(ch);
}


// pad_synth preset (menuIndex==2) with additional parameters
void pad_synth(int ch, int p1, int p2, int p3, int p4, int p5, int p6) {
  octave[ch] = 4.0;
  cents[ch][0] = 15;   cents[ch][1] = -15;  cents[ch][2] = 0;
  semitones[ch][0] = 0; semitones[ch][1] = 0;  semitones[ch][2] = 0;
  pan[ch][0] = -100;   pan[ch][1] = 100;   pan[ch][2] = 0;
  volume[ch][0] = 100; volume[ch][1] = 100; volume[ch][2] = 60;
  
  attackAmp[ch][0] = 1500; attackAmp[ch][1] = 1500; attackAmp[ch][2] = 1500;
  sustainAmp[ch][0] = 0.6;  sustainAmp[ch][1] = 0.6;  sustainAmp[ch][2] = 0.6;
  releaseAmp[ch][0] = 1500; releaseAmp[ch][1] = 1500; releaseAmp[ch][2] = 1500;
  
  attackFilter[ch][0] = 1500; attackFilter[ch][1] = 1500; attackFilter[ch][2] = 1500;
  sustainFilter[ch][0] = 0.2;  sustainFilter[ch][1] = 0.2;  sustainFilter[ch][2] = 0.2;
  releaseFilter[ch][0] = 1500; releaseFilter[ch][1] = 1500; releaseFilter[ch][2] = 1500;
  
  // Map p1 to decay amplitude (p1 modulates decay from 60 to 3000)
  float minDecay = 60.0, maxDecay = 3000.0;
  float mappedDecay = minDecay + (p1 / MAXSLIDER) * (maxDecay - minDecay);
  decayAmp[ch][0] = decayAmp[ch][1] = decayAmp[ch][2] = mappedDecay;

  // p2 for filter cutoff; p3 for filter resonance:
  float minCutoff = 400.0, maxCutoff = 6000.0;
  float mappedCutoff = minCutoff + (p2 / MAXSLIDER) * (maxCutoff - minCutoff);
  cutoff[ch][0] = cutoff[ch][1] = cutoff[ch][2] = mappedCutoff;
  float minResonance = 0.1, maxResonance = 5.0;
  float mappedResonance = minResonance + (p3 / MAXSLIDER) * (maxResonance - minResonance);
  resonance[ch][0] = resonance[ch][1] = resonance[ch][2] = mappedResonance;

  waveforms[ch][0] = 4;  waveforms[ch][1] = 4;  waveforms[ch][2] = 4;

  // --- Additional modulation ---
  float offsetCents = -50.0 + (p4 / MAXSLIDER) * 100.0;
  int offsetSemitones = (int)round(-2.0 + (p4 / MAXSLIDER) * 4.0);
  for (int i = 0; i < 3; i++) {
      cents[ch][i] += offsetCents;
      semitones[ch][i] += offsetSemitones;
  }
  octave[ch] = 1.0 + (p5 / MAXSLIDER) * 7.0;
  int newWaveform = (int)floor((p6 / MAXSLIDER) * 8);
  waveforms[ch][0] = newWaveform;

  updateVals(ch);
}


// organ_synth preset (menuIndex==6) with additional parameters
void organ_synth(int ch, int p1, int p2, int p3, int p4, int p5, int p6) {
  octave[ch] = 5.0;
  cents[ch][0] = 0;  cents[ch][1] = 0;  cents[ch][2] = 0;
  semitones[ch][0] = 0; semitones[ch][1] = 12; semitones[ch][2] = 19;
  pan[ch][0] = 0;    pan[ch][1] = 0;    pan[ch][2] = 0;
  volume[ch][0] = 85; volume[ch][1] = 70; volume[ch][2] = 55;

  attackAmp[ch][0] = 0;  attackAmp[ch][1] = 0;  attackAmp[ch][2] = 0;
  decayAmp[ch][0] = 100; decayAmp[ch][1] = 100; decayAmp[ch][2] = 100;
  sustainAmp[ch][0] = 0.1; sustainAmp[ch][1] = 0.1; sustainAmp[ch][2] = 0.1;
  releaseAmp[ch][0] = 100; releaseAmp[ch][1] = 100; releaseAmp[ch][2] = 100;

  attackFilter[ch][0] = 0;  attackFilter[ch][1] = 0;  attackFilter[ch][2] = 0;
  decayFilter[ch][0] = 100; decayFilter[ch][1] = 100; decayFilter[ch][2] = 100;
  sustainFilter[ch][0] = 0.6; sustainFilter[ch][1] = 0.6; sustainFilter[ch][2] = 0.6;
  releaseFilter[ch][0] = 100; releaseFilter[ch][1] = 100; releaseFilter[ch][2] = 100;

  // Extreme filter modulation (p1, p2, p3)
  float minCutoff = 400.0,   maxCutoff = 6000.0;
  float minResonance = 0.1,  maxResonance = 5.0;
  float minFilterAmount = 1.0, maxFilterAmount = 10.0;
  float mappedCutoff       = minCutoff + (p1 / MAXSLIDER) * (maxCutoff - minCutoff);
  float mappedResonance    = minResonance + (p2 / MAXSLIDER) * (maxResonance - minResonance);
  float mappedFilterAmount = minFilterAmount + (p3 / MAXSLIDER) * (maxFilterAmount - minFilterAmount);
  cutoff[ch][0] = cutoff[ch][1] = cutoff[ch][2] = mappedCutoff;
  resonance[ch][0] = resonance[ch][1] = resonance[ch][2] = mappedResonance;
  filterAmount[ch][0] = filterAmount[ch][1] = filterAmount[ch][2] = mappedFilterAmount;

  waveforms[ch][0] = 4;  waveforms[ch][1] = 4;  waveforms[ch][2] = 4;

  // --- Additional modulation ---
  float offsetCents = -50.0 + (p4 / MAXSLIDER) * 100.0;
  int offsetSemitones = (int)round(-2.0 + (p4 / MAXSLIDER) * 4.0);
  for (int i = 0; i < 3; i++) {
      cents[ch][i] += offsetCents;
      semitones[ch][i] += offsetSemitones;
  }
  octave[ch] = 1.0 + (p5 / MAXSLIDER) * 7.0;
  int newWaveform = (int)floor((p6 / MAXSLIDER) * 8);
  waveforms[ch][0] = newWaveform;

  updateVals(ch);
}


// flute_synth preset (menuIndex==7) with additional parameters
void flute_synth(int ch, int p1, int p2, int p3, int p4, int p5, int p6) {
  octave[ch] = 5.0;
  cents[ch][0] = -1;  cents[ch][1] = 1;  cents[ch][2] = 0;
  semitones[ch][0] = 0; semitones[ch][1] = 0; semitones[ch][2] = 12;
  pan[ch][0] = -100;  pan[ch][1] = 100;  pan[ch][2] = 0;
  volume[ch][0] = 100; volume[ch][1] = 100; volume[ch][2] = 45;

  decayAmp[ch][0] = 0; decayAmp[ch][1] = 0; decayAmp[ch][2] = 0;
  sustainAmp[ch][0] = 1.0; sustainAmp[ch][1] = 1.0; sustainAmp[ch][2] = 1.0;
  releaseAmp[ch][0] = 400; releaseAmp[ch][1] = 400; releaseAmp[ch][2] = 400;
  
  attackFilter[ch][0] = 500; attackFilter[ch][1] = 500; attackFilter[ch][2] = 500;
  decayFilter[ch][0] = 0;   decayFilter[ch][1] = 0;   decayFilter[ch][2] = 0;
  sustainFilter[ch][0] = 1.0; sustainFilter[ch][1] = 1.0; sustainFilter[ch][2] = 1.0;
  releaseFilter[ch][0] = 500; releaseFilter[ch][1] = 500; releaseFilter[ch][2] = 500;

  // p1 modulates attack amplitude (flute dynamics)
  float minAttack = 100.0, maxAttack = 2000.0;
  float mappedAttack = minAttack + (p1 / MAXSLIDER) * (maxAttack - minAttack);
  attackAmp[ch][0] = attackAmp[ch][1] = attackAmp[ch][2] = mappedAttack;

  // p2 for filter cutoff; p3 for filter resonance:
  float minCutoff = 400.0, maxCutoff = 6000.0;
  float mappedCutoff = minCutoff + (p2 / MAXSLIDER) * (maxCutoff - minCutoff);
  cutoff[ch][0] = cutoff[ch][1] = cutoff[ch][2] = mappedCutoff;
  float minResonance = 0.1, maxResonance = 5.0;
  float mappedResonance = minResonance + (p3 / MAXSLIDER) * (maxResonance - minResonance);
  resonance[ch][0] = resonance[ch][1] = resonance[ch][2] = mappedResonance;

  waveforms[ch][0] = 3;  waveforms[ch][1] = 3;  waveforms[ch][2] = 4;
  
  // --- Additional modulation ---
  float offsetCents = -50.0 + (p4 / MAXSLIDER) * 100.0;
  int offsetSemitones = (int)round(-2.0 + (p4 / MAXSLIDER) * 4.0);
  for (int i = 0; i < 3; i++) {
      cents[ch][i] += offsetCents;
      semitones[ch][i] += offsetSemitones;
  }
  octave[ch] = 1.0 + (p5 / MAXSLIDER) * 7.0;
  int newWaveform = (int)floor((p6 / MAXSLIDER) * 8);
  waveforms[ch][0] = newWaveform;

  updateVals(ch);
}


// wow_synth preset (menuIndex==9) with additional parameters
void wow_synth(int ch, int p1, int p2, int p3, int p4, int p5, int p6) {
  octave[ch] = 4.0;
  cents[ch][0] = 12; cents[ch][1] = -12; cents[ch][2] = 4;
  semitones[ch][0] = 0; semitones[ch][1] = 7; semitones[ch][2] = 19;
  pan[ch][0] = -80; pan[ch][1] = 80; pan[ch][2] = 0;
  volume[ch][0] = 100; volume[ch][1] = 100; volume[ch][2] = 100;
  attackAmp[ch][0] = 400; attackAmp[ch][1] = 400; attackAmp[ch][2] = 400;
  decayAmp[ch][0] = 4000; decayAmp[ch][1] = 4000; decayAmp[ch][2] = 4000;
  sustainAmp[ch][0] = 0.8; sustainAmp[ch][1] = 0.8; sustainAmp[ch][2] = 0.8;
  
  // p3 now is used to modulate release amp dramatically: from 10 to 1000.
  float minRelease = 10.0, maxRelease = 1000.0;
  float mappedRelease = minRelease + (p3 / MAXSLIDER) * (maxRelease - minRelease);
  releaseAmp[ch][0] = releaseAmp[ch][1] = releaseAmp[ch][2] = mappedRelease;

  attackFilter[ch][0] = 800; attackFilter[ch][1] = 800; attackFilter[ch][2] = 800;
  decayFilter[ch][0] = 6000; decayFilter[ch][1] = 6000; decayFilter[ch][2] = 6000;
  sustainFilter[ch][0] = 0.2; sustainFilter[ch][1] = 0.2; sustainFilter[ch][2] = 0.2;
  releaseFilter[ch][0] = 10;  releaseFilter[ch][1] = 10;  releaseFilter[ch][2] = 10;

  // p1 and p2 still control filter cutoff and resonance:
  float minCutoff = 400.0, maxCutoff = 6000.0;
  float mappedCutoff = minCutoff + (p1 / MAXSLIDER) * (maxCutoff - minCutoff);
  cutoff[ch][0] = cutoff[ch][1] = cutoff[ch][2] = mappedCutoff;
  float minResonance = 0.1, maxResonance = 5.0;
  float mappedResonance = minResonance + (p2 / MAXSLIDER) * (maxResonance - minResonance);
  resonance[ch][0] = resonance[ch][1] = resonance[ch][2] = mappedResonance;

  waveforms[ch][0] = 3; waveforms[ch][1] = 3; waveforms[ch][2] = 0;
  
  // --- Additional modulation ---
  float offsetCents = -50.0 + (p4 / MAXSLIDER) * 100.0;
  int offsetSemitones = (int)round(-2.0 + (p4 / MAXSLIDER) * 4.0);
  for (int i = 0; i < 3; i++) {
      cents[ch][i] += offsetCents;
      semitones[ch][i] += offsetSemitones;
  }
  octave[ch] = 1.0 + (p5 / MAXSLIDER) * 7.0;
  int newWaveform = (int)floor((p6 / MAXSLIDER) * 8);
  waveforms[ch][0] = newWaveform;

  updateVals(ch);
}


// bass_synth preset (with integrated parameters) with additional parameters
void bass_synth(int ch, int p1, int p2, int p3, int p4, int p5, int p6) {
  octave[ch] = 2.0;
  cents[ch][0] = 5;  cents[ch][1] = -5;  cents[ch][2] = 0;
  semitones[ch][0] = 0; semitones[ch][1] = 0; semitones[ch][2] = -12;
  pan[ch][0] = -100; pan[ch][1] = 100; pan[ch][2] = 0;
  volume[ch][0] = 100; volume[ch][1] = 100; volume[ch][2] = 100;

  attackAmp[ch][0] = 0;  attackAmp[ch][1] = 0;  attackAmp[ch][2] = 0;
  decayAmp[ch][0] = 400; decayAmp[ch][1] = 400; decayAmp[ch][2] = 400;
  sustainAmp[ch][0] = 0.0; sustainAmp[ch][1] = 0.0; sustainAmp[ch][2] = 0.0;
  releaseAmp[ch][0] = 10;  releaseAmp[ch][1] = 10;  releaseAmp[ch][2] = 10;

  attackFilter[ch][0] = 0;  attackFilter[ch][1] = 0;  attackFilter[ch][2] = 0;
  decayFilter[ch][0] = 250;  decayFilter[ch][1] = 250;  decayFilter[ch][2] = 250;
  sustainFilter[ch][0] = 0.0; sustainFilter[ch][1] = 0.0; sustainFilter[ch][2] = 0.0;
  releaseFilter[ch][0] = 10;  releaseFilter[ch][1] = 10;  releaseFilter[ch][2] = 10;

  // Extreme filter modulation (p1, p2, p3)
  float minCutoff = 400.0,   maxCutoff = 6000.0;
  float minResonance = 0.1,  maxResonance = 5.0;
  float minFilterAmount = 1.0, maxFilterAmount = 10.0;
  float mappedCutoff       = minCutoff + (p1 / MAXSLIDER) * (maxCutoff - minCutoff);
  float mappedResonance    = minResonance + (p2 / MAXSLIDER) * (maxResonance - minResonance);
  float mappedFilterAmount = minFilterAmount + (p3 / MAXSLIDER) * (maxFilterAmount - minFilterAmount);
  cutoff[ch][0] = cutoff[ch][1] = cutoff[ch][2] = mappedCutoff;
  resonance[ch][0] = resonance[ch][1] = resonance[ch][2] = mappedResonance;
  filterAmount[ch][0] = filterAmount[ch][1] = filterAmount[ch][2] = mappedFilterAmount;

  // Default waveform for voices
  waveforms[ch][0] = 0;  waveforms[ch][1] = 0;  waveforms[ch][2] = 1;

  // --- Additional modulation ---
  float offsetCents = -50.0 + (p4 / MAXSLIDER) * 100.0;
  int offsetSemitones = (int)round(-2.0 + (p4 / MAXSLIDER) * 4.0);
  for (int i = 0; i < 3; i++) {
      cents[ch][i] += offsetCents;
      semitones[ch][i] += offsetSemitones;
  }
  octave[ch] = 1.0 + (p5 / MAXSLIDER) * 7.0;
  int newWaveform = (int)floor((p6 / MAXSLIDER) * 8);
  waveforms[ch][0] = newWaveform;

  updateVals(ch);
}


// brass_synth preset (menuIndex==5) with additional parameters
void brass_synth(int ch, int p1, int p2, int p3, int p4, int p5, int p6) {
  octave[ch] = 4.0;
  cents[ch][0] = -7; cents[ch][1] = 7; cents[ch][2] = 0;
  semitones[ch][0] = 0; semitones[ch][1] = 0; semitones[ch][2] = -12;
  pan[ch][0] = -100;  pan[ch][1] = 100; pan[ch][2] = 0;
  volume[ch][0] = 100; volume[ch][1] = 100; volume[ch][2] = 55;

  attackAmp[ch][0] = 0;  attackAmp[ch][1] = 0;  attackAmp[ch][2] = 0;
  decayAmp[ch][0] = 2500; decayAmp[ch][1] = 2500; decayAmp[ch][2] = 2500;
  sustainAmp[ch][0] = 0.8; sustainAmp[ch][1] = 0.8; sustainAmp[ch][2] = 0.8;
  releaseAmp[ch][0] = 250; releaseAmp[ch][1] = 250; releaseAmp[ch][2] = 250;

  attackFilter[ch][0] = 100;  attackFilter[ch][1] = 100;  attackFilter[ch][2] = 100;
  decayFilter[ch][0] = 2500;  decayFilter[ch][1] = 2500;  decayFilter[ch][2] = 2500;
  sustainFilter[ch][0] = 0.8; sustainFilter[ch][1] = 0.8; sustainFilter[ch][2] = 0.8;
  releaseFilter[ch][0] = 250; releaseFilter[ch][1] = 250; releaseFilter[ch][2] = 250;

  // Extreme filter modulation (p1, p2, p3)
  float minCutoff = 400.0,   maxCutoff = 6000.0;
  float minResonance = 0.1,  maxResonance = 5.0;
  float minFilterAmount = 1.0, maxFilterAmount = 10.0;
  float mappedCutoff       = minCutoff + (p1 / MAXSLIDER) * (maxCutoff - minCutoff);
  float mappedResonance    = minResonance + (p2 / MAXSLIDER) * (maxResonance - minResonance);
  float mappedFilterAmount = minFilterAmount + (p3 / MAXSLIDER) * (maxFilterAmount - minFilterAmount);
  cutoff[ch][0] = cutoff[ch][1] = cutoff[ch][2] = mappedCutoff;
  resonance[ch][0] = resonance[ch][1] = resonance[ch][2] = mappedResonance;
  filterAmount[ch][0] = filterAmount[ch][1] = filterAmount[ch][2] = mappedFilterAmount;

  waveforms[ch][0] = 0; waveforms[ch][1] = 0; waveforms[ch][2] = 2;

  // --- Additional modulation ---
  float offsetCents = -50.0 + (p4 / MAXSLIDER) * 100.0;
  int offsetSemitones = (int)round(-2.0 + (p4 / MAXSLIDER) * 4.0);
  for (int i = 0; i < 3; i++) {
      cents[ch][i] += offsetCents;
      semitones[ch][i] += offsetSemitones;
  }
  octave[ch] = 1.0 + (p5 / MAXSLIDER) * 7.0;
  int newWaveform = (int)floor((p6 / MAXSLIDER) * 8);
  waveforms[ch][0] = newWaveform;

  updateVals(ch);
}


// chiptune_synth preset (menuIndex==8) with additional parameters
void chiptune_synth(int ch, int p1, int p2, int p3, int p4, int p5, int p6) {
  octave[ch] = 4.0;
  cents[ch][0] = 0;  cents[ch][1] = 0;  cents[ch][2] = 0;
  semitones[ch][0] = 0; semitones[ch][1] = 0; semitones[ch][2] = 12;
  pan[ch][0] = -100; pan[ch][1] = 100; pan[ch][2] = 0;
  volume[ch][0] = 100; volume[ch][1] = 100; volume[ch][2] = 10;

  attackAmp[ch][0] = 0;  attackAmp[ch][1] = 0;  attackAmp[ch][2] = 0;
  decayAmp[ch][0] = 0;  decayAmp[ch][1] = 0;  decayAmp[ch][2] = 0;
  sustainAmp[ch][0] = 1.0; sustainAmp[ch][1] = 1.0; sustainAmp[ch][2] = 1.0;
  releaseAmp[ch][0] = 100; releaseAmp[ch][1] = 100; releaseAmp[ch][2] = 100;

  attackFilter[ch][0] = 0;  attackFilter[ch][1] = 0;  attackFilter[ch][2] = 0;
  decayFilter[ch][0] = 0;  decayFilter[ch][1] = 0;  decayFilter[ch][2] = 0;
  sustainFilter[ch][0] = 1.0; sustainFilter[ch][1] = 1.0; sustainFilter[ch][2] = 1.0;
  releaseFilter[ch][0] = 100; releaseFilter[ch][1] = 100; releaseFilter[ch][2] = 100;

  // Extreme filter modulation (p1, p2, p3)
  float minCutoff = 400.0,   maxCutoff = 6000.0;
  float minResonance = 0.1,  maxResonance = 5.0;
  float minFilterAmount = 1.0, maxFilterAmount = 10.0;
  float mappedCutoff       = minCutoff + (p1 / MAXSLIDER) * (maxCutoff - minCutoff);
  float mappedResonance    = minResonance + (p2 / MAXSLIDER) * (maxResonance - minResonance);
  float mappedFilterAmount = minFilterAmount + (p3 / MAXSLIDER) * (maxFilterAmount - minFilterAmount);
  cutoff[ch][0] = cutoff[ch][1] = cutoff[ch][2] = mappedCutoff;
  resonance[ch][0] = resonance[ch][1] = resonance[ch][2] = mappedResonance;
  filterAmount[ch][0] = filterAmount[ch][1] = filterAmount[ch][2] = mappedFilterAmount;

  waveforms[ch][0] = 1; waveforms[ch][1] = 1; waveforms[ch][2] = 1;

  // --- Additional modulation ---
  float offsetCents = -50.0 + (p4 / MAXSLIDER) * 100.0;
  int offsetSemitones = (int)round(-2.0 + (p4 / MAXSLIDER) * 4.0);
  for (int i = 0; i < 3; i++) {
      cents[ch][i] += offsetCents;
      semitones[ch][i] += offsetSemitones;
  }
  octave[ch] = 1.0 + (p5 / MAXSLIDER) * 7.0;
  int newWaveform = (int)floor((p6 / MAXSLIDER) * 8);
  waveforms[ch][0] = newWaveform;

  updateVals(ch);
}



// waveforms[ch][osc] selects column 0–4 in waveformsArray (saw/pulse/square/tri/sine).
static inline uint8_t synthWaveformBeginType(int ch, int oscIdx) {
  uint8_t col = waveforms[ch][oscIdx];
  if (col > 4) col = 4;
  return waveformsArray[ch][col];
}

//–––––– updateVals() Function ––––––//
// This function updates all the audio objects based on the current global parameters.
void updateVals(int ch) {
  // Bounds check: ch must be within valid range for instrument channels (0-1)
  if (ch < 0 || ch >= INSTRUMENT_CHANNELS) {
    return;  // Invalid channel, skip to prevent array out-of-bounds access
  }

  for (int i = 0; i < POLY_VOICES; i++) {
    // Update amplitude envelopes
    Senvelope1[i]->attack(attackAmp[ch][i]);
    Senvelope1[i]->decay(decayAmp[ch][i]);
    Senvelope1[i]->sustain(sustainAmp[ch][i]);
    Senvelope1[i]->release(releaseAmp[ch][i]);

    Senvelope2[i]->attack(attackAmp[ch][i]);
    Senvelope2[i]->decay(decayAmp[ch][i]);
    Senvelope2[i]->sustain(sustainAmp[ch][i]);
    Senvelope2[i]->release(releaseAmp[ch][i]);

    // Update filter envelope
    SenvelopeFilter1[i]->attack(attackFilter[ch][i]);
    SenvelopeFilter1[i]->decay(decayFilter[ch][i]);
    SenvelopeFilter1[i]->sustain(sustainFilter[ch][i]);
    SenvelopeFilter1[i]->release(releaseFilter[ch][i]);

    Swaveform1[i]->begin(synthWaveformBeginType(ch, 0));
    Swaveform1[i]->amplitude(1.0);
    Swaveform1[i]->pulseWidth(pulseWidth[ch][0]);

    Swaveform2[i]->begin(synthWaveformBeginType(ch, 1));
    Swaveform2[i]->amplitude(1.0);
    Swaveform2[i]->pulseWidth(pulseWidth[ch][1]);

    Swaveform3[i]->begin(synthWaveformBeginType(ch, 2));
    Swaveform3[i]->amplitude(1.0);
    Swaveform3[i]->pulseWidth(pulseWidth[ch][2]);

    // Update filter settings for both ladders
    Sladder1[i]->frequency(cutoff[ch][i]);
    Sladder1[i]->octaveControl(filterAmount[ch][i]);
    Sladder1[i]->resonance(resonance[ch][i]);

    Sladder2[i]->frequency(cutoff[ch][i]);
    Sladder2[i]->octaveControl(filterAmount[ch][i]);
    Sladder2[i]->resonance(resonance[ch][i]);

    // Update mixer gains (using pan[ch] and volume[ch] to calculate gain)
    // Note: ch is already bounds-checked to be 0-1 (INSTRUMENT_CHANNELS)
    float gainMultiplier = 0.33f;
    Smixer1[i]->gain(0, max(0, (-pan[ch][0] + 100.0) * 0.005) * (volume[ch][0] / 100.0) * gainMultiplier);
    Smixer1[i]->gain(1, max(0, (-pan[ch][1] + 100.0) * 0.005) * (volume[ch][1] / 100.0) * gainMultiplier);
    Smixer1[i]->gain(2, max(0, (-pan[ch][2] + 100.0) * 0.005) * (volume[ch][2] / 100.0) * gainMultiplier);

    Smixer2[i]->gain(0, max(0, (pan[ch][0] + 100.0) * 0.005) * (volume[ch][0] / 100.0) * gainMultiplier);
    Smixer2[i]->gain(1, max(0, (pan[ch][1] + 100.0) * 0.005) * (volume[ch][1] / 100.0) * gainMultiplier);
    Smixer2[i]->gain(2, max(0, (pan[ch][2] + 100.0) * 0.005) * (volume[ch][2] / 100.0) * gainMultiplier);
  }
}

static uint8_t synthWaveformControlColumn(uint8_t rawValue) {
  uint8_t choice = constrain(
      (int)mapf(rawValue, 0, 16, 0, 3), 0, 3);
  switch (choice) {
    case 0: return 4;  // sine
    case 1: return 2;  // square
    case 2: return 0;  // saw
    default: return 3; // triangle
  }
}

static void applySynthWaveformControl(int instrument, int ch,
                                      uint8_t rawValue) {
  extern uint8_t synthInstrumentWaveDefault(int instrumentIdx);

  // The preset's displayed default means "restore the original recipe". This
  // preserves pulse oscillators even though the four-state UI groups pulse
  // with the square family.
  if (synthWaveformControlColumn(rawValue) ==
      synthWaveformControlColumn(synthInstrumentWaveDefault(instrument))) {
    return;
  }

  const bool uniformRecipe =
      waveforms[ch][0] == waveforms[ch][1] &&
      waveforms[ch][1] == waveforms[ch][2];
  const uint8_t selectedColumn = synthWaveformControlColumn(rawValue);
  waveforms[ch][0] = selectedColumn;
  if (uniformRecipe) {
    waveforms[ch][1] = selectedColumn;
    waveforms[ch][2] = selectedColumn;
  }
  updateVals(ch);
}

// Modify playSound() so that when a note is played, you store its start time.
void playSound(int note, int ch, int velocity) {
  // Bounds check: ch must be 0 or 1 (INSTRUMENT_CHANNELS = 2)
  if (ch < 0 || ch >= INSTRUMENT_CHANNELS) {
    return;  // Invalid channel, skip
  }
  extern void sidechainOnVoice(uint8_t);
  sidechainOnVoice(11);

  stopSound(note, ch);
  // Use current slot first, then advance (was: increment before use → first notes skipped voice 0).
  int voiceIdx = notePlaying[ch] % POLY_VOICES;
  notePlaying[ch] = (notePlaying[ch] + 1) % POLY_VOICES;
  setSoundVoice(note, ch, velocity, voiceIdx, true);
}

// Sequencer-only ch11 path. Consecutive steps reuse voices: equal notes hold,
// changed notes retune the oscillator while its envelope remains open.
void playSequencedSound(int note, int ch, int velocity, uint32_t tick,
                        bool allowLegato) {
  if (ch < 0 || ch >= INSTRUMENT_CHANNELS) return;

  extern void sidechainOnVoice(uint8_t);
  sidechainOnVoice(11);

  if (sequencedSoundCurrentTick != tick) {
    sequencedSoundCurrentTick = tick;
    sequencedSoundLegato =
        sequencedSoundLastTick != 0 && tick == sequencedSoundLastTick + 1;
    for (int voice = 0; voice < POLY_VOICES; voice++) {
      sequencedSoundTouched[voice] = false;
    }
  }

  if (allowLegato && sequencedSoundLegato) {
    // First preserve an identical voice (true hold).
    for (int voice = 0; voice < POLY_VOICES; voice++) {
      if (!sequencedSoundTouched[voice] && noteArray[ch][voice] == note) {
        sequencedSoundTouched[voice] = true;
        voiceStartTime[ch][voice] = millis();
        return;
      }
    }
    // Otherwise slide an unmatched voice to the new pitch without noteOn().
    for (int voice = 0; voice < POLY_VOICES; voice++) {
      if (!sequencedSoundTouched[voice] && noteArray[ch][voice] != NOTE_EMPTY) {
        sequencedSoundTouched[voice] = true;
        setSoundVoice(note, ch, velocity, voice, false);
        return;
      }
    }
  }

  // Default articulation is retrigger. Prefer reusing the matching old voice
  // so a repeated non-G/L note gets a clean attack without stealing a held tone.
  int voiceIdx = -1;
  for (int voice = 0; voice < POLY_VOICES; voice++) {
    if (!sequencedSoundTouched[voice] && noteArray[ch][voice] == note) {
      Senvelope1[voice]->noteOff();
      Senvelope2[voice]->noteOff();
      SenvelopeFilter1[voice]->noteOff();
      noteArray[ch][voice] = NOTE_EMPTY;
      voiceIdx = voice;
      break;
    }
  }
  for (int voice = 0; voice < POLY_VOICES; voice++) {
    if (voiceIdx < 0 && noteArray[ch][voice] == NOTE_EMPTY) {
      voiceIdx = voice;
      break;
    }
  }
  if (voiceIdx < 0) {
    for (int voice = 0; voice < POLY_VOICES; voice++) {
      if (!sequencedSoundTouched[voice]) {
        voiceIdx = voice;
        break;
      }
    }
  }
  if (voiceIdx < 0) voiceIdx = notePlaying[ch] % POLY_VOICES;
  if (noteArray[ch][voiceIdx] != NOTE_EMPTY) {
    Senvelope1[voiceIdx]->noteOff();
    Senvelope2[voiceIdx]->noteOff();
    SenvelopeFilter1[voiceIdx]->noteOff();
  }
  notePlaying[ch] = (voiceIdx + 1) % POLY_VOICES;
  sequencedSoundTouched[voiceIdx] = true;
  setSoundVoice(note, ch, velocity, voiceIdx, true);
}

void finishSequencedSoundTick(uint32_t tick, bool hadNotes) {
  if (hadNotes && sequencedSoundCurrentTick == tick) {
    if (sequencedSoundLegato) {
      for (int voice = 0; voice < POLY_VOICES; voice++) {
        if (!sequencedSoundTouched[voice] && noteArray[0][voice] != NOTE_EMPTY) {
          Senvelope1[voice]->noteOff();
          Senvelope2[voice]->noteOff();
          SenvelopeFilter1[voice]->noteOff();
          noteArray[0][voice] = NOTE_EMPTY;
        }
      }
    }
    sequencedSoundLastTick = tick;
    return;
  }

  if (!hadNotes && sequencedSoundLastTick != 0 &&
      tick == sequencedSoundLastTick + 1) {
    if (pressedKeyCount[11] == 0) {
      for (int voice = 0; voice < POLY_VOICES; voice++) {
        if (noteArray[0][voice] != NOTE_EMPTY) {
          Senvelope1[voice]->noteOff();
          Senvelope2[voice]->noteOff();
          SenvelopeFilter1[voice]->noteOff();
          noteArray[0][voice] = NOTE_EMPTY;
        }
      }
    }
    // A live MIDI hold owns the envelopes now; either way, the sequencer chain
    // ends so auto-off cannot remain suppressed indefinitely.
    sequencedSoundLastTick = 0;
  }
}

void resetSequencedSynthLegato() {
  sequencedSoundCurrentTick = 0;
  sequencedSoundLastTick = 0;
  sequencedSoundLegato = false;
  for (int voice = 0; voice < POLY_VOICES; voice++) {
    sequencedSoundTouched[voice] = false;
    if (noteArray[0][voice] != NOTE_EMPTY) {
      Senvelope1[voice]->noteOff();
      Senvelope2[voice]->noteOff();
      SenvelopeFilter1[voice]->noteOff();
      noteArray[0][voice] = NOTE_EMPTY;
    }
  }
  sequencedMonoSynthLastTick[13] = 0;
  sequencedMonoSynthLastTick[14] = 0;
  sequencedMonoSynthLastPitch[13] = 0;
  sequencedMonoSynthLastPitch[14] = 0;
  sequencedMonoSynthActive[13] = false;
  sequencedMonoSynthActive[14] = false;
}



// Grid preview often doesn't send note-off; we fake it after a per-instrument timeout.
// Presets with sustainAmp>0 would otherwise ring until AUTO_OFF (felt "infinite" at ~2s).
static unsigned synthAutoOffMsForInstrument(int inst) {
  static const uint16_t kMs[10] = {
    450,   // BASS   — pluck, short
    520,   // KEYS
    260,   // CHIPTUNE — chirp / staccato
    1700,  // PAD — needs long body
    750,   // WOW
    580,   // ORGAN
    520,   // FLUTE (sustain 1.0 → needs gate)
    460,   // LEAD
    480,   // ARP (sustain 1.0)
    700,   // BRASS
  };
  inst = constrain(inst, 0, 9);
  return kMs[inst];
}

// This function checks each voice and auto-offs active notes after the per-instrument gate.
void autoOffActiveNotes() {
  ////Serial.println(persistentNoteOn[11]);
if (pressedKeyCount[11]>=1) return;
  unsigned long currentTime = millis();
  int inst = constrain((int)SMP.synth_settings[11][INSTRUMENT], 0, 9);
  unsigned long offMs = synthAutoOffMsForInstrument(inst);
  for (int ch = 0; ch < 2; ch++) {
    // Sequencer ch11 voices stay open until the next step decides whether to
    // retrigger, glide/hold, or release on a gap.
    if (ch == 0 && sequencedSoundLastTick != 0) continue;
    for (int i = 0; i < POLY_VOICES; i++) {
      if (noteArray[ch][i] != NOTE_EMPTY) {  // There is an active note on this voice.
        if (currentTime - voiceStartTime[ch][i] >= offMs) {
          stopSound(noteArray[ch][i], ch);  // This will call noteOff on all envelopes for that note.
        }
      }
    }
  }
}

// Example stopSound() function (assuming noteArray[] holds the note numbers for active voices)
void stopSound(int note, int ch) {
  for (int num = 0; num < POLY_VOICES; num++) {
    if (noteArray[ch][num] == note) {
      Senvelope1[num]->noteOff();
      Senvelope2[num]->noteOff();
      SenvelopeFilter1[num]->noteOff();
      noteArray[ch][num] = NOTE_EMPTY;
    }
  }
}




void updateSynthVoice(int channel){
  
       int instrumentValue = SMP.synth_settings[channel][INSTRUMENT];
        int cutoff = SMP.synth_settings[channel][CUTOFF];
        int resonance = SMP.synth_settings[channel][RESONANCE];
        int filter = SMP.synth_settings[channel][FILTER];

        
        int semi = SMP.synth_settings[channel][SEMI];
        int cent = SMP.synth_settings[channel][CENT]; 
        int form = SMP.synth_settings[channel][FORM];

        switchSynthVoice(instrumentValue,0, cutoff, resonance, filter, semi, cent, form);
        applySynthWaveformControl(
            instrumentValue, 0,
            (uint8_t)filterSetting(channel, FILTER_WAVEFORM));

        // After the preset sets its own hardcoded ADSR, override with the user-saved slider values
        // so that the ADSR controls on the param page always take effect for ch11.
        if (channel == 11) {
          setParams(ATTACK,  11);
          setParams(DECAY,   11);
          setParams(SUSTAIN, 11);
          setParams(RELEASE, 11);
        }
}



void switchSynthVoice(int typeValue, int ch, int p1,int p2, int p3, int p4, int p5, int p6) {
    switch(typeValue) {
        case 0: bass_synth(ch,p1,p2,p3,p4,p5,p6);
            break;
        case 1: keys_synth(ch,p1,p2,p3,p4,p5,p6);
            break;
        case 2: chiptune_synth(ch,p1,p2,p3,p4,p5,p6);
            break;
        case 3: pad_synth(ch,p1,p2,p3,p4,p5,p6);
            break;
        case 4: wow_synth(ch,p1,p2,p3,p4,p5,p6);
            break;
        case 5: organ_synth(ch,p1,p2,p3,p4,p5,p6);
            break;
        case 6: flute_synth(ch,p1,p2,p3,p4,p5,p6);
            break;
        case 7: lead_synth(ch,p1,p2,p3,p4,p5,p6);
            break;
        case 8: arp_synth(ch,p1,p2,p3,p4,p5,p6);
            break;
        case 9: brass_synth(ch,p1,p2,p3,p4,p5,p6);
            break;
    }
}
