Soundpauli/toern/toern_filter.ino

// External variables
extern float detune[13]; // Global detune array for channels 1-12
extern float channelOctave[9]; // Global octave array for channels 1-8
extern uint8_t waveformsArray[2][5]; // Lives in DTCM (see toern_synths.ino); must not be DMAMEM on T4

// External functions
void handleWaveformChange(int index, unsigned int waveformType);

// --- Smooth Gain Transition State ---
#define NUM_MIXER_CHANNELS 3

struct GainTransition {
  float currentGain[NUM_MIXER_CHANNELS];
  float targetGain[NUM_MIXER_CHANNELS];
  float step[NUM_MIXER_CHANNELS];
  bool active[NUM_MIXER_CHANNELS];
};

GainTransition filterMixerTransitions[NUM_FILTERS];


// Advance one channel's smooth filter-mixer gains (dry/LP/HP crossfade).
void updateMixerGains(int i) {
  if (i < 0 || i >= NUM_FILTERS || filtermixers[i] == nullptr) return;

  for (int ch = 0; ch < NUM_MIXER_CHANNELS; ++ch) {
    if (!filterMixerTransitions[i].active[ch]) continue;
    float& cur = filterMixerTransitions[i].currentGain[ch];
    float tgt = filterMixerTransitions[i].targetGain[ch];
    float stp = filterMixerTransitions[i].step[ch];
    if (fabs(cur - tgt) <= fabs(stp)) {
      cur = tgt;
      filterMixerTransitions[i].active[ch] = false;
    } else {
      cur += stp;
    }
    filtermixers[i]->gain(ch, cur);
  }
}

// Must run for every voice with an active transition — not only GLOB.currentChannel.
// Previously only the selected channel advanced, so switching away mid-PASS crossfade
// could freeze dry/HP near 0 (silent) until a filter/EFX reset snapped targets.
void updateAllMixerGains() {
  extern const int ALL_CHANNELS[];
  extern const int NUM_ALL_CHANNELS;
  for (int n = 0; n < NUM_ALL_CHANNELS; ++n) {
    updateMixerGains(ALL_CHANNELS[n]);
  }
}



// Set a target gain for smooth transition
void setMixerGainSmooth(int index, int channel, float target, int steps = 8) {
  if (filtermixers[index] == nullptr) return;
  float cur = filterMixerTransitions[index].currentGain[channel];
  filterMixerTransitions[index].targetGain[channel] = target;
  filterMixerTransitions[index].step[channel] = (target - cur) / steps;
  filterMixerTransitions[index].active[channel] = true;
}

// Initialize transition state for a filter
void initFilterTransition(int index) {
  if (filtermixers[index] == nullptr) return;

  // Initialize with default values (channel 0 = 1.0, others = 0.0)
  filterMixerTransitions[index].currentGain[0] = 1.0;
  filterMixerTransitions[index].currentGain[1] = 0.0;
  filterMixerTransitions[index].currentGain[2] = 0.0;

  filterMixerTransitions[index].targetGain[0] = 1.0;
  filterMixerTransitions[index].targetGain[1] = 0.0;
  filterMixerTransitions[index].targetGain[2] = 0.0;

  for (int ch = 0; ch < NUM_MIXER_CHANNELS; ++ch) {
    filterMixerTransitions[index].step[ch] = 0.0;
    filterMixerTransitions[index].active[ch] = false;
  }
}


void forceAllMixerGainsToTarget() {
    extern const int ALL_CHANNELS[];
    extern const int NUM_ALL_CHANNELS;
    for (int i = 0; i < NUM_ALL_CHANNELS; ++i) {
        int idx = ALL_CHANNELS[i];
        if (filtermixers[idx] == nullptr) continue;
  
        for (int ch = 0; ch < NUM_MIXER_CHANNELS; ++ch) {
            filterMixerTransitions[idx].currentGain[ch] = filterMixerTransitions[idx].targetGain[ch];
            filterMixerTransitions[idx].active[ch] = false;
            filtermixers[idx]->gain(ch, filterMixerTransitions[idx].currentGain[ch]);
        }
    }
}

void applyVoiceCuts(int index) {
  if (index < 0 || index >= 15 || filters[index] == nullptr) return;
  float hcut = SMP.filter_settings[index][HCUT];
  float lcut = SMP.filter_settings[index][LOWCUT];
  float hz;
  if (lcut > 0.0f) {
    // SVF highpass — LCUT owns routing; 0 is off so HCUT lowpass can run.
    float s = constrain(lcut, 1.0f, (float)maxfilterResolution);
    hz = mapf(s, 1.0f, (float)maxfilterResolution, 40.0f, 2500.0f);
    setMixerGainSmooth(index, 0, 0.0, 32);
    setMixerGainSmooth(index, 1, 0.0, 32);
    setMixerGainSmooth(index, 2, 1.0, 32);
  } else {
    hz = mapf(constrain(hcut, 0.0f, (float)maxfilterResolution), 0.0f, (float)maxfilterResolution, 281.25f, 10000.0f);
    setMixerGainSmooth(index, 0, 1.0, 32);
    setMixerGainSmooth(index, 1, 0.0, 32);
    setMixerGainSmooth(index, 2, 0.0, 32);
  }
  filters[index]->frequency(hz);
}

// Refactored: setFilters combines processFilterAdjustment and updateFilterValue
void setFilters(FilterType filterType, int index, bool initial) {
  // Map encoder value to filter setting
  float mappedValue = 0.0;
  if (filterType == HCUT) mappedValue = mapf(SMP.filter_settings[index][filterType], 0, maxfilterResolution, 281.25, 10000.0);
  if (filterType == LOWCUT) mappedValue = mapf(SMP.filter_settings[index][filterType], 1, maxfilterResolution, 40.0, 2500.0);

  //if (filterType == LOWPASS) mappedValue = mapf(SMP.filter_settings[index][filterType], 0, maxfilterResolution, 0, 9000);
  //if (filterType == HIGHPASS) mappedValue = mapf(SMP.filter_settings[index][filterType], 0, maxfilterResolution, 0, 9000);

  if (filterType == SPEED) mappedValue = mapf(SMP.filter_settings[index][filterType], 0, maxfilterResolution, 0.125, 8.0);
  if (filterType == PITCH) mappedValue = mapf(SMP.filter_settings[index][filterType], 0, maxfilterResolution, 0.0, 3000.0); 
  if (filterType == OFFSET) mappedValue = mapf(SMP.filter_settings[index][filterType], 0, maxfilterResolution, 0.0, 3000.0);

  if (filterType == RES) mappedValue = mapf(SMP.filter_settings[index][filterType], 0, maxfilterResolution, 0.7, 5.0);
  if (filterType == OCTAVE) mappedValue = mapf(SMP.filter_settings[index][filterType], 0, maxfilterResolution, 0.0, 7.0);
  if (filterType == REVERB) mappedValue = mapf(SMP.filter_settings[index][filterType], 0, maxfilterResolution, 0.0, 0.79);

  if (filterType == BITCRUSHER) mappedValue = SMP.filter_settings[index][filterType];

  if (filterType == ACTIVE) mappedValue = mapf(SMP.filter_settings[index][filterType], 0, maxfilterResolution, 0, 1);


  // Now update the filter value (was updateFilterValue)
  switch (filterType) {

    case HCUT:
    case LOWCUT:
      {
        applyVoiceCuts(index);
        break;
      }

       case RES:
      {
        filters[index]->resonance(mappedValue);
        break;
      }

        case OCTAVE:
      {
        // Sample voices 1-8: one slider step = one semitone, ±2 octaves.
        // Storage 0..48 with center 24 (not the shared 0..32 filter max).
        if (index >= 1 && index <= 8) {
          int raw = constrain((int)lroundf(SMP.filter_settings[index][OCTAVE]), 0, 48);
          channelOctave[index] = (float)(raw - 24);
        } else {
          // For synth channels (13-14), use the original filter octave control
          filters[index]->octaveControl(mappedValue);
        }
        break;
      }

      case DETUNE:
      {
        if (index >= 1 && index <= 8) {
          // Fine tune within ±1 semitone (center = in tune). Applied as rate in trigger.
          detune[index] = mapf(SMP.filter_settings[index][DETUNE], 0, maxfilterResolution, -1.0f, 1.0f);
        } else if (index >= 9 && index <= 12) {
          // Legacy path for non-sample slots that still read detune[].
          detune[index] = mapf(SMP.filter_settings[index][DETUNE], 0, maxfilterResolution, -12.0f, 12.0f);
        }
        break;
      }

      case FILTER_WAVEFORM:
      {
        // Handle waveform changes for synth channels 11, 13-14
        if (index == 11) {
          // updateSynthVoice rebuilds the preset recipe, then applies WAVE to
          // osc1 or to all three oscillators when that recipe is uniform.
          extern void updateSynthVoice(int channel);
          updateSynthVoice(11);
        } else if (index >= 13 && index <= 14) {
          // Channels 13-14 use synth objects
          uint8_t waveformType =
              constrain((int)mapf(
                  filterSetting(index, FILTER_WAVEFORM),
                  0, 16, 0, 3), 0, 3) + 1;
          
          handleWaveformChange(index, waveformType);
        }
        break;
      }

    case REVERB:
      {
        if (freeverbs[index] != nullptr && freeverbs[index] != 0) {
          // Send, not a wet/dry crossfade. Comb mix saturates in the
          // effect, so room can go to 1 without wrapping into garbage.
          float verbAmount = mapf(mappedValue, 0.0f, 0.79f, 0.0f, 1.0f);
          verbAmount = constrain(verbAmount, 0.0f, 1.0f);

          float wetGain = mapf(verbAmount, 0.0f, 1.0f, 0.0f, 0.54f);
          wetGain = constrain(wetGain, 0.0f, 0.54f);

          float dryGain = mapf(verbAmount, 0.0f, 1.0f, 1.0f, 0.88f);
          dryGain = constrain(dryGain, 0.88f, 1.0f);

          if (freeverbmixers[index] != 0) {
            freeverbmixers[index]->gain(0, wetGain);
            freeverbmixers[index]->gain(3, dryGain);
          }
          if (index == 11) {
            // ch11 has no freeverbmixer: wet is synthmixer11 input 0, dry is 3.
            // Scale the send with the slider; keep dry at the voice's
            // nominal gain (original never ducked ch11 dry).
            synthmixer11.gain(0, 0.20f * verbAmount);
            synthmixer11.gain(3, 0.20f);
          }

          if (wetGain > 0.01f) {
            float dampingValue = mapf(verbAmount, 0.0f, 1.0f, 0.01f, 0.42f);
            dampingValue = constrain(dampingValue, 0.01f, 0.42f);
            freeverbs[index]->damping(dampingValue);
            float roomSize = mapf(verbAmount, 0.0f, 1.0f, 0.0f, 1.0f);
            freeverbs[index]->roomsize(roomSize);
          } else {
            // Bypass + drain tanks so the next raise starts from silence.
            freeverbs[index]->roomsize(0.0f);
            freeverbs[index]->damping(0.25f);
            if (index == 11) {
              synthmixer11.gain(0, 0.0f);
            }
          }
        }
        break;
      }
    case BITCRUSHER:
      {
        // Slider 0 is true bypass. Do not map 0→1 or sample-hold still engages.
        int slider = (int)SMP.filter_settings[index][BITCRUSHER];
        slider = constrain(slider, 0, (int)maxfilterResolution);

        float channelvolume = mapf(SMP.channelVol[index], 0, maxY, 0.0f, 1.0f);

        if (slider <= 0) {
          bitcrushers[index]->bits(16);
          bitcrushers[index]->sampleRate((float)AUDIO_SAMPLE_RATE_EXACT);
          if (amps[index] != nullptr) amps[index]->gain(channelvolume);
          break;
        }

        int mv = (int)round(mapf((float)slider, 1.0f, maxfilterResolution, 1.0f, 16.0f));
        mv = constrain(mv, 1, 16);

        // Slider 32 used to hit 1-bit / ~1 kHz. Cap at 80% of that extreme so
        // high BITC + high RVRB does not fill the comb tanks with square-wave junk.
        const float crushAmt = mapf((float)mv, 1.0f, 16.0f, 0.0f, 0.80f);
        int bitDepth = (int)round(mapf(crushAmt, 0.0f, 1.0f, 16.0f, 1.0f));
        int xsampleRate = (int)round(mapf(crushAmt, 0.0f, 1.0f,
                                          (float)AUDIO_SAMPLE_RATE_EXACT, 1000.0f));
        bitDepth = constrain(bitDepth, 4, 16);
        xsampleRate = constrain(xsampleRate, 9600, (int)AUDIO_SAMPLE_RATE_EXACT);

        bitcrushers[index]->bits(bitDepth);
        bitcrushers[index]->sampleRate((float)xsampleRate);

        float crushCompGain = mapf((float)mv, 1.0f, 16.0f, max(channelvolume, 0.1f), 0.6f);
        if (amps[index] != nullptr) amps[index]->gain(crushCompGain);
        break;
      }
    case EFX:
      {
        break;
      }
    default:
      break;
  }
}





void setFilterDefaults(int channel) {
  // Set gain values depending on channel
  AudioMixer4* mixer = nullptr;
  switch (channel) {
    case 1: mixer = &filtermixer1; break;
    case 2: mixer = &filtermixer2; break;
    case 3: mixer = &filtermixer3; break;
    case 4: mixer = &filtermixer4; break;
    case 5: mixer = &filtermixer5; break;
    case 6: mixer = &filtermixer6; break;
    case 7: mixer = &filtermixer7; break;
    case 8: mixer = &filtermixer8; break;
    case 11: mixer = &filtermixer11; break;
    case 13: mixer = &filtermixer13; break;
    case 14: mixer = &filtermixer14; break;
    default: return;  // Invalid channel
  }
  if (mixer) {
    mixer->gain(0, 1);
    for (int i = 1; i < 4; ++i) {
      mixer->gain(i, 0);
    }
  }

  SMP.filter_settings[channel][OCTAVE] = 16;  // middle = 0
  SMP.filter_settings[channel][DETUNE] = 16;  // middle = 0
  // Sample OCTV uses 0..48 (center 24); synth OCTAVE path still uses 0..32.
  SMP.filter_settings[channel][OCTAVE] = (channel >= 1 && channel <= 8) ? 24 : 16;
  filterSetting(channel, FILTER_WAVEFORM) = 8;  // SAW (value 2)
  
  // Initialize detune array for channels 1-12
  if (channel >= 1 && channel <= 12) {
    detune[channel] = 0.0; // No detune by default
  }
  
  // Initialize octave array for channels 1-8
  if (channel >= 1 && channel <= 8) {
    channelOctave[channel] = 0.0; // No octave shift by default
  }
  // EFX setting: 0 = SAMPLE mode (default for all channels)
  SMP.filter_settings[channel][EFX] = 0;
  filters[channel]->resonance(0.0);           // default resonance off
  filters[channel]->frequency(10000);

  if (freeverbs[channel] != 0 && freeverbs[channel] != nullptr) {
    freeverbs[channel]->roomsize(0);
    freeverbs[channel]->damping(0);
  }

  if (freeverbmixers[channel] != 0 && freeverbmixers[channel] != nullptr) {
    freeverbmixers[channel]->gain(0, 0);
    freeverbmixers[channel]->gain(3, 1);
  }
  bitcrushers[channel]->bits(16);
  bitcrushers[channel]->sampleRate((int)AUDIO_SAMPLE_RATE_EXACT);

  // Initialize transition state for this filter
  initFilterTransition(channel);
}
