Soundpauli/toern/toern_leds.ino

// LED Strip Visualization Module
// Ripple effects based on triggered notes/channels with audio reactivity
//
// Uses PIN 24 as a separate data line for the LED strip (independent from matrix on PIN 17).
// The strip can be connected externally via the onboard connector.

#include <FastLED.h>

// Configuration
#define LED_STRIP_PIN 24  // Separate pin for LED strip
#define LED_STRIP_DEFAULT_LENGTH 256
#define LED_STRIP_MAX_LENGTH 256
#define MAX_RIPPLES 16
#define RIPPLE_DECAY_RATE 0.92f
#define RIPPLE_SPEED 1.5f  // Fixed speed - LEDs per frame
#define AUDIO_SENSITIVITY 0.3f
#define AUDIO_MIN_THRESHOLD 0.01f

// Separate LED array for the strip (on PIN 24)
DMAMEM CRGB stripLeds[LED_STRIP_MAX_LENGTH];

// LED strip state
static int ledStripLength = LED_STRIP_DEFAULT_LENGTH;
static bool ledStripEnabled = true;

// Ripple structure
struct Ripple {
  bool active;
  float position;      // Position along strip (0.0 to stripLength)
  float intensity;    // Current intensity (0.0 to 1.0)
  uint8_t channels[4]; // Up to 4 channels that triggered this ripple (for color blending)
  uint8_t channelCount; // Number of active channels in this ripple
  float speed;        // Speed of ripple expansion
  unsigned long startTime;
};

static Ripple ripples[MAX_RIPPLES];
static float audioLevel = 0.0f;
static float smoothedAudioLevel = 0.0f;

// Forward declarations
extern bool isNowPlaying;
extern CRGB col[];

// Audio peak analyzer for output level (will be added to audioinit.h)
extern AudioAnalyzePeak peakOutput;

// Initialize LED strip visualization
// Call this AFTER FastLED.addLeds for the strip has been set up in setup()
void initLedStrip() {
  // Constrain strip length to available space
  if (ledStripLength > LED_STRIP_MAX_LENGTH) {
    ledStripLength = LED_STRIP_MAX_LENGTH;
  }
  
  // Clear all ripples
  for (int i = 0; i < MAX_RIPPLES; i++) {
    ripples[i].active = false;
    ripples[i].intensity = 0.0f;
    ripples[i].channelCount = 0;
  }
  
  // Clear strip LEDs
  for (int i = 0; i < ledStripLength; i++) {
    stripLeds[i] = CRGB::Black;
  }
  
  audioLevel = 0.0f;
  smoothedAudioLevel = 0.0f;
}

// Set LED strip length (called from menu or settings)
void setLedStripLength(int length) {
  ledStripLength = constrain(length, 1, LED_STRIP_MAX_LENGTH);
}

// Get LED strip length
int getLedStripLength() {
  return ledStripLength;
}

// Enable/disable LED strip visualization
void setLedStripEnabled(bool enabled) {
  ledStripEnabled = enabled;
  if (!enabled) {
    // Clear strip when disabled
    for (int i = 0; i < ledStripLength; i++) {
      stripLeds[i] = CRGB::Black;
    }
  }
}

// Get LED strip enabled state
bool getLedStripEnabled() {
  return ledStripEnabled;
}

// Trigger a ripple from a specific channel
// If a ripple was just created (within RIPPLE_MERGE_WINDOW_MS), add this channel to it instead
#define RIPPLE_MERGE_WINDOW_MS 50  // Merge channels triggered within 50ms

void triggerLedStripRipple(uint8_t channel) {
  if (!ledStripEnabled || !isNowPlaying) return;
  if (channel == 0 || channel > 16) return;  // Invalid channel
  
  // Check if there's a recent ripple we can add this channel to (for simultaneous triggers)
  unsigned long now = millis();
  int mergeSlot = -1;
  for (int i = 0; i < MAX_RIPPLES; i++) {
    if (ripples[i].active && 
        (now - ripples[i].startTime) < RIPPLE_MERGE_WINDOW_MS &&
        ripples[i].position < 5.0f &&  // Only merge if ripple is still near the start
        ripples[i].channelCount < 4) {  // Max 4 channels per ripple
      // Check if this channel is already in the ripple
      bool alreadyIncluded = false;
      for (int j = 0; j < ripples[i].channelCount; j++) {
        if (ripples[i].channels[j] == channel) {
          alreadyIncluded = true;
          break;
        }
      }
      if (!alreadyIncluded) {
        mergeSlot = i;
        break;
      }
    }
  }
  
  if (mergeSlot >= 0) {
    // Add channel to existing ripple
    ripples[mergeSlot].channels[ripples[mergeSlot].channelCount] = channel;
    ripples[mergeSlot].channelCount++;
    // Boost intensity slightly when multiple channels merge
    ripples[mergeSlot].intensity = min(1.0f, ripples[mergeSlot].intensity + 0.1f);
    return;
  }
  
  // Find an available ripple slot for a new ripple
  int slot = -1;
  for (int i = 0; i < MAX_RIPPLES; i++) {
    if (!ripples[i].active) {
      slot = i;
      break;
    }
  }
  
  // If all slots are full, reuse the oldest one
  if (slot == -1) {
    unsigned long oldestTime = ripples[0].startTime;
    slot = 0;
    for (int i = 1; i < MAX_RIPPLES; i++) {
      if (ripples[i].startTime < oldestTime) {
        oldestTime = ripples[i].startTime;
        slot = i;
      }
    }
  }
  
  // Initialize new ripple with fixed speed
  ripples[slot].active = true;
  ripples[slot].position = 0.0f;  // Start at beginning of strip
  ripples[slot].intensity = 1.0f;
  ripples[slot].channels[0] = channel;
  ripples[slot].channelCount = 1;
  ripples[slot].speed = RIPPLE_SPEED;  // Fixed speed for smooth travel
  ripples[slot].startTime = millis();
}
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
